ENG-MohamedEssam/universal-testing-machine/02-MCAL/03-ADC/ADC_interface.h

/************************************/
/*	Author  : Mohamed Essam			*/
/*	Date 	: 20/3/2022				*/
/*	Version : V01					*/
/************************************/
#ifndef ADC_INTERFACE_H
#define ADC_INTERFACE_H

void ADC_VoidInit(void);
u16 ADC_u16ReadChannelPoll(u16 Channel_u16Number);

#endif
