ENG-MohamedEssam/universal-testing-machine/02-MCAL/05-USART/USART_interface.h

#ifndef USART_INTERFACE_H
#define USART_INTERFACE_H

/* Defining Macros */

#define USART_U8_8_BIT_WORD					0
#define USART_U8_9_BIT_WORD					1

#define USART_U8_PARITY_DISABLED			0
#define USART_U8_PARITY_ENABLED				1

#define USART_U8_EVEN_PARITY				0
#define USART_U8_ODD_PARITY					1

#define USART_U8_PE_DISABLED				0
#define USART_U8_PE_ENABLED					1


/*******************/

void MUSART1_voidInit(void);

void MUSART1_voidTransmit(u8 *arr, u8 length);

u8 MUSART1_u8Receive(void);
u8 MUSART1_u8ReceiveNOinterrupt(void);

void MUSART1_voidSetcallBack(void (*setFunPtr)(void));
#endif
