ENG-MohamedEssam/universal-testing-machine/gui-code/icons_rc.py

# -*- coding: utf-8 -*-

# Resource object code
#
# Created by: The Resource Compiler for PyQt5 (Qt v5.15.2)
#
# WARNING! All changes made in this file will be lost!

from PyQt5 import QtCore

qt_resource_data = b"\
\x00\x00\x13\xcd\
\x89\
\x50\x4e\x47\x0d\x0a\x1a\x0a\x00\x00\x00\x0d\x49\x48\x44\x52\x00\
\x00\x00\xce\x00\x00\x00\xce\x08\x06\x00\x00\x00\x76\x1f\x3d\xc4\
\x00\x00\x00\x01\x73\x52\x47\x42\x01\xd9\xc9\x2c\x7f\x00\x00\x13\
\x87\x49\x44\x41\x54\x78\x9c\xed\xdd\x5b\x6c\x1c\xd7\x79\x07\xf0\
\xef\x9b\xcb\xee\x52\x92\x1b\xd9\xb2\x28\xc9\xb2\x15\xc5\x91\x5d\
\xdf\x63\xc7\x6e\x92\x26\x71\x10\xc7\x49\xdc\x26\x0d\x0a\x14\x75\
\x8b\x22\x4d\x9f\x82\xbc\xb4\x68\xd2\xb4\x68\x91\x56\x8d\x59\x34\
\x42\xdc\xa2\x68\xda\x24\x6d\x6c\x27\xa9\x5b\xa7\x7e\x28\x9d\x02\
\x79\x28\x8a\xbc\x04\x36\x90\x87\xc2\xb0\x54\x25\x6e\x56\x92\x45\
\x8a\xa6\x79\x13\x25\x8a\x36\xb9\xe4\x2e\xe7\x72\xce\xf9\xfa\xb0\
\xe7\x30\x43\x9a\x94\x38\xb4\x96\x3b\x3b\xfc\xff\x80\x05\x75\x59\
\x89\xb3\xc3\xf3\x9f\x73\x9d\x33\x44\x00\x00\x00\x00\x00\x00\x00\
\x00\x00\x00\x00\x00\x00\x00\x00\x00\x00\x00\x00\x00\x00\x00\x00\
\x00\x00\x00\x00\x00\x00\x00\x00\x00\x00\x00\x00\x00\x00\x70\x25\
\x22\xc2\x22\xc2\xdd\x3e\x0e\x80\x9e\x20\x22\x9e\x88\xf8\x99\xdf\
\xfb\xd9\xdf\x03\xc0\x2a\xcf\x3f\xff\x7c\xb0\xea\x8f\x96\x6b\x1c\
\x11\x09\x51\x03\x15\xc7\xea\x1f\x14\x74\x89\x88\xf8\xcc\xac\x2e\
\x5c\xb8\x70\xf3\xf5\xd7\x5f\xff\xbb\x69\x9a\xee\x32\xc6\x84\x7d\
\x7d\x7d\xf3\x13\x13\x13\xff\xc9\xcc\xff\x67\xdf\xc7\xcc\x2c\xdd\
\x3e\x5e\x80\xae\x13\x11\x8f\x88\x68\x74\x74\xf4\x23\xad\x56\xeb\
\x45\x59\x25\x8e\xe3\x93\x69\x9a\x3e\x2e\x22\x7d\xe8\xfb\x00\x10\
\xd1\xe0\xe0\xa0\x4f\x44\x74\xfc\xf8\xf1\x8f\x37\x9b\xcd\x49\x1b\
\x94\x48\x29\x95\x2a\xa5\xd2\x38\x8e\x63\x17\xa0\x37\xde\x78\xe3\
\xeb\x43\x43\x43\x55\x04\x07\xb6\x35\x17\x80\x7a\xbd\xfe\xab\x51\
\x14\x4d\xda\x7c\x24\xc6\x18\xd1\x5a\x8b\xd6\x5a\x94\x52\xa2\x94\
\x52\xc6\x98\x54\x29\x65\x26\x27\x27\xbf\x39\x30\x30\x50\xb1\xff\
\x16\x01\x82\xed\xc5\x35\xcf\xea\xf5\xfa\x6f\xc5\x71\x7c\xde\x86\
\x46\x67\x9b\x68\xc6\x98\xe5\xaf\x69\x9a\xba\x97\x11\x91\xff\x26\
\x22\x46\xb3\x0d\xb6\x15\x17\x9a\x93\x27\x4f\x7e\xac\xd9\x6c\x9e\
\x17\x11\x69\xb5\x5a\x66\x75\xdf\xc6\x18\xb3\x1c\x9e\x85\x85\x05\
\x99\x9b\x9b\x33\xb6\x29\x27\x17\x2f\x5e\xfc\x87\xcc\xff\x87\xf0\
\x40\xb9\xb9\x39\x99\x91\x91\x91\xdf\x5c\x58\x58\x98\x16\x11\xd1\
\x6d\xab\x73\xb3\x22\x38\xae\xd6\x89\xe3\x58\xe2\x38\xd6\xf6\xcf\
\x7e\xf0\xe8\xa3\x8f\xfa\x94\x09\x23\x40\xd9\xb0\x2b\xdc\x67\xce\
\x9c\x79\x28\x8e\xe3\x51\x11\x11\xa5\x94\x71\xfd\x19\x17\x94\xd5\
\xaf\x6c\x88\xec\xcb\x88\x88\xa4\x69\xaa\x2f\x5c\xb8\xf0\xcd\xc1\
\xc1\xc1\x3e\x42\x78\xa0\x6c\x44\x84\xdd\xe4\xe6\xe9\xd3\xa7\x1f\
\x71\xa1\x71\x35\xcd\x95\x82\xb3\xd6\x4b\x29\x65\x94\x52\x12\xc7\
\xb1\x7e\xe3\x8d\x37\xbe\x29\x22\xd7\x50\xa6\x46\x03\xe8\x75\xec\
\x0a\xf3\xb9\x73\xe7\x3e\x1a\xc7\xf1\x6b\xb6\xd9\xb5\x22\x34\x79\
\x82\x23\x22\x92\x24\x89\x2c\x2c\x2c\x88\x31\x26\xb5\x35\xd7\x53\
\xc7\x8f\x1f\x0f\x09\x7d\x1e\x28\x03\x57\xd3\x8c\x8c\x8c\x7c\x28\
\x8e\xe3\xba\x2d\xf4\xca\x0e\x33\x6f\x2a\x38\xd9\x97\xed\x1b\xa9\
\x38\x8e\xa3\x85\x85\x85\x6f\xcc\xcd\xcd\x5d\x4b\x08\x0f\xf4\x30\
\x16\x91\x80\x88\x68\x78\x78\xf8\x03\x49\x92\x0c\xd9\x3e\x7f\xba\
\xba\xf3\xff\x56\x5f\xd9\xff\x77\x7e\x7e\xfe\x9f\x5f\x7d\xf5\xd5\
\x1a\x86\xaa\xa1\x27\xb9\x15\x01\x67\xcf\x9e\x7d\x6f\x1c\xc7\xa7\
\xdc\xe4\xe6\x5a\xa3\x66\x6f\x35\x34\x49\x92\x88\x52\xca\x88\x48\
\xa2\x94\x4a\x5e\x7f\xfd\xf5\xbf\xf9\xdc\xe7\x3e\x87\x45\xa1\xd0\
\x5b\xb2\x6b\xcf\xa2\x28\x7a\xc5\xe6\x44\xad\x37\xdc\xfc\x56\x5f\
\xae\xc9\xe7\x82\xa4\x94\x4a\x94\x52\xff\x2e\x22\x15\x8c\xb4\x41\
\x4f\x70\x57\xf9\xa1\xa1\xa1\x77\x27\x49\xf2\xaa\x0d\x88\x5a\xd5\
\xac\xba\xea\x4d\x35\xd7\xdf\x31\x99\x6f\x32\x3b\x3b\xfb\xd7\x84\
\xfe\x0e\x14\x5d\xb6\xa6\x89\xe3\x78\xd8\x16\x68\xbd\x56\x68\xae\
\x66\x70\xd6\x08\x92\x11\x11\xa3\xb5\x4e\xb4\xd6\xdf\xcb\x1c\x1f\
\x02\x04\xc5\xe2\x0a\xe5\x4f\x7e\xf2\x93\xfb\x92\x24\x19\xb6\x7d\
\x0f\xb3\x5e\x68\x3a\x15\x9c\xd5\x94\x52\xe6\xd2\xa5\x4b\xc7\x5c\
\x9f\x0b\xe1\x81\xc2\x70\x85\xb2\x5e\xaf\xbf\x37\x4d\xd3\x33\x6e\
\x56\xdf\xf5\x3d\xd6\xd3\xc9\xe0\x2c\x2d\x2d\x89\x31\xc6\x68\xad\
\x25\x4d\xd3\xa5\xa9\xa9\xa9\x63\x22\xb2\x83\xb0\xc2\x00\x0a\x60\
\x79\x72\xf3\x95\x57\x5e\x79\x38\x8e\xe3\x57\x6d\xb9\xd5\xb2\x6a\
\xad\xd9\x56\x73\xdf\xdb\x06\xc7\x2d\x0e\xfd\x6e\xa6\xe6\x41\x78\
\x60\xeb\xd9\x79\x12\x57\xd3\x3c\x18\xc7\xf1\x69\x5b\x60\x75\xb6\
\xf0\x76\x33\x34\x99\x97\x0b\x4e\xab\xd1\x68\x7c\x35\xb3\x3c\x07\
\xcd\x36\xd8\x3a\x36\x34\x6e\x72\xf3\x23\x51\x14\xb9\xd1\xb3\x35\
\xef\xa7\xe9\x66\x70\x94\x52\xd2\x6a\xb5\xdc\x5f\xa5\x22\x22\xcd\
\x66\xf3\x89\xa7\x9f\x7e\xba\x46\x08\x0f\x6c\xa5\x4c\xf3\xec\x83\
\x6e\x19\x4d\x76\x45\x40\xb7\xad\x35\xcf\x23\x76\xa0\x20\x8e\xe3\
\xb4\xd9\x6c\x46\x73\x73\x73\xc7\x06\x07\x07\x2b\xdd\x3e\x97\xb0\
\x0d\x64\x6b\x1a\x3b\xb9\x79\xc6\x16\xd4\xc2\x84\x46\xd6\x19\x74\
\x70\x5a\xad\x96\x89\xa2\xc8\x24\x49\x12\x2f\x2d\x2d\x7d\x5b\x44\
\xaa\x22\x12\xa0\xe6\x81\x8e\x71\x35\x8d\x5d\x46\x33\x6a\xcb\x62\
\xb2\x6e\x09\xee\x92\x2b\x8d\xbc\xa5\x69\x6a\x92\x24\x49\x45\x44\
\x66\x66\x66\xfe\x84\x30\x58\x00\x9d\x32\x30\x30\xe0\x11\x11\x4d\
\x4f\x4f\x3f\xec\x86\x9c\x8b\x56\xd3\x38\x1b\x59\x65\x60\x87\xaa\
\xd3\x28\x8a\xe6\x9a\xcd\xe6\x3f\xd9\x1d\x43\x11\x1e\xb8\x7a\x5c\
\x68\xea\xf5\xfa\x7b\x5a\xad\xd6\xa8\x2d\x7c\x6a\xa3\x05\xb5\xa0\
\xc1\x59\x31\xc7\x34\x31\x31\xf1\x05\xc2\x60\x01\x5c\x2d\xee\x2a\
\xec\x6e\x0d\x48\xd3\x54\xb4\xd6\xfa\x4a\xcd\xa1\xa2\x06\x67\x9d\
\xa1\x6a\xb3\xb8\xb8\x38\x37\x39\x39\xf9\x07\x84\xf0\xc0\x5b\xe5\
\x26\x0b\xc7\xc7\xc7\x3f\xac\x94\x1a\xb1\x57\xe9\x0d\x87\xa6\x17\
\x82\xa3\xb5\x96\x46\xa3\xe1\x46\xdf\x62\x11\xf9\x1a\xa1\xcf\x03\
\x9b\x95\x59\xb0\x79\x9f\x9b\xdc\x5c\x5a\x5a\xd2\x6b\x85\xa1\x97\
\x83\xe3\x86\xab\xdd\x24\xa9\x52\x6a\x6e\x6a\x6a\xea\xb3\xb6\xcf\
\x83\x9b\xe1\x60\x63\xb2\x1b\x6b\x8c\x8f\x8f\xbf\xa7\xd5\x6a\x2d\
\xaf\x08\xc8\xde\xf3\xb2\xd1\x42\xdb\x0d\x79\x83\x93\xad\x7d\xec\
\xa6\x87\x3a\x4d\xd3\xbf\x72\xab\x23\x10\x9e\x37\xc3\x09\x59\x89\
\x45\xc4\x63\x66\x3d\x3e\x3e\x7e\xf7\x9e\x3d\x7b\x9e\xa9\x54\x2a\
\xf7\x32\x73\xca\xcc\xa1\x88\x10\x33\x13\xf3\xfa\xa7\x4d\x64\xe5\
\x83\x04\x2e\xf7\xde\x4e\x59\x7d\x0c\x79\xfe\x9d\x52\xca\x04\x41\
\xc0\x49\x92\xcc\x2c\x2e\x2e\xfe\xc5\xde\xbd\x7b\xbf\x43\x78\x4a\
\x02\x5c\x4e\x66\x72\xf3\xbe\x38\x8e\x4f\xd8\xab\x77\x9c\xa7\x16\
\xe9\xe5\x1a\x47\xda\x5b\x56\x49\xb3\xd9\xd4\xd2\x9e\x2c\xbd\x38\
\x3b\x3b\xfb\x79\x3b\x49\x8a\xe1\xea\x0c\xd4\x38\x96\x7d\x3e\x8d\
\x9e\x9c\x9c\xbc\xef\xfa\xeb\xaf\x7f\xa6\x52\xa9\xdc\x45\x44\x11\
\x11\xd5\x8c\x31\x2b\x6a\x8e\xb2\xd6\x38\xcc\x4c\x5a\x6b\xd2\x5a\
\x13\x33\x1b\xad\x35\x07\x41\xc0\xad\x56\xeb\x8b\x6f\x7b\xdb\xdb\
\xdc\xa0\x01\x6a\x1e\x04\xa7\xcd\x85\x66\x6c\x6c\xec\x97\xf6\xef\
\xdf\xff\x44\x18\x86\xef\x26\xa2\x94\x88\xdc\x3e\x65\xcb\xef\xed\
\x46\x10\xb6\x92\xfb\xac\xc6\x18\x12\x11\x13\x04\x01\xa5\x69\xfa\
\x3a\x33\x3f\x19\x04\xc1\x57\x89\x68\x89\x99\x4d\xb7\x8f\x13\xba\
\xcc\x35\x3f\xc6\xc7\xc7\xef\x89\xa2\xe8\xb4\x6d\xed\x14\x6e\x19\
\x4d\x37\x18\x63\x24\x49\x12\xe3\x16\x89\xce\xcc\xcc\x7c\x31\x7b\
\x3b\xc5\x76\xb6\xad\xdb\xac\xb6\xd9\x61\x46\x46\x46\xde\xb5\x6f\
\xdf\xbe\x67\xc2\x30\xbc\x2d\x8e\x63\xe5\x6a\x1a\x20\xe2\x36\x23\
\x22\xfa\x9a\x6b\xae\x39\x3a\x35\x35\xf5\xfb\xcc\xac\xb7\x7b\x7f\
\xa7\xdc\xed\x8e\xcb\x70\x6d\xf5\xc9\xc9\xc9\xf7\xf7\xf7\xf7\x3f\
\xc5\xcc\x77\x1a\x63\x52\x66\x0e\x7d\xdf\x2f\x7d\x93\x6c\xa3\xb2\
\xcd\x54\xad\x35\xa5\x69\xba\xd8\xd7\xd7\xf7\x1f\xcc\xfc\x59\x3b\
\x02\x89\x66\xdb\x76\xe1\xd6\x9e\x0d\x0d\x0d\xdd\xe7\x16\x6c\xc6\
\x71\xac\x36\x32\x4f\xb3\x9d\x69\xad\x97\x9f\xcf\x33\x35\x35\xf5\
\x87\x84\xe5\x39\xdb\x87\x5b\x46\xf3\xda\x6b\xaf\x7d\x50\x6b\x7d\
\xc6\xed\xf8\x6f\x67\xcf\xbb\x5d\x36\x0b\xcd\x6e\x3e\x62\x8c\x31\
\x46\xb5\x3b\x3e\x4f\xd3\xcf\xef\x53\xda\x56\x01\xda\x56\x8f\x6b\
\x77\x93\x9b\x63\x63\x63\x0f\x1c\x38\x70\xe0\xdb\x9e\xe7\xfd\x62\
\x9a\xa6\xc2\xcc\xde\x95\x26\x36\x81\xc8\xf7\xfd\xe5\x26\xae\xef\
\xfb\xbe\x52\xea\xb7\xa7\xa6\xa6\x86\x88\xe8\xab\xcc\x2c\xdb\xa9\
\xe9\xb6\x2d\x4a\x8a\xbd\x1a\x7a\xcc\xac\x27\x26\x26\xde\xb7\x77\
\xef\xde\xa7\x2b\x95\xca\x6d\xc6\x18\x4d\x44\x3e\x5d\x61\x98\x19\
\x81\xfa\x39\xb7\x7a\x42\x6c\x82\xd2\x34\x5d\x68\x34\x1a\x8f\xef\
\xd9\xb3\xe7\x6b\xcc\x1c\xb9\x8b\x53\xb7\x8f\xb3\xd3\x4a\x3f\x32\
\x22\x22\xfc\xc2\x0b\x2f\xf8\x76\x19\xcd\x87\xf7\xee\xdd\xfb\x2c\
\x33\xdf\x66\x07\x02\xb6\xfd\xb0\x6a\x5e\xee\x22\xc2\xcc\x6c\x27\
\x86\x77\xec\xd9\xb3\xe7\x58\x1c\xc7\x5f\x21\x22\xb1\x23\x6e\xb8\
\xd2\xf4\x3a\xb7\x8c\xa6\x5e\xaf\x7f\x30\x8e\xe3\xba\x69\xdf\x3a\
\x1c\x9b\xcc\x23\xd1\xaf\xf4\x6c\x1a\x58\x9b\xd6\x5a\xe2\x38\x36\
\x5a\x6b\x35\x37\x37\xf7\xfa\xfc\xfc\xfc\x51\x11\xd9\x25\x22\xec\
\x06\x60\xa0\xc7\x64\x37\xd6\x38\x7d\xfa\xf4\xfb\x97\x96\x96\x56\
\x3c\x9f\x26\xcf\xd3\xd0\xe0\xf2\xb4\xd6\x66\x69\x69\x49\x4b\xfb\
\xe9\xd8\x5f\x3e\x7e\xfc\x78\x58\xf6\x55\xd5\x65\x1e\x1c\xf0\x98\
\x59\x0d\x0d\x0d\xfd\xf2\x4d\x37\xdd\xf4\xed\x6a\xb5\x7a\xc4\xad\
\x3d\x23\xf4\x5b\xae\x0a\x37\xc7\xe3\x79\x1e\x57\xab\x55\x49\xd3\
\x34\xf5\x7d\xff\x8f\x6e\xb8\xe1\x86\x45\x66\xfe\x7b\x3b\x49\x5a\
\xca\x75\x6d\xa5\xac\x4e\x07\x07\x07\x7d\x66\xd6\xc3\xc3\xc3\x1f\
\x39\x74\xe8\xd0\xbf\x56\xab\xd5\x3b\x88\x28\x76\xa1\x81\xab\x4b\
\x44\x48\x44\xbc\x34\x4d\x03\x66\xde\x7d\xdd\x75\xd7\x3d\xd6\x68\
\x34\x1e\xb7\x2b\x0e\x4a\xb9\x0a\xa3\x74\x35\x8e\x1d\xec\xd1\xc3\
\xc3\xc3\x1f\x38\x74\xe8\xd0\xbf\x84\x61\xf8\x76\x11\x49\x98\xb9\
\xda\xed\x63\x2b\xbb\x30\x0c\xd9\x2e\x0c\xfd\x85\x4a\xa5\xf2\x67\
\x63\x63\x63\x97\x98\xf9\xef\xca\xb8\xa2\xba\x54\xed\x15\xf7\x03\
\x1a\x1b\x1b\x7b\xc4\xae\x72\x3e\x4c\x44\xcb\x43\xce\xd0\x59\xc6\
\x18\xf2\x3c\x8f\xb4\xd6\xe2\x79\x1e\x2b\xa5\xa2\x30\x0c\x9f\x63\
\xe6\xdf\xb3\x65\xad\x34\xe1\x29\x4d\x53\xcd\xce\x1f\xc8\xa9\x53\
\xa7\x3e\x74\xed\xb5\xd7\x3e\x15\x86\xe1\x61\x69\x37\xc2\x11\x9a\
\x2d\x90\x99\xdf\x21\xcf\xf3\x98\x99\x25\x0c\xc3\x1a\x11\x7d\x66\
\x6c\x6c\xec\xcf\x33\xa1\x29\xc5\xc5\xba\x14\xc1\xb1\x7d\x1a\x73\
\xe6\xcc\x99\x87\x8e\x1c\x39\xf2\x4c\xad\x56\x3b\x44\x44\x86\x31\
\x02\xd0\x35\xc6\x18\x5e\x5c\x5c\x14\xad\x35\xf5\xf7\xf7\xff\xe5\
\xc8\xc8\xc8\x51\x7b\x3b\x82\x94\x61\x65\x75\xaf\x17\x2c\x76\xb7\
\x06\x8c\x8e\x8e\x7e\xf2\xe0\xc1\x83\x4f\x05\x41\x70\x83\xdd\xa5\
\xd2\x0b\x82\x00\xa3\x67\x5b\x64\xf5\x5d\xa7\x4a\x29\x12\x11\xf2\
\x7d\x9f\xa2\x28\x92\x9d\x3b\x77\xb2\xd6\xfa\xd9\x20\x08\x3e\x63\
\xc3\xd3\xd3\xfd\x9e\x9e\x4d\xbe\x9d\xa7\xf1\x98\xd9\xfc\xec\x67\
\x3f\x7b\x68\xff\xfe\xfd\x5f\x0f\x82\xe0\x06\xad\xb5\xd1\x5a\x7b\
\xbe\x8f\x16\x5a\x37\xf9\xbe\x4f\x41\x10\x90\x31\x86\xaa\xd5\xf6\
\xb8\x8c\x52\xea\x37\x2e\x5c\xb8\x70\x54\x44\x76\x11\x56\x56\x6f\
\xbd\xec\xe4\xe6\xb9\x73\xe7\x3e\x11\xc7\xf1\xa4\xd8\xc7\x07\x26\
\x49\x82\x49\xcb\x2e\xb8\xd2\xb6\x53\xf6\xd7\xa9\xb4\x9f\x8d\xfa\
\xad\x27\x9f\x7c\x32\x14\x11\xaf\x57\xc3\xd3\x8b\x07\xbd\xbc\x85\
\xd3\xb9\x73\xe7\x1e\x3e\x78\xf0\xe0\x13\x61\x18\xbe\xb3\xbd\x74\
\xca\xf8\xcc\x4c\x9e\xd7\xb3\x15\x69\xcf\xba\xdc\x06\x21\xc6\x18\
\x37\xe2\x26\x44\xa4\x95\x52\xad\xf9\xf9\xf9\x63\xfb\xf6\xed\xfb\
\x5b\xea\xd1\x0d\x40\x7a\x2a\x38\xf6\xea\xe4\x33\xb3\x3a\x7b\xf6\
\xec\xaf\x1d\x3e\x7c\xf8\x1f\xc3\x30\xbc\x39\x49\x92\x34\x0c\xc3\
\xd0\x8e\xe8\x74\xfb\x30\xb7\xa5\x2b\x05\x87\x6c\xf3\xcd\x18\x23\
\xcc\xcc\x51\x14\x2d\x7a\x9e\xf7\xdd\x6a\xb5\xfa\x25\xbb\x31\x8a\
\xee\xa5\xf0\xf4\x54\x29\xb3\xab\x9c\x55\xbd\x5e\xff\x95\x43\x87\
\x0e\x3d\x15\x04\xc1\xcd\xc6\x98\x34\x08\x82\xd0\xfd\x70\xa0\x78\
\x3c\xcf\x23\x66\x26\xbb\x9a\x9a\xb5\xd6\x52\xab\xd5\xfa\xaa\xd5\
\xea\xe7\x67\x67\x67\xff\x98\x99\x55\xaf\x5d\xc4\x7b\xa6\x07\x2d\
\x22\xde\x3b\xde\xf1\x0e\x7d\xea\xd4\xa9\x4f\xde\x7c\xf3\xcd\x4f\
\xd4\x6a\xb5\x1b\xd3\x34\x55\x9e\xe7\xad\xd8\x61\x13\xa3\x68\xc5\
\x97\xb9\x25\x41\x11\xd1\xfb\x8e\x1e\x3d\x7a\x30\x0c\xc3\x1f\x32\
\x33\xbf\xf0\xc2\x0b\x3d\x53\xeb\x14\x9e\x5b\xa2\xfe\xd3\x9f\xfe\
\xf4\xe1\x66\xb3\x79\x5e\xda\xb7\xf1\xea\xec\xad\x01\x58\xc9\xdc\
\x5d\x79\x77\x0d\x8d\xe3\x58\x94\x52\x12\x45\x91\x88\x88\x5c\xbc\
\x78\xf1\x4b\x6e\xa4\xb4\xdb\xe5\x6d\x23\x0a\x7f\x79\x76\x1d\xc7\
\x13\x27\x4e\x3c\x72\xc7\x1d\x77\x7c\xa7\x56\xab\xdd\xe8\xee\xdc\
\x74\x33\xd5\x99\x9b\xab\xba\x7d\xb8\xdb\xd6\xe5\xfa\x38\xd9\x9f\
\x93\x7b\x5f\x66\xe3\x43\x09\x82\x40\x96\x96\x96\x92\x8b\x17\x2f\
\x7e\xe5\xf0\xe1\xc3\xc7\x7a\x61\xb0\xa0\xd0\xe9\x1e\x18\x18\xf0\
\x98\x59\xce\x9c\x39\xf3\xe8\x9d\x77\xde\xf9\x6f\x61\x18\xde\x68\
\x8c\x59\xb1\x8c\x06\x4d\xb4\xde\xb0\xfa\xe2\xe6\xbe\xfa\xbe\xcf\
\x49\x92\x78\xd5\x6a\xb5\x76\xd3\x4d\x37\x3d\x76\xfe\xfc\xf9\x6f\
\xd9\xd0\x14\xfa\x07\x5a\xd8\x83\x73\x93\x9b\x2f\xbd\xf4\xd2\x27\
\xee\xb9\xe7\x9e\xef\x54\x2a\x95\x03\x22\x62\xb2\x61\x5f\x5d\xe3\
\x40\xf7\x5c\xa9\xc6\x59\xef\xbd\x22\x42\x69\x9a\x12\x11\x49\xb5\
\x5a\x65\xa5\x94\x9a\x99\x99\x79\xec\xc0\x81\x03\xee\xb6\x84\x42\
\xd6\x3e\x45\xbc\xad\x60\x79\x9e\x66\x74\x74\xf4\xd3\xfb\xf6\xed\
\xfb\x7a\x10\x04\xd7\xd9\x76\xb4\x87\xe1\xe6\xf2\x09\xc3\x90\x3c\
\xcf\x63\xad\x35\x11\x91\x77\xe0\xc0\x81\x63\x5a\xeb\x77\x0d\x0c\
\x0c\x7c\x9a\x99\xd5\x76\xda\x3d\x67\xb3\xd8\xed\x7b\xf6\xf2\xcb\
\x2f\xff\xfa\xd2\xd2\xd2\x94\x0d\x8c\x5e\xdd\x09\x85\xde\xb7\xce\
\xc0\x81\x11\x11\x89\xa2\x28\x99\x98\x98\xf8\x4a\xbd\x5e\xaf\xb8\
\xb2\xd1\xdd\xa2\x59\x60\x6e\x44\xe5\xe4\xc9\x93\x1f\x6b\x36\x9b\
\xe3\x26\xf3\xcc\xcd\xd5\x27\x1b\x7a\xdf\x7a\x3f\xc7\x34\x4d\x8d\
\x52\xca\x44\x51\x94\x9e\x3f\x7f\xfe\x4f\xdd\xf2\x9c\x22\x85\xa7\
\x30\x07\xe2\xaa\xe3\x89\x89\x89\x5b\x77\xef\xde\xfd\xfd\x9d\x3b\
\x77\xde\x1d\x45\x51\x1a\x04\x41\x18\x04\x45\x6c\x51\x42\xa7\xa4\
\x69\x4a\x69\x9a\xea\x1d\x3b\x76\x50\x1c\xc7\xaf\x5f\xba\x74\xe9\
\x77\x6e\xbc\xf1\xc6\x1f\x15\xa9\xc9\x56\xa4\x0e\x03\x13\x11\xf5\
\xf7\xf7\x7f\x74\xe7\xce\x9d\x77\x13\x51\xe4\xfb\x7e\x88\x8e\xff\
\xf6\x13\x86\x21\xed\xd8\xb1\xc3\x17\x11\x5d\xad\x56\xf7\xee\xd9\
\xb3\xe7\xc3\x76\xf3\x95\x42\x84\x86\x8a\x12\x1c\xb7\x4f\x00\xb5\
\xaf\x36\x7b\x45\xc4\x28\xa5\x7c\xdf\xf7\xc9\xf3\x3c\xb7\x19\xc4\
\xa6\x9f\x34\x06\xbd\x25\xf3\xb3\x66\x69\x3f\xed\x7b\xf7\xfd\xf7\
\xdf\xef\x53\x81\x6e\x45\x28\x44\x70\xb2\xc3\x8d\x22\x12\x63\x6e\
\x06\x32\x98\x88\x38\x8a\xa2\x42\x15\x86\x42\x04\x87\xec\xe3\x04\
\x89\x88\x6a\xb5\xda\xc5\xf6\xba\x40\xaf\x30\xd5\x32\x6c\x3d\x7b\
\xd1\x34\xcc\x2c\x3b\x77\xee\x9c\xae\xd7\xeb\x69\x91\xe6\x74\x0a\
\x13\x9c\xe7\x9e\x7b\x8e\x88\x88\x5e\x7c\xf1\xc5\x1f\x2d\x2c\x2c\
\xfc\x0f\x33\x57\x99\x59\xb9\x87\xb9\xda\x67\x52\x76\xad\xb9\x96\
\x24\x09\x29\xa5\xba\xf2\xbd\x3b\xa9\x68\x9f\x49\x44\x48\x6b\x4d\
\x51\x14\x89\x31\xa6\x9a\x24\x89\x34\x1a\x8d\x93\x76\xb3\x8f\xc2\
\x94\xd7\x42\x55\x7f\x6e\xd4\xe4\xc7\x3f\xfe\xf1\x7b\xef\xbd\xf7\
\xde\xa7\x77\xed\xda\x75\x7b\xb7\x8f\xa9\xec\xa2\x28\x22\xcf\xf3\
\xa8\x52\xa9\x6c\xe0\xdd\x5b\xc3\xad\x06\x69\x34\x1a\x17\x2f\x5c\
\xb8\xf0\x85\x46\xa3\xf1\xfd\xfb\xef\xbf\x5f\x17\x69\x70\xa0\x50\
\xe3\xbc\xcc\x6c\x06\x06\x06\xbc\x07\x1f\x7c\xf0\xc5\x97\x5f\x7e\
\xf9\x33\xbb\x77\xef\xfe\xf2\xfe\xfd\xfb\x1f\x0a\xc3\x70\xf9\x7e\
\x9b\xec\x53\x91\x57\xff\xf3\x35\xfe\xbf\x95\xbf\xf7\x78\xbd\x9d\
\xbd\x96\xff\x34\xd3\x14\x58\xfe\x9a\xe9\x6f\x05\x22\x52\x2d\x4b\
\xdf\x4b\x44\x96\x03\x23\x22\x29\x11\xa9\xcc\x3a\xb1\xec\x99\xca\
\xfe\x3a\xfb\x10\xa9\x37\x9d\x88\x75\x3a\xef\x57\x6c\x26\xd8\xef\
\x2b\xd4\x7e\x64\xa2\x99\x9d\x9d\x3d\xb1\xb8\xb8\xf8\xf8\xad\xb7\
\xde\xfa\xc3\xfc\x9f\xac\xf3\x0a\x5f\x02\x86\x86\x86\xde\xa9\xb5\
\xbe\x96\xda\xcd\x8a\x37\x1d\xaf\xd6\xda\x73\x7f\xb7\x63\xc7\x0e\
\x8e\xe3\xd8\xd7\x5a\xb3\xdd\x1a\x6a\xc5\xfb\x35\x6b\xf6\xc5\x5f\
\x0e\x84\xf8\x22\x9e\xf1\x8c\xe7\x79\x9a\x88\xc4\xf7\x7d\xe3\xfb\
\xbe\x11\x11\x09\x82\xc0\x18\x63\x4c\x10\x04\xc6\x7e\x1f\xc5\xcc\
\x1f\x3f\x72\xe4\xc8\xd7\x98\xb9\x30\x4d\x86\xb7\xca\xde\x17\x43\
\xa3\xa3\xa3\xdf\x6b\xb5\x5a\xdf\xa8\x56\xab\x6b\x3d\xdb\x66\x79\
\x4f\x34\xa5\x14\x3b\x4a\x29\x56\x4a\x79\x61\xd8\xde\xe5\x56\x6b\
\xed\xb9\x9f\x51\x76\x6b\x2e\x7b\x3e\xc5\x9d\x5b\xa5\x14\xd5\x6a\
\x35\xe3\xfe\x2e\xfb\x1e\x22\x92\xbe\xbe\xbe\xe6\xf4\xf4\xf4\xab\
\x0f\x3c\xf0\x40\xba\x25\x27\x61\x13\x0a\x55\xe3\xac\xe5\x96\x5b\
\x6e\x39\xd7\xed\x63\x70\xce\x9e\x3d\xdb\x6f\x87\xcd\x4b\x13\x1c\
\x3b\xdc\x2f\xbe\xef\x0f\xdf\x75\xd7\x5d\x2f\x75\xfb\x78\x7a\x45\
\xe1\x83\x63\x9b\x06\xdd\x3e\x06\x22\x22\x9a\x9a\x9a\xd2\x65\xda\
\xc6\x35\xcb\x06\x88\xd7\x68\xa6\x75\x45\x51\x46\xcf\xd6\xd3\x0b\
\xc1\x91\xa2\xf4\x29\xc6\xc7\xc7\x8b\x35\x04\x75\xf5\xb0\xb4\xc7\
\x7a\xc5\x76\xcc\x0b\x5d\x68\x8b\xa0\x34\x4d\x8e\xad\x90\x24\x89\
\x2e\x4a\xed\xd7\x01\x85\x19\xb1\xea\x05\x08\x4e\x0e\xb5\x5a\xad\
\xa7\xb6\x30\xda\x28\x66\x16\xbb\x71\x06\x6c\x10\x82\x93\x83\xdd\
\xeb\xa0\x74\xc1\xa1\x76\x1f\xa7\xf4\x4f\x8a\xbe\x9a\x10\x9c\x1c\
\xc2\x30\x34\x52\xd2\xb6\x9a\xbd\x2d\x1d\x36\x08\xc1\xc9\x21\x0c\
\x43\x53\xd6\x1a\xa7\xc4\x9f\xab\x23\x10\x9c\x1c\x6c\x6d\x53\xc6\
\x02\x26\x58\x54\x9b\x0f\x82\x93\x4f\x19\x43\x43\xd4\x9e\xf5\x2f\
\xed\x67\xeb\x04\x04\x27\x07\x37\xd7\xd1\xed\xe3\xe8\x04\xd4\x38\
\xf9\x20\x38\x39\x94\xf9\xd1\x88\x22\x82\x51\xb5\x1c\x10\x9c\xfc\
\x4a\x19\x9e\x32\x5f\x14\x3a\x01\xc1\x01\xa2\x76\x1f\x07\xc1\xc9\
\x01\xc1\x01\x22\xfb\xd0\x27\xd8\x38\x04\x27\x1f\x5c\x95\x81\x08\
\xc1\x81\x0c\x94\x85\x1c\x70\xb2\x00\x36\x01\xc1\x01\xa2\xb5\xf7\
\x70\x80\xcb\x40\x70\x00\x36\x01\xc1\xc9\xaf\x94\x2b\x07\x4a\xfc\
\xb9\x3a\x02\xc1\xc9\xa7\xb4\x85\x0b\x4b\x6e\xf2\x41\x70\x80\xa8\
\xbd\x72\x00\x4b\x6e\x72\x40\x70\x72\x28\xf1\x6d\x05\x44\x44\x08\
\x4e\x0e\x08\x4e\x0e\xd5\x6a\xb5\xac\xa1\x91\xb2\xde\xd9\xda\x29\
\x08\x4e\x0e\x8d\x46\x83\xca\x5a\xe3\xa0\x8f\x93\x0f\x82\x93\x43\
\xa5\x52\x29\x65\x53\x4d\x44\xc8\xf3\x3c\xec\x72\x93\x03\x82\x93\
\x4f\x69\x5b\x34\x5a\x6b\xd4\x38\x39\x20\x38\xf9\x95\x31\x39\x62\
\x37\x22\x81\x0d\x42\x70\x80\x08\x7b\x0e\xe4\x86\xe0\x80\x83\xe0\
\xe4\x80\xe0\xe4\x50\xda\x0e\x4e\xc9\x3f\x5b\x27\x20\x38\xf9\x95\
\xb5\x80\x95\xf5\x73\x75\x04\x82\x03\xb0\x09\x08\x0e\xc0\x26\x20\
\x38\xf9\x95\xb2\x49\x53\xa6\xe7\x9a\x6e\x05\x9c\xac\x9c\xca\xba\
\xfd\x98\xef\xfb\xe5\xfc\x60\x1d\x82\xe0\xe4\x57\xc6\x02\xc6\xc6\
\x18\xec\x0f\x95\x03\x82\x93\x43\xc9\x77\xbb\x2c\xf3\x67\xbb\xea\
\x10\x9c\xfc\xca\x5a\xc0\x50\x16\x72\xc0\xc9\xca\xa7\x94\xa1\x61\
\x66\x12\x91\x5e\x78\x02\x79\x61\x20\x38\x39\x54\xab\xd5\x6e\x1f\
\x42\xa7\xa0\x8f\x93\x13\x82\x93\x43\x92\x24\x5c\xd6\x5a\x07\xc1\
\xc9\x07\xc1\xc9\xa7\x94\xa1\xa1\x76\x73\x0d\xc1\xc9\x01\xc1\x01\
\x22\x22\x52\x4a\xa1\x8f\x93\x03\x82\x93\x83\x1d\x8e\x2e\x63\xad\
\xc3\x98\x00\xcd\x07\xc1\xc9\xa7\xcc\x85\xab\xcc\x9f\xed\xaa\x43\
\x70\x72\x48\xd3\xb4\xac\x35\x0e\xe4\x84\xe0\x00\x51\x7b\x54\x0d\
\x65\x21\x07\x9c\xac\x7c\x50\xe3\x00\x11\x82\x03\xb0\x39\x08\x4e\
\x0e\xe8\xe3\x80\x83\xe0\x00\x51\x7b\xb3\x0e\xcc\xe3\xe4\x80\xe0\
\xe4\x24\x22\xa8\x71\x00\xc1\xc9\x03\xf7\xe3\x80\x83\xe0\xe4\x57\
\xca\x02\x26\x22\x28\x0b\x39\xe0\x64\xe5\x53\xca\xd0\xd8\xcf\x85\
\x45\x9e\x39\x20\x38\xf9\x95\x32\x3c\xa8\x71\xf2\xc1\xc9\x02\xa2\
\x76\x70\x50\xe3\xe4\x80\xe0\xe4\x50\xe6\xc1\x01\xdc\xc8\x96\x0f\
\x82\x93\x5f\x29\xc3\x83\x1b\xd9\xf2\x41\x70\x72\x50\x4a\x95\xf6\
\x7c\xa1\x8f\x93\x0f\x4e\x56\x3e\xa5\xac\x6d\x08\x35\x4e\x6e\x08\
\x4e\x0e\x9e\xe7\x79\x65\x0d\x8f\x31\xa6\x94\x9f\xab\x53\x10\x9c\
\x7c\x4a\x5b\xb8\xb0\xe9\x7a\x3e\x38\x59\x39\x30\xb3\x57\xd6\x81\
\x35\xd4\x38\xf9\x20\x38\x39\x24\x49\x52\xda\x27\x33\x33\x73\x69\
\x3f\x5b\x27\x20\x38\x39\x84\x61\xd8\xed\x43\xe8\x98\x32\xcf\x51\
\x75\x02\x82\x93\x43\x89\xb7\x87\xc2\x9e\x03\x39\xe1\x64\x01\x6c\
\x02\x82\x93\x43\x99\x27\x40\xcb\xfa\x88\xc6\x4e\x29\x73\x41\x00\
\xe8\x18\x04\x07\x60\x13\x10\x9c\x7c\xd0\x9c\x01\x22\x04\x07\x32\
\x4a\x39\x5a\xd8\x29\x08\x4e\x0e\xcc\x9c\x1a\x83\x79\x42\x40\x70\
\x72\xf3\x3c\x8f\x45\x84\x44\xca\xd1\x6a\xb3\x17\x02\x21\xa2\xf9\
\x6e\x1f\x4b\x2f\x41\x70\x72\xe8\xeb\xeb\x9b\x8b\xe3\x38\x32\xc6\
\x68\xfa\x79\xa1\xeb\x69\x5a\x6b\xa3\xb5\x66\x11\x39\xd1\xed\x63\
\xe9\x25\x08\x4e\x0e\xfd\xfd\xfd\xa3\xd3\xd3\xd3\x2f\xf9\xbe\xef\
\x8b\x48\x6a\x8c\x91\x4c\xed\x23\x9b\x7c\x6d\xd6\xa6\xbe\x5f\xe6\
\x58\x0d\x11\xa5\x61\x18\x7a\xad\x56\x6b\xd6\xf7\xfd\x13\xd4\x6e\
\x8e\x96\xa3\x2a\xed\x30\x04\x27\x07\x66\x36\xcd\x66\xf3\xb1\x56\
\xab\xf5\xbf\x9e\xe7\x85\x41\x10\x30\x11\xa5\xf6\xa5\x6d\x61\x74\
\x5f\x37\xfa\x4a\x37\xf9\xca\xf3\x3d\x96\x5f\xcc\xec\x8e\xd5\x23\
\xa2\xb0\xd9\x6c\x4e\xcf\xcf\xcf\x7f\xe1\xc8\x91\x23\xe3\xdd\x3e\
\xbf\x50\x72\xc7\x8f\x1f\xbf\x7b\x7e\x7e\xfe\x07\x33\x33\x33\xd3\
\x92\x61\x8c\xb9\xe2\xab\x53\xb4\xd6\x62\x8c\x11\xad\xf5\x9b\x5e\
\x4a\x29\x51\x4a\xad\x78\xff\xfc\xfc\xfc\x64\xa3\xd1\xf8\xaf\xd3\
\xa7\x4f\x3f\x42\xd8\xda\x37\x37\x9c\xac\x9c\x44\xc4\x67\x66\xfd\
\xec\xb3\xcf\x5e\x7b\xfb\xed\xb7\xdf\x76\xcb\x2d\xb7\xdc\xb0\x6b\
\xd7\xae\x5a\xa3\xd1\x10\xad\xb5\xa4\x69\xea\xfb\xbe\x4f\x5a\x6b\
\x26\x22\xf2\xfd\x15\x77\x24\xaf\x38\xdf\xb5\x5a\x8d\x98\xf9\x4d\
\x4b\xae\x3d\xcf\x13\xca\xdc\x23\x63\x57\x65\x7b\xf6\xef\xc8\x18\
\x43\x51\x14\xa5\x44\xc4\x5a\x6b\x22\x22\xc9\x7c\x15\xdf\xf7\x97\
\x9b\x81\xf6\xff\x32\xbe\xef\x8b\xd6\x9a\x2a\x95\x4a\x20\x22\xc9\
\xc4\xc4\xc4\xf8\xf0\xf0\xf0\xd0\xa7\x3e\xf5\xa9\x4b\xee\x33\x75\
\xf2\xbc\x01\x94\x6a\x63\x8b\xc1\xc1\x41\xec\x35\x00\x5b\x67\x60\
\x60\xc0\x13\x11\xff\xf9\xe7\x9f\x0f\x44\xc4\xb7\x2f\xaf\xc8\xaf\
\xc1\xc1\x41\x77\x9c\xfe\xe0\xe0\xa0\x3f\x30\x30\x50\x9a\x0b\x00\
\x00\x00\x00\x00\x00\x00\x00\x00\x00\x00\x00\x00\x00\x00\x00\x00\
\x00\x00\x00\x00\x00\x00\x00\x00\x00\x00\x00\x00\x00\x00\x00\x00\
\x00\x00\x00\x00\x6c\x6b\xff\x0f\x73\x7f\xe3\x0c\xd9\xbf\xa8\xb7\
\x00\x00\x00\x00\x49\x45\x4e\x44\xae\x42\x60\x82\
\x00\x00\x10\x2c\
\x89\
\x50\x4e\x47\x0d\x0a\x1a\x0a\x00\x00\x00\x0d\x49\x48\x44\x52\x00\
\x00\x00\xce\x00\x00\x00\xce\x08\x04\x00\x00\x00\xdc\x16\xf5\x4f\
\x00\x00\x00\x04\x67\x41\x4d\x41\x00\x00\xb1\x8f\x0b\xfc\x61\x05\
\x00\x00\x00\x20\x63\x48\x52\x4d\x00\x00\x7a\x26\x00\x00\x80\x84\
\x00\x00\xfa\x00\x00\x00\x80\xe8\x00\x00\x75\x30\x00\x00\xea\x60\
\x00\x00\x3a\x98\x00\x00\x17\x70\x9c\xba\x51\x3c\x00\x00\x00\x02\
\x62\x4b\x47\x44\x00\xff\x87\x8f\xcc\xbf\x00\x00\x00\x07\x74\x49\
\x4d\x45\x07\xe6\x03\x18\x0c\x00\x1a\x2a\xbc\x57\x81\x00\x00\x00\
\x01\x6f\x72\x4e\x54\x01\xcf\xa2\x77\x9a\x00\x00\x0f\x27\x49\x44\
\x41\x54\x78\xda\xed\x9d\x7b\x90\x1c\xc5\x7d\xc7\xbf\x3d\xb3\x7b\
\xa7\x67\x2c\xcb\x31\x8e\x9d\xc2\x29\xfc\x28\x10\x48\xa2\x2c\x19\
\x88\xb1\x43\x10\x38\x06\x51\x42\x52\xb0\x7d\xa0\xb8\xc4\xc3\xa5\
\x60\x07\xe2\xc4\x55\xc9\x1f\xa9\x94\x2b\xb9\x38\xae\xf2\x5f\xc9\
\x1f\x2e\x27\xe5\x54\xd9\x04\xbb\x12\x08\x17\x8c\xc1\x08\x74\xb2\
\x1e\x87\x90\xc4\x21\x74\x42\x96\xc4\x9d\x64\x49\xb1\x04\x25\xa1\
\xc7\xdd\xe9\xf6\x79\x7b\xbb\xd3\xdd\xdf\xfc\x31\x7b\x77\x73\x77\
\xbb\xa7\x5d\x69\x76\xb6\x77\xb7\x3f\x5b\x75\x3b\xb7\x3b\xdb\x33\
\xd3\x9f\xe9\x9e\x9e\xee\xdf\xcc\x00\x16\x8b\xc5\x62\xb1\x58\x2c\
\x16\x8b\xc5\x62\xb1\x58\x2c\x16\x8b\xc5\x62\xb1\x58\x2c\x16\x8b\
\xc5\x62\xb1\x58\x2c\x16\x8b\xc5\xd2\x74\x88\x7a\xaf\xc0\xe5\xa0\
\xf8\xa7\x9a\xad\xe3\x3f\x52\xb0\xde\xdb\xd7\xb0\x30\x46\xb7\xa6\
\xe9\x8b\xbe\x38\x0d\xde\x3d\x63\xf5\x5e\x81\x72\x50\xc0\x15\x12\
\xd8\x38\x7f\xc9\xbc\x94\x04\x3e\x80\xbc\x68\x13\x40\x61\x22\x33\
\xf3\xa2\x9d\x40\xdc\xf5\xca\x64\x6f\x9c\x42\x16\x04\xd0\x56\x2c\
\x1d\x69\x00\x40\x3b\x81\x76\xe6\xc5\xfc\x58\x56\x8a\x4b\xf0\x00\
\x3a\x42\xd7\x7b\x6b\x4b\x63\xe8\x7e\x43\x21\x08\xf4\xad\x5f\xb6\
\x62\xf4\xba\xfc\x07\x9d\x02\x20\x04\x84\x16\xfe\x7e\xae\x04\x00\
\x08\xe1\xd0\xa1\x6c\x0b\xee\xfb\xce\x44\x35\x45\x00\x4e\x61\x6a\
\xa2\x00\x20\x48\x38\x5a\x3b\x6c\x8b\x8f\xcd\x3b\xfd\xde\x3b\x37\
\x3c\x0d\x43\xd5\x18\x0b\x1d\x2e\x1c\xfb\xe1\x60\x8e\x35\x66\x8c\
\xb9\x67\x07\x3f\x66\xea\x2e\x6a\x68\xb5\x26\x74\xdf\x13\x2b\x9f\
\x6c\x27\x0b\x70\x8a\xbb\x3c\x04\x4a\x15\x74\x22\x78\x4c\x17\x81\
\xcf\xfd\xef\x4a\x1f\xf1\x05\x1c\x10\x42\xb7\xb9\xe2\xa1\x61\x87\
\x1b\xcc\x6c\x18\x18\xba\xcf\x0c\x7e\xb4\x7d\x60\xc1\x7c\xe1\x4e\
\xaa\x29\xbf\xc2\xe5\xe5\x4c\xff\x36\xf8\x89\x3f\x27\xe9\xca\x4c\
\xfc\xc4\x9d\x2b\x76\xf9\x15\xa9\x59\x38\xf5\x5e\x81\x12\x08\xe0\
\xc2\xf2\x85\x8b\x44\xbc\xb2\xb5\x13\x81\xd7\xcc\x4f\x9d\x19\x2f\
\x17\x2e\x5c\x38\xfe\xb7\x02\xf1\x05\x28\xdc\x53\xef\x4d\x2e\x8d\
\x89\x72\x00\x14\x16\xb2\xe6\xfb\xf1\xa4\xce\xdf\xb9\xb6\xde\xdb\
\x5b\x1a\x43\xe5\xb8\x14\x11\x55\xb8\x04\xe0\xcd\xab\xf7\xf6\x96\
\xc6\x50\x39\xb5\x2f\x37\xe3\x28\x00\x42\xd5\x7b\x7b\x4b\x63\xa8\
\x1c\x44\x26\xc7\xd4\x0c\x30\x78\xdd\xa2\x2b\x39\x00\x8c\x6d\xb3\
\x1a\x2a\x27\x5a\x4c\xed\x5f\xb3\x72\x00\x98\xda\xb7\x66\xaa\x1c\
\xe3\x4e\x08\xeb\x81\xa9\x72\x22\xc3\xd0\x1a\x0d\x80\xb1\x72\x1c\
\x43\x2b\x9a\x68\x31\x50\x0e\x01\xc8\xb9\x51\x2e\xd1\x35\x30\x17\
\x00\x23\xe5\x00\x80\x8e\x6c\xbd\x04\x6c\x6b\xad\xda\xd5\xb2\x0d\
\x02\x18\x3b\x9e\x13\x6c\xad\x19\xba\x5b\x47\x80\x2d\x39\x06\x63\
\xa0\x1c\x81\xc8\xbb\x6f\x0c\xc5\x40\x39\x00\xe0\x5a\x39\x30\x56\
\x8e\xad\xd6\x00\x63\xe5\x44\xdb\x7d\x63\x5e\xf4\x80\x8f\xa9\x72\
\x2c\x30\x57\x4e\xeb\xb6\x9f\x03\x98\x2a\xc7\x02\x63\xe5\xe8\xc8\
\x4a\x0e\x61\xee\xf8\x84\xa1\x72\xa2\xc5\xf6\xad\x55\x45\x6c\x34\
\xca\xa5\xd1\x46\xdf\x54\x83\x32\x74\x5f\x8e\x16\x43\xe5\x44\x15\
\x52\x68\xee\xf1\x06\x30\x56\x8e\x6d\x4a\x03\xe6\xca\x89\x94\xda\
\x5e\xdc\x78\xe5\x18\x2a\x27\xba\xa6\x34\x60\x6e\xd5\x66\xa8\x9c\
\x68\x31\x35\x9c\xc4\xca\x31\x18\x43\xe5\x44\x3b\x64\xa0\xed\x31\
\xc7\x5c\x1c\x7b\x12\x5a\x15\xa6\x1e\xa3\x23\xc5\x54\x39\x16\x18\
\x2b\xc7\x06\x78\x00\xe6\xca\x89\xf4\x10\x1d\x5d\x67\x51\x75\x18\
\x2a\x47\xcf\x89\x6a\x49\x62\xe2\x8f\x79\x18\x2a\x27\xda\x6a\xcd\
\x06\x78\x18\x8a\x00\x4d\x2d\x38\x56\x8e\xc9\xad\x76\x2b\xc7\x60\
\x0c\x95\x13\x71\x38\xae\xa1\x85\xc7\x50\x39\xc6\xe6\x57\xa4\x18\
\x2a\xc7\xc6\x4a\x03\xc6\xca\xb1\xd5\x1a\x60\xac\x1c\x0b\x60\xe5\
\x18\x7c\x96\x63\xac\x1c\x15\x61\x96\x09\x18\x3a\x9c\x63\xaa\x9c\
\x68\xc7\x26\x6d\xf7\x4d\x55\xb8\xf9\xa8\x96\xc4\x89\x3f\xe6\x61\
\xa8\x1c\x21\x23\x5d\x9a\x95\x53\x0d\xd1\xdd\xc1\xc3\x64\x4c\xcd\
\x04\x73\x9b\x50\x11\x62\xa8\x9c\x68\x23\x3e\x4d\xc5\x50\x39\xd1\
\x96\x1c\x1b\xb7\x66\x30\x36\x6e\xcd\x64\x6c\x6b\xad\x1a\x22\xbe\
\xca\xc0\xd0\x5c\x30\x74\xb5\xa2\xc5\x5e\xb0\x5b\xdd\x6a\x45\x5a\
\xd1\xb8\x91\x9e\xf2\x56\x91\x0b\xf5\x5e\x81\x72\x44\x69\xc7\x96\
\x1c\x4b\xd5\x98\x2a\xc7\x06\x4b\xc3\x48\x39\x04\x90\x9f\x1b\xa5\
\x1c\x6d\xe8\x9d\x4e\x0d\x94\x03\x00\x11\x9f\xb2\x1b\x5a\x4c\x0d\
\x95\x63\x6c\xe0\x7f\xa4\x98\x2a\xc7\x76\x4b\xc3\x58\x39\xda\x96\
\x1c\x18\x2b\xc7\x16\x1c\xc0\x58\x39\x76\x3c\x07\x30\x56\x4e\xc4\
\x8f\xbb\x35\x74\x57\x30\x55\x4e\xb4\x9d\x6b\x56\x4e\x35\xd0\x8d\
\x32\xbf\x0c\x3d\xcd\x31\x55\x8e\x8c\xec\x2c\xd4\x01\x10\xb3\x3d\
\x04\x95\x22\x08\xb8\xb9\xa8\x7a\xf1\x09\x0f\x63\x23\x66\xc6\xae\
\x85\x5c\x7b\x9c\x5e\x32\xfc\xa0\xb8\x65\x9e\x2b\xe1\x8e\x3f\xd4\
\x5e\x4c\xfc\x15\x40\x5e\xfb\xef\x93\x8b\x25\x05\x35\x5c\x0d\xc2\
\x71\x01\x08\xe4\x75\x7b\x7e\xfe\xc7\xaf\x5d\x19\xcd\x7e\x53\x40\
\x1c\xc9\xc1\x33\xbb\x31\x67\x62\x3c\x94\x2e\x67\xe6\x4c\x71\x33\
\x5c\x70\xa2\x57\x76\x52\x27\x01\xc1\xfc\xa9\x78\x57\x7f\x6f\x47\
\x88\xf1\x08\x21\xc9\xa1\x10\xe4\xc2\x23\x7f\x7d\xed\xdf\x2d\x9a\
\x2f\x71\x75\xcf\x4c\xf2\xe3\xfe\xa3\x8b\xfe\xf7\x10\x07\xa1\x27\
\x96\x27\xae\x30\x5b\x34\x80\x73\xff\x53\xf8\xf6\x27\x2e\x30\xe2\
\xc6\xe6\xac\x50\xd0\xf9\x56\x7b\xe6\x29\x52\x7a\x9a\x8a\x9a\x9a\
\x57\x8e\x2e\xfe\x5e\x97\x7c\x45\xc3\x15\x2e\xb5\x40\x8e\x6e\xdf\
\x7a\x4d\x58\x51\x09\xa1\x24\xf2\x9a\x2b\xf4\xc6\x3f\xcc\xaf\xd7\
\x32\xbc\xdb\xa2\x98\xb3\xeb\x55\x41\x1c\xb9\xb9\x77\x7f\xb1\x03\
\x21\xd5\x48\xa1\xc8\xb9\x93\xc0\xca\xa5\x8b\x3f\xa8\x95\xb1\x4f\
\xaf\x8f\x08\xc6\xa1\x47\x96\x3c\x1e\x17\x2a\x8c\xa1\xef\x10\xe4\
\x50\x08\x05\x91\xbe\x0e\x14\xae\x02\x21\x20\x4c\x3d\xab\xab\x39\
\x02\x70\xc6\x3e\xf4\xb1\xf9\xe1\xa4\x16\x42\x0b\x5f\x90\x8e\x60\
\xec\x1c\x34\x74\x0c\x2e\xfc\x2a\xa9\x55\xf5\x40\xc3\xcb\x78\xe1\
\x24\x15\x4e\x7b\xd5\x01\xdb\x46\xe0\x0a\xa5\x20\x8b\x65\xa7\x45\
\x91\x70\x16\x1f\x5a\x90\xa3\x1b\x46\x7b\x2d\x1c\x39\x1a\x38\xb9\
\x45\xee\x74\xe6\x0a\xcf\xd0\x98\xf0\x48\xa0\xc2\x9c\xc4\xa9\xfe\
\xee\x4e\xb3\x6e\x85\x4c\x07\x78\xf3\xd3\xe9\xb7\x49\x55\x6c\x4c\
\x97\x6b\x0a\x47\xd9\x20\x8e\x16\x25\xc9\xd4\x99\xee\x7b\xe1\x74\
\x99\xb6\x87\xf6\xc4\x80\x5f\xac\x4c\x1f\x23\xa9\x32\xf4\x66\x55\
\xd3\x8c\x72\xb4\x22\x87\x47\x7a\x1e\x34\xf4\xe6\xfb\x74\x80\x97\
\xae\xcf\x1e\x26\x29\x75\x8b\xc9\xd1\x8a\xcc\xbe\xbf\xe7\x3e\x43\
\xd5\x8c\xeb\x79\xf9\xd3\xd9\x7e\x52\x4a\x49\x39\xbe\xe2\x4d\x2e\
\x47\x93\x8a\xcc\x9c\x7f\x65\x0d\x60\x5c\x85\x36\x5d\xcf\x2b\xcb\
\xc6\xde\x21\xb3\xb2\x40\x2f\xb0\x01\xcd\x2b\x47\x2a\x72\xe4\xec\
\xde\x75\x06\x97\x9a\x71\x3a\x1d\xe0\xa5\x4f\xe5\x8e\x92\x05\x99\
\x6b\x01\x39\x5a\x91\x17\xcf\xef\xfc\x63\x73\xaf\xf2\x99\xa1\xa7\
\xfb\xe6\xec\x41\x72\xb2\xe8\x34\xab\x1c\xad\xc8\xd4\xd9\x57\xef\
\x37\xbc\x42\x0b\xe2\x37\xac\xb3\x6f\x91\xaa\xa0\x9a\x58\x8e\xf4\
\xc8\xf4\x7b\xbd\xab\x1b\x48\x0d\xe0\x37\xac\x77\xde\x94\x3a\x44\
\xca\x42\x61\xa2\x69\xc0\xa6\x92\xe3\x49\x32\x91\xec\x5d\x0b\xd0\
\xd0\x61\xee\xb2\xd0\x05\xb6\x2f\x1f\x7d\x93\xcc\x17\x26\x65\x34\
\x8f\x1c\x2d\xb5\x4e\xbc\xb7\xef\x4f\xfd\x1d\xb1\xe1\xa0\x0b\xf4\
\xae\x48\x0e\x90\x63\x1e\x9b\x42\x48\x40\x8d\x22\x13\xc9\xbd\x5f\
\x06\xe8\x36\x66\x47\xa2\xa0\x0b\x6c\x5b\x36\x7a\x90\x2c\x48\x49\
\x55\xef\x1c\x0d\x0d\x4f\x91\xa9\xf3\xdb\xd7\x03\x8c\x99\x7a\xc9\
\x62\x05\xd0\x01\x5e\xbd\x31\x77\x84\xa4\x4c\x07\x8e\x3d\x8d\x8c\
\x52\x64\xe6\xfc\xee\x35\x00\xdd\x06\x56\x03\xf8\xed\x98\xae\x5b\
\x47\x7f\x43\x2a\xd5\x14\x72\x14\x99\x1c\xd9\xf5\x70\x03\x9c\x72\
\x56\x02\x1d\xe0\xf9\x9b\x72\xbf\x21\x0b\x52\x8f\x6f\x5f\xa3\xa2\
\xc8\xf4\xf0\xd6\xfb\x9b\x44\xcd\xb8\x9e\x17\x3e\x97\x3b\x4a\x7a\
\x52\x33\xcf\x31\xce\x36\xa0\x60\x30\x8a\x4c\x0c\xf7\x3c\xda\x44\
\x6a\xc6\xf5\x6c\xbd\x21\xd7\x4f\x2a\xcf\x63\x83\x8e\xf5\x48\x72\
\xf8\xc2\xd6\xfb\x1b\xa4\xa3\xa6\x5a\x3d\xdb\x6f\x4c\x0d\x90\xda\
\xf3\x87\xe2\xc8\x86\xea\xb1\x96\x64\xfa\x62\xcf\x9a\x26\x2b\x35\
\x41\x3d\x3b\x6f\xce\xee\x27\xbd\x82\x26\x99\xa7\x34\x5b\x47\x00\
\x25\xc9\x91\x53\x7b\xd7\x35\xe8\x29\x67\x45\x7a\x5c\x60\xeb\xd2\
\xf4\xaf\x49\x16\x3c\x8e\x52\x52\x15\x87\xb4\xcd\xc6\x93\x64\xe2\
\x42\xcf\xbd\x0d\xd8\x51\x53\x0d\x3d\x31\xe0\xf5\xe5\x99\xfd\xa4\
\xe7\x91\x6c\x08\x39\x5a\x92\x89\x73\x6f\xae\x03\x18\x6b\xcc\xde\
\x80\x8a\xa1\x0b\xec\xb9\x29\x7b\x80\xd4\x9e\xa2\x32\xbe\x59\xad\
\x25\x79\xe9\xfd\x9e\x35\x40\x4f\x23\xf7\x06\x54\x88\xa0\x0b\xec\
\x58\x91\x3a\x4a\xe6\xa4\xd9\x6a\x34\x0b\x8a\xbc\x94\xda\xfb\x50\
\x83\x77\xd4\x54\x03\x1d\xe0\xc5\x1b\xb3\x47\x48\xaa\x7c\xbd\x0d\
\xcc\x86\x22\x53\x17\xf6\xac\x6d\x82\x8e\x9a\x6a\xe8\x72\x81\x17\
\x6f\x1b\x3d\xee\xf7\xef\x1a\x8a\x22\x93\x89\xed\x8f\x34\x69\xe3\
\x79\x36\xe8\x00\x5b\xae\x4f\xf6\xb3\x18\x48\x65\x16\x9a\x94\x64\
\xf6\x62\xcf\xfa\x16\x54\x03\xf8\xb1\x06\xaf\xde\x98\x39\x4e\xe6\
\x55\x9e\x85\x7a\xfb\x98\x42\x5e\x91\xa9\xc4\xee\x46\x8a\x0d\x08\
\x1b\x3a\xc0\xcf\x6f\xc9\x0c\x90\x05\x39\x56\x6f\x1f\x01\xb4\x22\
\x87\xce\x77\x6f\x6c\x61\x35\x80\x5f\x7a\x36\x2f\x4d\x1e\x1f\x3f\
\xef\x31\xa1\x7a\xd3\x92\x4c\x26\x7f\xb5\xb6\xc5\xd5\x00\x7e\x06\
\x74\xdf\x9a\x79\x9b\xcc\x15\xea\x7f\x42\x2a\x29\x25\x39\x78\xee\
\x8d\x0d\x40\x5f\xbc\xde\x79\x63\x00\x74\x81\x5d\xcb\xb2\xfb\x49\
\x55\xc8\xb1\xbe\x4d\x6b\x4f\x52\x5f\x3a\xbb\x65\x6d\x13\xf7\xa1\
\x55\x4b\x4f\x0c\xd8\xb1\x22\xd9\x4f\x16\xbc\xba\x8e\x96\x4a\xf2\
\xe2\xd0\xeb\xad\xd0\x51\x53\x05\xa2\x27\x06\x74\xdf\x9c\x39\x40\
\x16\xbc\x7a\x55\x6d\x5a\x92\x89\x77\xb7\xae\x6e\xb1\x53\xce\x4a\
\xa0\x0b\x6c\x5e\x99\x3e\xe6\x67\x52\xf4\xa3\x3d\x5a\x91\x89\x41\
\x3f\x1c\xdd\xaa\x99\x01\x1d\x60\xf3\x92\xb1\xc3\xe4\xa8\xca\x97\
\xbd\xfc\xaa\x46\x48\x32\x79\xa1\xdb\x1f\xaf\xb1\x6a\x4a\x41\x07\
\x78\x61\x49\x6e\x80\x4c\x2b\x55\xe6\x4e\x1e\x35\x41\x91\xc3\x83\
\xdb\x4d\xbf\xbe\xa6\xde\x74\xb9\xc0\xcf\x6f\xc9\x1d\x23\xc7\xa4\
\x22\xa9\x27\x46\x4b\x6b\x55\x66\x8a\x97\x3e\x0d\xed\x6e\x96\x60\
\xa7\x5a\xd2\xe9\x00\x2f\x2c\xc9\x9e\xf0\x23\x75\x72\xcc\x91\x35\
\x1d\x90\xcb\x2b\x72\x24\xb1\xd5\x96\x9a\xca\xa0\x03\x74\xdf\x9a\
\xe9\x27\x3d\x99\x67\x6d\x47\x4b\xb5\x22\x87\x2e\x6c\xfd\x9a\x2d\
\x35\x15\xd3\xe9\x00\xdb\x96\x8c\xbe\xed\x47\xea\xf8\x55\x5b\x4d\
\xd4\x48\x32\x75\x66\xb7\x2d\x35\xd5\xd1\x19\x03\xb6\x2d\x4b\x0e\
\x90\xa3\x9e\x57\x23\x35\x05\x45\x26\x92\xbb\xd6\x4e\x76\xd4\x70\
\x11\xbf\xc2\xff\xe0\x7e\x9e\x66\x9a\x39\x9e\xe1\x21\x3e\xc3\xaf\
\xf3\xf7\x4b\xaf\x23\x37\x17\x13\x92\xa5\xe6\xe0\xa6\xc0\xa2\xb6\
\xd7\x3b\x3f\x43\x86\x2e\xb0\xf3\xb6\xf4\x61\x4d\xe9\x15\x6a\x10\
\x02\x2f\xa5\x56\xc3\xe7\x7a\x3b\xc6\x23\x6a\x38\x8f\xdf\x61\xaa\
\xb4\x45\xfe\x90\xd7\xcc\x22\x87\xfc\x87\x16\x93\x53\xec\xd4\xb9\
\x3d\x79\xd2\x6f\x1a\x30\xd4\x36\x9b\x56\x64\x62\xec\x8d\x0d\xe3\
\xe7\x35\xfc\x3d\x0e\xcc\xfa\x83\xf3\x5c\x3a\x8b\x9c\xf7\x66\x1e\
\xb1\x9a\x5c\x8e\x1f\x0a\xd2\x7d\x6b\xe6\x08\x27\x46\x4b\x43\x92\
\x23\xc9\xe4\xc5\x3d\x1d\xe3\x11\x35\x5c\xcc\xa3\x97\xfd\xcd\x10\
\xaf\x2f\x2b\x87\x5c\xd3\x6a\x72\x8a\x7a\xb6\xdc\x92\x3a\x46\x2a\
\xa9\xc2\x6a\x18\x28\x32\x35\xb8\xe7\x81\xc9\x8e\x1a\xfe\xa8\xa2\
\xdf\xbd\x36\x8b\x9c\x97\x5b\x4f\x0e\xfc\x63\xcf\x8e\x3b\x32\xbf\
\x25\xb5\x1a\x0d\xc1\x8c\x56\xe4\x48\xf2\x95\x8d\x01\x35\xcb\xa6\
\x04\xcf\x9d\xe7\xdf\x70\x29\x17\x71\x01\x3f\xc1\x87\xf9\xeb\x29\
\x3f\x7e\xa8\xac\x1c\xc5\x8f\xb7\xa0\x1c\xbf\x99\xfb\xea\x67\x72\
\x27\x43\x89\xd4\x51\xe4\xa5\x4b\x5b\x1e\x08\x36\x9e\xf9\x83\xc0\
\xf7\xc7\xa7\x1e\xfa\x19\xe3\x4b\x81\x6f\x77\x96\x95\x43\x7e\xb7\
\x25\xe5\xf8\x19\xf9\xf2\x9d\xd9\x93\xfe\xad\x4c\x48\x7d\x45\xa7\
\xa5\x92\x5a\x93\xa9\xc4\xee\xc7\x82\x43\x69\x74\x79\x3e\x30\xd3\
\x3d\xd3\x97\xcd\x8f\x30\x3b\x59\xec\x82\xe5\x63\x9a\x9c\xb3\x53\
\xe3\xa8\x5b\x46\x4e\x31\x52\xe7\x33\xb9\xe3\xa4\x96\x05\x8e\x5e\
\x51\xd3\x3a\xab\xc8\xcc\xa5\x9d\x1d\x53\x4f\x39\xb9\x6c\x4a\x06\
\x97\xe8\x91\xe6\xf3\x81\x39\x36\x06\x3e\xdf\x3c\x6d\x01\xeb\xa7\
\xfc\xaa\x75\xe4\xf8\x7a\x5e\xf9\x6c\xea\x14\x39\x26\xaf\x28\x8c\
\x4a\x91\xe9\xec\x8e\xaf\x4e\xef\x0d\xe0\x86\xc0\x3c\xcf\x95\x5a\
\x32\xbf\x15\x98\xe3\x5f\x03\x9f\x4f\x97\xb3\x65\xca\xaf\x5a\x49\
\x4e\xf1\xca\xec\xcf\x67\x0e\x93\x9e\x37\xa9\xa7\xb2\xb3\x1f\x2d\
\xa9\x13\x17\xf6\x6d\x9a\xd9\x51\xc3\xef\x05\x66\xfb\x5e\xc9\xe5\
\xae\x0e\xcc\xb1\x2d\xf0\xf9\x74\x39\x8a\xd7\x05\xbe\x0d\x41\x4e\
\x03\x5d\x40\x27\x74\x4f\xec\xbe\xbd\x6f\x3d\x96\x3c\x11\x8b\xb1\
\xf8\x1c\x8a\xf1\xbb\x9c\xb2\xec\x0b\x20\x94\x12\x6e\xa2\x30\xf0\
\xed\xdb\x7e\xcc\xd8\x8c\x67\x0d\x7c\x28\x30\x9d\x28\xb9\xe0\xe0\
\xa7\xbf\x3b\x6b\x5e\xfe\x79\xb8\x5b\xdc\x40\x72\x80\x55\x92\xb1\
\xbb\x0e\xf4\x3e\x92\x39\xd4\x16\xf3\xa4\x44\x1e\x95\xdc\xe9\x54\
\x29\xd7\x4d\x0c\x0e\x6c\xba\xfd\xd9\xbe\x78\x89\x7b\x92\x2f\x0c\
\x4c\x8f\x95\x4c\x20\x17\x98\xfe\xc0\xac\x8b\xfa\x3a\x43\x0d\xa7\
\x6a\x28\x39\x80\x90\x74\x57\xf7\xf6\x6d\x1a\xe9\x8f\xc7\x84\x44\
\xa0\x7c\x94\x83\x2a\x26\x46\x06\x8f\x3e\xf9\xf9\xff\xa2\xbb\x52\
\x96\x98\x75\x41\x55\x2b\xb0\x70\xd6\x6f\x3f\x82\x75\x61\x6e\x6d\
\x83\xc9\x01\x84\x66\x6c\x55\xdf\xbe\x6f\xa6\x7e\xeb\xc6\xda\x95\
\x53\x7c\x62\x48\x39\x3d\xd4\xc2\x4d\x7a\xc7\xfe\xf6\xf6\xff\xed\
\x8b\x43\x97\xbc\xd7\x73\x75\xf1\x69\xe5\x4a\xc6\x48\xf1\xfd\x1b\
\x61\x6e\x6b\xc3\xc9\x01\x85\xa2\xbb\x7a\xcf\xbe\x07\x93\x47\xe1\
\x2a\xe5\x6f\x42\xa9\xa3\x8d\x86\xa7\x1d\x27\x35\xfc\xce\xc3\xb7\
\xff\x8c\xee\x4a\x59\xd3\xc7\xa6\x3c\x53\x7c\xbf\x9b\x9f\x0a\x2f\
\xd1\xc6\x93\x53\xd4\xf3\xa5\xbe\x5d\xdf\x4c\x9d\x8a\xbb\x42\x17\
\x50\xfa\xc6\x4d\x42\xb7\x39\x99\xd1\x81\xef\x7c\xa1\x8b\x8e\xd0\
\x35\x7e\xa2\xcd\x31\xf4\xfa\x0b\xc5\xe3\xe1\x25\xda\x88\x72\x00\
\x08\xd5\xe5\xae\x7b\xfd\xb5\x2f\x8f\x9d\x80\xd3\xa6\x4a\x3e\x08\
\x49\x3b\x4e\xe6\xd2\x9b\x8f\x7d\xee\x47\x74\x85\x8e\xe0\x89\x2f\
\x4f\x15\xdf\x1f\x65\x5b\x58\x49\x36\xa8\x1c\xa0\x43\xd1\x59\x77\
\xf0\xb5\xaf\x8d\x9e\x86\x5b\xd0\xfe\xd3\xc6\x26\x15\x69\x3a\x4e\
\x32\xb5\xef\x89\x3f\xe9\xea\x72\x23\x7a\x6a\xcc\x73\xc8\x02\x00\
\x3e\x8c\x07\xc2\x4a\xb2\x61\xe5\x00\x42\x77\x3a\xab\xf7\xef\x78\
\x34\x71\xb2\xdd\xa1\x22\x26\x1f\xc1\xe7\xe8\x98\x48\x0f\x1f\xfc\
\xab\x2f\x3e\x47\x37\xcc\x67\xa8\xcd\xba\x36\x69\x3c\x5f\x9c\x0c\
\xad\x51\xd0\xc0\x72\x80\x4e\xdd\xe9\xac\xdd\xd5\xdb\x91\x3c\x15\
\x73\x51\xd0\x14\x04\x41\x4a\x38\xa9\x54\xef\xa6\x55\x3f\x8d\xac\
\xd4\xf8\x8c\x57\x6c\x77\x4e\x1f\x96\xbb\x52\x1a\x5a\x0e\xd0\xa9\
\xbb\xdc\xfb\x0e\xbe\xb5\x31\x73\xc4\x6d\x6b\x57\x4a\x41\x09\xe5\
\xc6\x12\x43\x07\xfe\xe2\x9e\x17\x7b\x62\x51\x95\x1a\x1f\xf1\x3a\
\x4e\x14\x27\x43\x2a\x3b\x0d\x2e\x07\xe8\x50\x5d\xee\x97\xf6\x1e\
\xdd\x90\x7b\x36\x11\x73\x63\x4e\x2c\x1f\xcb\xf4\xbc\xb3\xf1\xae\
\x67\xe8\xae\x8a\xea\x51\xa3\x93\x3c\x5d\x7c\x7f\x84\x73\xc2\x48\
\xae\x09\x2e\x11\xea\x50\x74\x45\xff\xbf\x3d\x7e\xdf\xcf\xc4\xc2\
\x36\x24\xb3\x03\x87\xee\x3e\xcb\x68\x2b\xb4\x71\x9e\xc6\x77\xe1\
\x02\x58\x8c\xaf\x84\x91\x5c\x13\xc8\xf1\x1b\xd6\x1d\x19\x74\x8f\
\xff\x5f\x27\x35\x10\xef\xf3\x57\x58\x0d\x00\xf8\x06\x7e\x7a\xf5\
\xe9\x35\x7c\xb5\xe6\xd3\xa1\x28\x7a\x62\x74\xe9\xf6\xc4\xe8\xd4\
\xf1\x91\x8b\xe3\x8d\x82\x2f\xe0\xa6\xab\x4f\xac\x29\x4a\x0e\x00\
\x88\x60\x5b\xba\x7e\xfc\x12\x43\xc5\x61\x85\x87\xaf\x3e\xb1\x26\
\x29\x39\xa6\x20\x0a\xf8\xef\xe2\xe4\xe2\xab\x4f\xcd\xca\x09\x9b\
\x9f\x84\x97\x94\x95\x53\xa8\x6a\xee\xfc\xe5\x66\x10\x47\x70\x20\
\xac\x55\xb3\x72\xd2\x81\xe9\xd2\x57\x83\x8a\x32\x73\x97\xe3\xa9\
\x0a\xe6\xa9\x08\x2b\x27\x98\xdd\x73\x4b\xce\x11\x7c\x98\x71\xaa\
\x82\x14\x9f\x29\x33\xdc\x5d\x35\x56\xce\xb9\xc0\x74\xe9\xf0\x8d\
\x60\x08\xc8\xfb\x97\x4f\x50\x24\xf0\x8b\x70\x56\xcd\xca\xe9\x0f\
\x4c\xdf\x50\x72\x8e\x60\x37\xe6\xe1\x8a\xd2\x0c\xa9\x62\xb3\x72\
\x8e\x04\xa6\xff\xa8\xe4\xad\x89\xef\x0e\x4c\x57\x26\x67\x07\x4e\
\x87\xb1\x6a\x2d\x2f\x47\xfc\xdf\x44\x5f\x32\xb0\x08\x5f\x9d\xfe\
\x3d\x3f\x89\xbb\x26\xfe\xf1\xb0\xad\xa2\x34\x19\x46\xe7\x8d\x95\
\x03\x00\xc1\x20\xdc\x7f\xe1\x1f\x04\xbf\xe2\x1c\x3c\x15\xe8\x45\
\xd9\x26\x86\x2b\x4c\xf3\x3f\xc3\x18\x18\xb7\x72\x80\x1f\x07\x5a\
\x57\x1f\xc5\x41\xfe\x3d\x97\x73\x11\xe7\xf3\x93\xdc\x84\xc3\xb8\
\x23\x30\xe7\x0f\x2a\x4d\x52\xbc\x8b\x9d\x95\xce\x6b\x99\x15\xfe\
\x73\x45\xa1\xf0\xbf\x9c\xf6\xab\x60\xac\xf4\x5f\xce\x48\xf3\xcf\
\x5a\x2a\x56\xba\x86\x7c\x1f\x6f\x5c\x76\x9e\x77\xf1\x44\x55\x69\
\xbe\x50\x26\xf2\xba\x0a\xac\x1c\x00\x62\x14\xf7\x5e\x46\xcf\xbb\
\x58\x25\xce\x54\x95\xe6\x18\x9e\xbd\xda\xf5\xb2\x72\x00\x00\x22\
\x8d\x3b\xf0\x24\x4a\x1f\xee\xf3\xf8\x3e\x96\x8a\x53\x55\x27\x7a\
\xd5\x67\x3b\x4d\x33\x9e\x73\xb5\x08\x85\x7f\xe7\xd3\xb8\x0b\xab\
\xf1\x59\x5c\x83\x0f\xc3\xc5\x10\x86\xd0\x8f\x2d\xe8\xae\xb8\x8d\
\x36\x35\xc5\x3e\x1e\xc6\xf2\x7a\x6f\x97\xc5\x62\xb1\x58\x2c\x16\
\x8b\xa5\x56\xfc\x3f\x0e\xee\x58\xa5\xa2\xf3\xe7\x6c\x00\x00\x00\
\x25\x74\x45\x58\x74\x64\x61\x74\x65\x3a\x63\x72\x65\x61\x74\x65\
\x00\x32\x30\x32\x32\x2d\x30\x33\x2d\x32\x34\x54\x31\x31\x3a\x35\
\x39\x3a\x32\x33\x2b\x30\x30\x3a\x30\x30\x3f\x81\x57\x00\x00\x00\
\x00\x25\x74\x45\x58\x74\x64\x61\x74\x65\x3a\x6d\x6f\x64\x69\x66\
\x79\x00\x32\x30\x32\x32\x2d\x30\x33\x2d\x32\x34\x54\x31\x31\x3a\
\x35\x39\x3a\x32\x33\x2b\x30\x30\x3a\x30\x30\x4e\xdc\xef\xbc\x00\
\x00\x00\x00\x49\x45\x4e\x44\xae\x42\x60\x82\
\x00\x00\x32\x57\
\x89\
\x50\x4e\x47\x0d\x0a\x1a\x0a\x00\x00\x00\x0d\x49\x48\x44\x52\x00\
\x00\x00\xce\x00\x00\x00\xce\x08\x06\x00\x00\x00\x76\x1f\x3d\xc4\
\x00\x00\x00\x01\x73\x52\x47\x42\x01\xd9\xc9\x2c\x7f\x00\x00\x20\
\x00\x49\x44\x41\x54\x78\x9c\xed\x7d\x79\x98\x64\x45\xb1\xfd\x89\
\xaa\xee\xd9\x98\x85\x4d\xf6\x45\x10\xf4\x89\x88\xca\x36\xac\x22\
\xbb\x3c\x64\x11\x9e\x22\xc8\xa2\x80\x20\x3e\x36\x05\x14\x50\xf0\
\xf7\x63\x11\x54\x44\x64\x44\x65\x51\x54\x40\x41\x7d\xb2\x0b\x08\
\xc8\xb0\xc9\x2a\x3c\x46\x14\x59\x87\x9d\x81\x19\x66\x80\x19\x61\
\xa6\xbb\xaa\xe2\xfd\xc1\x89\x99\x98\xec\xbc\xd5\x55\xd5\x55\xb7\
\xaa\xbb\xf2\x7c\x5f\x7d\xb7\xbb\xea\x2e\x99\x79\x33\x32\x23\x23\
\x4f\x44\x00\x09\x09\x09\x09\x09\x09\x09\x09\x09\x09\x09\x09\x09\
\x09\x09\x09\x09\x09\x09\x09\x09\x09\x09\x09\x09\x09\x09\x09\x09\
\x09\x09\x09\x09\x09\x09\x09\x09\x09\x09\x09\x09\x09\x09\x09\x09\
\x09\x09\x09\x09\x09\x09\x09\x09\x09\x2d\x84\xb4\xbb\x00\xdd\x0c\
\x55\x2d\xf0\x1d\xa4\xf7\x10\x87\x02\x50\x11\xa9\xb4\xbb\x20\x21\
\xd2\x0b\xcb\x19\xaa\x2a\x00\x8a\x00\xca\x22\xa2\xed\x2e\xcf\x70\
\x40\x27\xb6\x59\x12\x9c\x1c\xa1\xaa\x45\x11\x29\xbb\xff\xdf\x0f\
\x60\x7d\x00\xeb\x02\x58\x19\xc0\x04\x00\x3d\xed\x2d\x65\xdb\x51\
\x02\xf0\x16\x80\x17\x00\x3c\x0a\xe0\x21\x11\x79\xda\x7e\x0c\xdb\
\xb0\x5d\x48\x82\x93\x03\x38\x62\x42\x44\x54\x55\xc7\x03\xd8\x1b\
\xc0\x3e\x00\x36\x06\x30\xae\xdd\xe5\xeb\x70\xcc\x03\x70\x3f\x80\
\x4b\x00\x5c\x2e\x22\xf3\xa9\xe2\x6a\x3b\x67\x9f\x24\x38\x2d\x86\
\xaa\x16\x4c\x47\x57\xd5\x83\x00\x9c\x00\xe0\x7d\xee\x14\x1b\x3d\
\x3b\x42\x05\xe9\x10\xf8\x7e\x59\x74\x7f\x3f\x0e\xe0\x34\x11\xb9\
\x14\x41\xdb\xe6\x8d\x24\x38\x2d\x84\xa9\x15\xaa\xba\x22\x80\x9f\
\x01\xd8\x95\x3f\x95\x9d\x51\x20\xbd\x83\xea\x50\x00\x26\x1c\x26\
\x44\x57\x00\xf8\x6f\x11\x79\xbd\x5d\xaa\x5b\x7a\x69\x2d\x82\x13\
\x9a\x75\x00\x5c\x09\xe0\xfd\x4e\x60\x0a\xe1\xe9\xee\x93\x90\x3d\
\xa8\x54\xd8\x46\x45\x00\x8f\x00\xf8\xb4\x88\x4c\x6f\xc7\xcc\x93\
\x04\xa7\x05\xb0\x17\xa9\xaa\xef\x03\x70\x1b\x80\x55\xb9\xe8\x0d\
\x17\xfe\x59\x82\x94\xf0\x2e\x6c\x26\x29\x06\xdf\x5b\x5b\x3e\x05\
\x60\x2b\x11\x79\x39\x6f\xe1\x49\x82\xd3\x64\xd0\x10\x20\x00\xc6\
\x03\xb8\x0b\xc0\x87\x23\x42\x63\xb3\x8b\x09\xcc\x9b\x00\x9e\xa1\
\x35\xa9\xdb\x67\x9d\x02\x80\x49\x5c\x07\x8e\xe7\x77\x95\xc8\x0c\
\x64\x6d\x7a\x0f\x80\xad\xf9\x7f\xa5\x53\xcc\xd5\x09\x75\x42\x55\
\x8b\x3c\x5e\xa0\xef\xa2\x5f\x17\x47\xd9\xfd\x7d\xab\xaa\xee\xad\
\xaa\xab\x98\xe5\x2d\xe1\xdd\x19\x5b\x55\x57\x53\xd5\x03\x54\xf5\
\xce\x8c\xb6\x53\x55\xed\xe3\xf1\x7b\x70\x6d\x9f\x07\xd2\xcb\x6a\
\x22\x9c\x8a\xf6\x71\x00\x53\x39\x52\xfa\x97\x59\xe1\x88\xfa\x06\
\x80\x23\x45\xe4\x92\xf0\xfa\xf4\x4e\x06\x32\x05\x54\xf5\x10\x00\
\x67\x03\x58\x82\x33\xb2\xb5\x91\x19\x0e\x2a\x00\x26\x8b\xc8\xc3\
\x9d\xb2\xcf\x93\x50\x07\x38\x52\x8a\xaa\xde\xc2\x91\xb0\x14\x19\
\x2d\x5f\x56\xd5\x8f\xba\xf3\x8b\xbc\xa6\xdb\x05\x66\x21\xd8\x1e\
\xd6\x36\x05\x7e\xb7\xa9\xaa\xbe\xce\x36\xac\xb8\x76\xb5\x36\xfe\
\x03\x16\x0d\x3e\x09\xc3\x05\x4e\x45\xdb\x80\x2f\xd6\xbf\xdc\x0a\
\x05\xe7\x1d\x55\x9d\xcc\xf3\x7a\xdb\x5d\xe6\xe1\x02\x6b\x2b\x55\
\xdd\x8e\x82\x52\x0e\xda\xb6\xa2\xaa\x0b\xc8\xc4\x48\xc2\x33\x9c\
\xa0\xaa\x3d\x3c\x7e\x37\xb2\xb6\xb1\x51\xf1\x24\x24\xa1\x69\x08\
\x4e\x78\xce\x8e\xcc\xe6\xd6\xd6\x27\xc0\xbd\x8b\x84\x61\x02\xaa\
\x18\x0f\x06\xaa\x99\x1d\x5f\x52\xd5\x89\xa6\xce\xb5\xbb\xac\xc3\
\x0d\x6c\xb7\x82\xaa\x2e\xaf\xaa\x73\x02\x95\xcd\x84\xe8\x56\x38\
\x8a\x53\x2b\x91\xa6\xb4\x26\xc0\xbd\xa8\x15\x01\xac\xcd\xbf\xed\
\x3b\x5b\xe8\x5e\x29\x22\x6f\xbd\x4b\x59\x4b\x26\xd3\x7a\x41\x83\
\x81\x88\xc8\xab\x00\xfe\xc4\xaf\xcd\x08\x60\x6d\xbd\x8e\xaa\x4e\
\x22\x27\xb0\xa5\xc2\x93\x04\xa7\x39\xb0\x76\x5c\x8d\x0c\x67\x6f\
\xf9\xb1\xdf\xa6\xba\x3d\x9e\x84\xc6\x60\x46\x94\xa9\xf6\x7f\x70\
\x5c\x06\xc0\x2a\xc1\x77\x2d\x41\x12\x9c\xe6\x62\x49\xbe\x30\x3f\
\xa3\x58\x1b\x3f\xc3\x99\xa6\xe3\x9c\xb2\x86\x11\x8c\x11\xfd\x24\
\xff\xf7\x82\xa3\x00\x7a\x01\x4c\x0c\x7e\x6b\x09\x92\xe0\x34\x07\
\xf6\x92\x46\xf3\x18\x13\x8e\x79\x39\x96\x67\xa4\xc2\x06\xa4\xb9\
\x91\xdf\xac\xcd\x47\xe5\x51\x90\x64\x7d\xc8\x0f\x05\x5a\x7b\x0a\
\xaa\x9a\x66\x9d\xc6\x60\x6d\x57\x6d\xc0\xcf\x45\x15\x4e\x82\x93\
\x1f\x66\x8b\x48\xa9\xdd\x85\x18\x09\x50\xd5\x39\xed\x2e\x43\x12\
\x9c\xfc\xf0\x05\x55\x7d\x35\xb2\x06\x4a\xa8\x1d\xd6\x76\xab\xbb\
\xff\xdb\x82\x24\x38\xf9\xe1\xbb\xed\x2e\xc0\x08\x44\x12\x9c\x2e\
\x40\x52\xd3\x9a\x07\x89\xf8\xe8\xe4\x8a\x24\x38\xcd\x45\x35\x35\
\x2c\xb5\x75\xeb\xa1\xc9\x38\x30\xbc\x60\xc2\x32\xdb\x09\x4f\x27\
\xac\x63\xaa\x75\xa2\x7a\xcb\xd7\xcc\x7b\xb5\x02\x26\x34\xb3\xf3\
\x78\x58\xda\xc5\x6e\x12\xb8\xa3\x3d\x1a\xc0\xed\x0c\xfb\x94\x90\
\x3f\x6e\x06\xb0\x53\x1e\xd1\x3f\x93\xe0\x34\x09\xce\x89\x6d\x55\
\x00\xe7\x00\xd8\x16\xc0\x98\x36\xb7\x71\x6f\xc6\xf3\xcb\x8e\xe7\
\x55\x2b\x7a\x32\xf6\x4f\x14\x40\x7f\x83\xe5\x6b\x06\x14\xc0\xdb\
\x00\x6e\x00\x70\xb4\x88\xcc\xcc\x23\xfe\x40\x12\x9c\x26\x42\x55\
\x17\x12\x38\x55\xf5\x3d\xec\xb8\xb9\xe9\xdd\x01\x04\xc0\xbd\xe4\
\x6e\xd9\xa6\x61\x3f\xcb\x74\x1e\x80\xef\x50\x18\x06\x33\x5a\x14\
\x29\x64\x67\x02\xd8\xcf\xf9\xfa\xdb\x3d\xff\xc5\x41\xa2\x1d\xb0\
\xb6\xed\x13\x91\x59\x08\xde\x41\x2b\x91\xd6\x38\x4d\x84\x67\xe5\
\x8a\xc8\xcc\x76\x97\x47\x55\xb3\x84\xe2\x4d\x11\x79\xb9\xce\x7b\
\xc5\x68\x2e\x00\xd0\x5f\xef\xbd\x5a\x81\xbc\xa3\x7b\x26\xc1\x69\
\x32\xdc\x8c\xd3\x2e\x26\xb4\xb8\x91\x38\xeb\xf9\x3d\xec\x68\xf5\
\xcc\x38\x59\x7d\x45\x5c\xac\x84\x76\x19\x09\x72\xcf\x68\x90\x04\
\xa7\x45\xa0\x00\xe5\xde\x91\x4c\x55\x19\xc4\x7d\x58\xb9\x1e\x1b\
\xb4\xc3\xb9\xb5\x5b\x66\x5d\xf8\x7b\x57\xf9\x19\x25\x76\x74\x42\
\x42\x03\x48\x82\x93\x90\xd0\x00\x92\xe0\x24\x24\x34\x80\x24\x38\
\x09\x09\x0d\x20\x09\x4e\x42\x42\x03\x48\x82\x93\x90\xd0\x00\x92\
\x39\x3a\x67\xb8\xb0\x45\xad\xda\xe3\x11\x9a\x8e\xab\xdd\x7f\xe1\
\xde\x4b\x0d\x51\x2f\x65\xb0\x98\xd6\xee\x5e\xcd\x30\x47\x2b\xdc\
\x7e\x58\xa7\x22\x09\x4e\x8e\x08\x02\x82\xb7\xbc\x63\x54\xe9\xc8\
\x25\xee\xdf\xf4\xd5\x70\x1b\x4b\xc3\x98\xb5\x51\xda\x92\xcd\xc7\
\x4e\xcc\x34\xed\x91\x04\x27\x07\xb0\x13\x14\x98\xa1\x4d\x00\xac\
\x10\xec\xf0\xb7\x02\x52\xe5\xfd\x4e\x52\xd5\x95\xea\x64\x0e\x4c\
\xc8\xf8\xbd\x97\xf7\x6a\x16\x2a\x00\xde\x11\x91\x37\xad\x6c\x9d\
\x98\x81\x20\x91\x3c\x5b\x0c\xff\xd2\x55\x75\x27\x00\xa7\x30\xd9\
\x54\x1e\x6d\x3f\x1c\xd9\xd1\x65\x00\x73\x00\x3c\x46\xc6\xf3\x6f\
\x2d\xe3\x5a\xbb\x33\x4d\x7b\x24\xc1\x69\x21\x54\xb5\x47\x44\x4a\
\xaa\x3a\x0e\xc0\xff\x07\x70\x6c\xbb\xcb\x34\x0c\x31\x8b\x99\xa6\
\x7f\x84\x1c\xd9\xcf\x83\x21\x09\x4e\x0b\xe0\x47\x47\x55\xdd\x0c\
\xc0\x8f\x01\x7c\xcc\x25\x42\xca\xcb\x9a\x39\x9c\x3d\x40\x2d\x51\
\xae\xa9\x9b\xbf\x06\x70\xa0\x79\xd7\xb6\x5b\x78\x92\xe0\x34\x19\
\x6e\x96\x11\x00\x27\x00\xf8\x36\xa3\x4b\x96\xdb\x1d\x60\x62\x98\
\x42\xb9\xd6\xe9\x05\x70\x81\x88\x1c\xda\x8e\x2c\xd3\x21\x92\xe0\
\x34\x09\x66\xd6\x25\x53\xf8\x43\x00\xce\x05\xb0\x0d\x7f\x0e\x67\
\x19\x6d\x60\x8d\xd1\x4d\x08\xa3\xd8\x78\xe1\xf9\xac\x88\xfc\xbe\
\xdd\x06\x83\x24\x38\x4d\x40\x60\x00\xf8\x0a\xbd\x25\x27\x50\x38\
\xc2\x3d\x90\x3c\x55\xb5\xe1\x8c\xd0\xe2\x68\x6d\xf9\x24\x80\x8f\
\x00\x58\x80\x36\xee\xf7\x24\xc1\x19\x02\x02\x33\xb3\xc5\x1a\xd8\
\x83\x3f\xc7\x54\x33\x73\x3b\xee\x07\x70\x16\x80\xc7\x53\x64\xcf\
\x01\x18\x03\xe0\x93\x00\x76\x8f\x08\x8f\x0d\x3a\x9f\x12\x91\xeb\
\xdb\x3d\xeb\x24\x34\x00\x9f\x1a\x5c\x55\x3f\xa7\xaa\xaf\xb8\xec\
\x60\x3e\xff\xa7\x65\x65\xb3\xcc\x6c\x8f\xa8\xea\xe6\xed\x2d\x7d\
\xe7\x43\x55\x8f\x0b\x32\xda\x59\xca\xc2\x8a\xaa\x9a\x85\x2d\x73\
\xcd\xc8\xc4\xbb\x3d\x83\x7c\x8a\x8d\x26\xa0\x4a\x33\x4e\x9d\x08\
\x66\x99\xa5\x38\x73\x1c\xc8\x9f\xab\xcd\x32\xe0\x8c\xf4\x2d\x11\
\xf9\x77\xca\x53\x99\x09\x21\x5b\xa0\xa2\xaa\x0f\x03\xf8\xa8\x9b\
\x69\xac\x7d\x6f\x16\x91\x1d\x62\x46\x02\x17\xf3\xa1\xe6\x59\xdc\
\x28\x43\xf5\xcc\x5e\xe9\xe5\xd5\x01\xa7\x1a\x94\x55\x75\x07\x00\
\x53\x00\xbc\xdf\xe9\xdf\xe1\x82\xd6\xcc\xa9\x4f\x03\x38\x4a\x44\
\xae\x77\xf7\x49\x21\x71\x33\xc0\xd9\x40\x01\x4c\x0b\x04\xc7\xb0\
\x54\xd6\xb5\x2e\xe6\xc3\x27\x00\x7c\xa0\xca\x63\xfa\x00\xbc\x02\
\x60\x9a\x05\x1b\xe1\x0c\x56\x69\xb7\xa9\x7b\x44\xc1\xa5\x63\x1f\
\xab\xaa\xdf\x8f\x64\x3c\xf6\xf0\x19\x91\x7f\xc5\x50\x51\x18\x8a\
\x6a\xd0\x49\x60\x92\xe0\x42\xec\xd3\x8c\x6b\x5c\x06\xef\x5f\x06\
\x6d\x6c\x6a\xdb\xdf\x10\xa4\x65\xe7\xfd\x45\x55\x47\xab\xea\x15\
\x91\x77\x92\x85\x37\x55\xf5\x4a\x0a\xda\xc2\x7b\xb5\xa4\xe1\xba\
\x09\x3e\x4b\xb4\xaa\x4e\x56\xd5\x07\xd8\xe0\x95\x40\xff\xb6\xef\
\x4c\x68\x66\xa8\xea\x3e\xee\x3e\x69\x0f\xa7\x46\x34\x28\x38\x76\
\xcd\x57\xdd\xe0\xd5\xc7\x6b\xb3\x3e\xe1\x5a\x74\x8a\xaa\x8e\x46\
\x0d\xc2\x93\x54\xb5\x2a\x70\x9b\x99\x05\x55\xf5\x9b\x99\xb6\x6e\
\x09\xcd\xa5\x45\x7e\xae\xa5\x6a\x36\xdd\x4d\xff\xc3\xde\xfa\xe3\
\x22\xe8\x2c\xe3\x72\xd4\x2c\x76\x0a\x80\x47\x45\xa4\x3f\x72\xcd\
\x8a\xcc\xca\x1d\x5a\xca\xfa\x79\xcd\x50\xd5\x23\xbb\xfe\x93\x8e\
\x75\xd0\x5b\xe3\x75\x15\x96\xe9\x70\x00\x6b\xaa\xea\x9e\x00\xfa\
\x54\xb5\xe3\xdd\x1b\x3a\x0a\x5e\x85\x50\xd5\x0f\xa8\xea\xcd\x19\
\x6a\x98\xcd\x32\x36\x22\xce\x55\xd5\x23\xdc\x7d\x46\xd4\xc0\xe4\
\x46\xf5\x03\xab\xa8\x3e\x2b\xc3\xcd\x06\xaa\xda\xcb\xe3\x69\x19\
\xe7\xcf\x52\xd5\x51\x70\xa3\x7c\x83\x33\x8e\xa9\xd2\xb7\x65\xbc\
\x27\x7b\x57\xfe\x13\xa2\x8f\xc7\x5f\x84\xf7\x0f\x91\x36\xe2\x02\
\x70\xe1\x5e\xa1\x55\xe7\x50\x00\xf7\x00\xd8\x8e\xb3\x8c\x06\x06\
\x80\x8a\xa3\xef\xdf\x09\x60\x73\x11\x99\x62\x82\x37\x82\x0d\x00\
\x25\xd6\xbd\x8f\xc7\x32\x8f\xf3\xab\xec\x49\xf5\xf3\x9c\x05\x3c\
\x96\xdc\x35\x79\x41\x82\x4f\x39\x28\xaf\xb9\x59\x7c\x51\x55\x77\
\x66\x1f\x88\xaa\xd8\x49\x70\x08\x2e\x2c\x8b\x34\x33\xaf\xa2\xaa\
\x7f\x00\xf0\x33\x5a\x70\xca\x11\xd5\xac\xe4\x4c\xa4\xa7\x00\xd8\
\x56\x44\xa6\x51\xbd\xab\xb4\x9b\x4b\xd5\x62\x08\xeb\x1e\xfb\xd4\
\x7b\x4d\x5e\x0b\xf1\x32\x83\xb3\xdb\xa7\x9f\x83\xa0\x7f\xbe\xb8\
\x0d\xe9\x13\x8c\xac\x1b\xbb\x59\x12\x9c\x45\xb3\x8c\x52\x68\xfe\
\x8b\xc1\xca\xf7\x74\x23\x52\x38\xcb\x54\x28\x48\x8f\x00\xf8\x84\
\x88\x7c\x5b\x44\xfa\x47\xf8\x2c\x33\x5c\x61\xef\xe3\xcf\x5c\x97\
\xbd\x0f\xc0\x7b\x01\xac\xcb\x35\xab\x69\x12\x26\x20\xf6\xae\x27\
\x03\x58\x87\xb3\xce\x00\x39\x19\x51\x3a\x78\xbd\x08\x36\x33\x97\
\x06\xf0\x3d\x00\x07\xf1\xe7\xc1\x36\x33\xa7\x00\x38\x51\x44\xe6\
\x39\x03\xc0\x48\x9e\x65\x3c\xd4\x39\xc3\x79\x4f\xd6\x6a\x06\x10\
\x7f\x4d\xc1\x2d\xe0\xf3\x6a\xb3\xf9\x96\xd1\x80\x98\x09\xe0\x14\
\x06\x93\x3f\xdb\xa9\xdd\x70\x03\xe3\xa6\x00\x1e\x8d\xcd\x8a\x5d\
\x3b\xe3\x70\x76\xb0\x59\x66\x5b\x00\x7f\xa5\xd0\xd8\x8c\x12\x6e\
\x66\x9a\xba\x36\x1d\xc0\x2e\x22\x72\xa4\x09\x8d\x88\x74\xa4\x5f\
\x7c\x0b\x31\x8a\xed\x33\x9a\xc7\x1e\x1e\xc7\x56\x51\xbd\xec\xdc\
\x31\x3c\xf6\xf2\x38\x31\xa7\x32\x17\xa8\x8e\xf7\xf2\xd8\xc3\x01\
\xef\x22\x00\xaf\x51\x16\xec\x1d\xda\x71\x0d\x1e\x07\xd4\xa9\x2b\
\x67\x1c\x67\x66\x1e\x03\xe0\x64\x00\xdf\x60\xc3\x95\x22\x6d\xe2\
\xcd\xcc\xbf\x71\xc9\x8b\x46\x8c\x99\xb9\x0e\x58\x5d\xaf\x03\xb0\
\x75\xc4\xb4\xac\xf4\xd8\x84\xeb\x7c\xa6\x2a\x5d\x40\x75\x29\xbc\
\xa6\xcf\xce\x69\xf5\xe0\x43\xb3\xb8\x39\xc1\x59\xb9\xe6\xaa\xea\
\x1b\x00\x96\x8b\x94\x6d\x9c\x5d\x1a\xde\xab\x63\x05\xc7\xd4\x28\
\x57\xe8\xa1\x2e\x22\xad\x51\x4a\x14\x9a\x0d\x01\xfc\x04\xc0\x46\
\x4e\x65\xe8\x09\xce\xb7\x99\xe7\x75\x00\xc7\x89\xc8\xc5\xe8\xa0\
\xe0\x11\xd4\xbd\x1b\x59\x60\x9b\x17\x65\x5d\x75\xb0\x8e\x2d\x22\
\x33\x00\xcc\xa8\xf1\x5c\x3b\x3e\x0b\xe0\xd9\x3a\xcb\x99\x17\xea\
\xee\x5b\x1d\x27\x38\x7e\xdd\xd1\x2a\x67\x2f\x55\x3d\x96\x31\x00\
\xc6\xd5\xb0\x99\xf9\x27\x00\x47\x8a\xc8\xd3\xce\x25\xba\x23\x84\
\x86\x6b\xaa\x86\xd7\x08\x8d\xfa\xef\xbb\x41\x6d\x00\xb2\xda\xa6\
\x5a\x6c\xb6\x4e\x68\xcf\x7a\xd1\x51\x82\xe3\x3a\x43\x59\x55\x97\
\x00\xb0\x01\x7d\xf5\xdf\xd3\x84\xb2\xda\x22\x76\x43\x97\x7a\x2f\
\x96\x30\xc9\x04\xe9\x6d\x32\x99\x7f\x88\x0e\x9a\x65\xb0\xa8\xc3\
\x57\x54\x75\x3d\x00\xbb\x00\x18\xcf\x9f\x06\x1b\x39\x4d\x48\xfa\
\x01\xdc\x26\x22\xb7\x35\x22\x3c\x3c\xbf\xde\xd9\x6a\x44\x19\x4e\
\x3a\x46\x70\xdc\x1e\xca\x04\x00\x47\x01\xf8\x02\x4d\x87\xad\x80\
\x59\x50\xb2\x36\x33\xef\x06\x70\xb8\x88\xfc\xaf\x73\x89\xee\x14\
\xa1\xb1\x44\x4f\x7b\x03\xf8\x05\x17\xdb\x8d\xe0\x24\x55\x3d\x55\
\x44\x4e\xee\x04\x1f\xfe\xe1\x86\x8e\x10\x1c\x27\x34\xeb\x03\xf8\
\x15\x6d\xec\x70\xeb\x8c\x66\x66\x37\x0b\xe9\xff\x70\xaa\x59\x05\
\xc0\xa9\x00\x4e\xe5\x3a\xa8\xa7\x93\xf6\x65\xdc\x4c\xb3\x0c\x23\
\xe7\x8c\xe1\xe2\x3a\x73\xa3\x2e\x02\x9b\x79\x7b\x28\x3c\x57\x89\
\xc8\x43\x9d\x34\xa3\x0e\x07\xb4\x5d\x70\x38\xda\x95\x55\x75\x13\
\x06\xa0\x5b\xd2\xed\xea\xc6\x3a\x79\x33\x61\xa3\x6c\x91\xf6\xfa\
\x23\x44\x64\xaa\x2b\x57\xae\x42\x13\xd0\x3b\x62\x7e\x21\xc6\x54\
\x58\x17\xc0\xd2\x2c\xff\xa8\x06\x1f\xd7\xcf\xf7\xbf\x19\x80\x87\
\xb2\xd4\x3c\x5f\xa6\x24\x58\x8b\xd0\x56\xc1\xe1\x22\x53\x55\x75\
\x79\x00\x7f\xa0\xd0\x94\x22\xac\xd6\x56\xa8\x11\xde\x8a\x76\x1e\
\x37\x33\xdf\x22\xc1\xb0\x9c\xb7\xea\x62\x03\x48\xe4\x3b\x5f\x0e\
\xeb\xdc\xef\xad\x32\x0b\x67\x95\x3b\x4c\xa6\x6b\x8b\x75\x63\x39\
\x2f\x76\x2f\xe7\x49\x19\x96\xa9\x23\x02\x02\xb6\x1b\xed\x9e\x71\
\x4c\xf5\x38\x1d\xc0\xca\x91\x7d\x94\x4a\x0d\x1c\xa8\x46\x51\x00\
\xf0\x02\x67\x99\xab\xd1\x26\xcf\x4c\xd7\x41\x2b\xaa\xba\x29\x80\
\xf5\x69\xea\xbd\x4e\x44\x16\x64\xa8\x8b\xef\xad\x12\xe4\xa3\xde\
\xb6\x5a\x33\x52\x26\x1f\xb5\x67\x7b\x7a\x52\x3e\x29\x22\x37\x59\
\x62\xde\x6e\x5f\x13\xb5\x4d\x70\xdc\x22\x77\x4d\x00\xfb\x66\xec\
\xd6\x5b\x27\x78\xb1\x49\xa6\x69\xeb\x68\x0b\x00\xdc\x0c\xe0\x74\
\x11\x99\xd1\xae\xcd\x4c\x4b\xe9\xce\x76\x38\x87\x46\x11\xc3\x83\
\xaa\x7a\xb0\x88\x3c\x62\xe5\x73\xe5\x5f\x2d\xe3\x96\xe6\x0e\x1c\
\xc3\xb2\x00\x96\x88\x6c\xf2\xad\xc2\xa3\x65\x25\xb0\xcd\xe1\xe5\
\xb8\x69\xb9\x9b\x2b\xef\x35\x00\xf6\x15\x91\xb9\xdd\x2e\x3c\xed\
\x9c\x71\x8c\xaf\xb4\x1b\xe9\x18\x7e\xb6\xb1\x99\xe6\x9f\x00\x8e\
\x20\xb5\x7f\x41\xb3\x1e\xec\x5f\x78\xbb\x16\xc5\x01\x4f\xee\x27\
\x00\x0e\x0b\x0c\x21\x1b\x02\xb8\x43\x55\x0f\x13\x91\xdf\x04\x1e\
\x89\xab\x5a\x55\x78\x34\xe3\xc6\x54\x00\x3b\xb9\xb6\x85\xa3\xca\
\x9f\x05\xe0\xab\x6e\x80\xb2\x6b\x97\x53\xd5\xf1\x00\xfe\xed\x84\
\x66\x73\x00\x17\x03\x58\x3b\x18\xb0\x76\x05\x70\xb5\xaa\xee\xc2\
\x80\x23\x5d\x2b\x3c\xed\xe4\xaa\x59\x83\x4f\x0e\x46\x41\xfb\xfb\
\x2d\x00\xbb\x8b\xc8\x5f\x44\xe4\x1d\xa3\xea\x37\xe3\x03\xe7\xff\
\xdf\x46\xa1\x11\x0a\xcd\x14\x0a\x4d\xc9\x99\xc8\x7b\xd8\x61\x27\
\x02\xb8\x4c\x55\xbf\xe7\xce\x1f\xed\x66\x1c\xdf\x66\x00\xf0\xac\
\x6d\x8a\xba\xba\x5a\x2e\x9c\xa7\x83\x62\xd8\xb5\xcb\x03\x58\x8e\
\xbc\xbd\x92\xaa\x1e\x06\xe0\x56\x0a\x4d\xc9\x6d\x04\x17\xf9\xff\
\xd6\x00\xae\x51\xd5\x09\x59\xcc\xe1\x6e\x40\x27\x54\x7a\xd5\xc8\
\xae\xbd\x00\x98\x2a\x22\x4f\x3a\x52\x5e\xd3\x3e\xe0\xa2\xb7\x1d\
\x8b\x5c\x37\xd3\x54\x28\x34\x87\x67\xb0\x17\x8a\x8e\x5c\x7a\x1c\
\x80\x1b\xa9\x3e\x55\xe8\x82\x8c\x88\x25\xec\x79\x4b\xc8\xe4\xea\
\x6a\x31\x13\x9e\x0b\xce\xb5\x35\xd2\x58\x00\xe3\xd8\xce\x17\x90\
\x86\x34\x3a\x42\x41\x82\x9b\xbd\xb6\xe1\xcc\xb3\x44\xb7\x0a\x4f\
\x27\x54\xd8\x36\xf0\xc2\x4e\x30\xdb\xac\x6e\x1c\x0d\x9b\xf6\x69\
\x43\x1d\x81\x81\x33\xcd\xb9\x81\xd0\xc4\x20\x6e\xa4\xdf\x9e\x1b\
\xb3\x87\x46\xce\xb7\xb6\x7b\x81\xf5\xf3\x75\xb5\xe3\x2b\xc1\xba\
\xd1\x63\x67\x00\xd7\x03\xf8\x92\xf3\x41\xca\xea\x1b\x3d\x6e\xe6\
\xb9\x56\x55\xc7\x77\xa3\xf0\xb4\xdb\xaa\x56\x0d\x16\xe4\xa1\xdd\
\xe5\x88\x22\x42\x42\x1d\x0c\x36\x08\x94\x28\x34\x47\x64\x08\x4d\
\xc5\x9d\x6f\xf7\x36\xd5\x6d\x2d\xfa\x01\xf9\x73\xe0\x3a\xf9\x0b\
\x56\x3c\x5f\x54\x1e\x5f\xa3\xfa\x3b\xc9\xa9\xc3\x76\xfd\x99\x3c\
\xc6\x7c\x90\xb2\xca\x63\xc2\x73\xb5\xaa\xee\xda\x6d\x6b\x9e\xae\
\x1a\x25\x9a\x09\xf3\xe5\x11\x91\x52\x8d\x9f\x7e\x0a\xcd\x8f\x06\
\x11\x1a\xcf\x78\xf6\x9d\xd0\x5b\xd6\xc2\xcc\x07\xe6\x44\x56\x4d\
\x70\x5e\x65\xa6\xb3\xf0\x77\xfb\x3f\x66\xd5\x0c\xcb\x13\xf3\xcf\
\xdf\x86\x33\x4f\x57\xad\x79\x3a\x79\xc6\xe9\x48\xf8\x10\xab\xaa\
\xba\x2f\x80\x1d\xb8\x7b\x5f\x2d\x9f\xa7\x75\xba\x65\x49\x30\xad\
\xe6\xc2\xf0\x2d\x06\xb0\x38\x2b\x08\xfb\x8a\x41\x06\xba\x59\x11\
\x5f\x18\x2b\xa7\x88\x48\x9f\xaa\xbe\xe2\x36\x4f\xc3\xf2\xc5\x82\
\x9b\x0b\xd7\x3c\xf7\x93\x17\x57\x08\xea\xe9\x67\x9e\x2b\x55\x75\
\xb7\x6e\x99\x79\x92\xe0\xd4\x0f\xdb\x77\xb9\x80\x6b\x82\x7a\x11\
\x4b\xf3\x61\x42\x73\x8a\x88\x9c\x8e\x77\x05\xf4\x71\x7a\x27\x2e\
\x3f\xc8\x3a\xc8\xc8\xa9\xaf\x02\x98\x9b\x71\x4e\xc1\xcd\x48\x93\
\x23\x82\xe3\x61\x82\xda\x47\x1f\xa4\x73\x59\x9e\x3e\x00\x97\x54\
\x11\x9e\x6d\x69\x6d\xdb\x1d\xc0\xbc\x91\xce\x30\xe8\x8a\x69\xb5\
\x59\xb0\xd0\x51\xaa\xba\x05\x85\xa6\x54\xe7\xa7\x1c\x69\x73\xeb\
\xa8\xa7\x8a\xc8\xb7\xe9\xd2\xdb\x2b\x22\xd7\x01\xd8\x1c\xc0\x5d\
\x6e\x8d\x13\xaa\x60\x65\x27\x88\x7f\xa6\xd1\xa1\x18\xe9\xb0\xd6\
\xc9\xaf\x73\x33\x49\x29\x72\x3f\x33\x3f\x3f\x03\x60\x7b\x11\x39\
\x97\x66\xfb\x5e\x11\xf9\x2d\x80\xcf\x3b\xa1\x09\xd5\xb6\x7e\xaa\
\x6d\x97\xe6\x1c\xbd\xa6\x2d\x48\x82\x43\x78\x3f\x74\x1e\x63\x2f\
\xde\xbe\xdb\xc8\x75\x9c\x9e\x3a\x3e\xb1\x85\x77\x91\xc9\x61\x4f\
\x76\x3c\xb9\x7e\x6e\x46\x3e\x0d\x60\x47\xee\xe0\x17\x5d\x87\x37\
\x93\xbd\xf9\xee\xdf\x00\xe0\x34\x96\x39\xa6\x22\x59\x9a\xf8\xcb\
\x18\xf2\xaa\xe8\xcc\xdf\x65\xb7\x87\xd4\x43\xc7\xbd\x2d\x44\xe4\
\x0e\x96\xc1\x97\xe7\x0a\xb2\x3c\xfa\x23\x5c\xb9\x5e\xde\x67\x57\
\x00\x5b\x55\x8b\x49\x36\x12\xd0\xb0\xe0\x30\xe8\x5e\x71\x90\xcf\
\xb0\x10\x4c\x53\x2b\xb8\x88\xb7\x05\xbf\x46\xca\x6f\x1d\x65\xf5\
\xc8\xba\x00\x6e\x16\x88\x7d\x42\xd8\x4c\x71\xae\x88\x9c\xc4\x4e\
\xe6\xf7\x96\x2a\x78\x57\x2f\x7c\x5b\x44\x0e\x05\xf0\x59\x5a\xc5\
\x4c\x00\xe7\xd2\x05\x63\x27\x11\xf9\x4f\x11\x79\xd3\xd5\xa7\x10\
\x7b\x07\xdc\x14\x3d\x0c\xc0\x16\x00\x7e\x44\x4e\x5c\xd1\xa9\x5b\
\xa7\x31\x69\xd3\x2b\x21\x6f\x8f\x86\x0d\x9b\x79\xbe\x9c\xe1\xca\
\x60\x82\xfb\xfe\x06\x5f\x45\xad\x10\xb6\xd7\xc2\xbe\x66\x7f\xe7\
\x35\xd3\xd5\xb5\xc6\xf1\x79\x44\x6a\x5d\xfc\x75\xba\x9f\x87\xe3\
\xcc\x8d\xe5\x68\xfa\x7e\x00\x8f\x01\xb8\x8c\x24\xcb\x58\xf9\xd7\
\xc8\xb8\x5d\xe8\x1c\x57\xf5\xd1\x3c\x3e\xe2\xf6\x77\x2c\x45\x85\
\xe7\x8b\xed\x0b\x60\x25\x06\xba\x58\x17\xc0\xa7\xf8\x9c\x1b\x45\
\xe4\x19\x2c\xa2\xfe\x8b\x13\xbc\xe8\xda\xc2\x42\xcb\x8a\xc8\xdd\
\x00\xee\x26\xb9\x76\x27\x1a\x2d\x6e\x13\x91\x87\x5d\x9b\x0c\x60\
\x45\x93\xc9\x2e\x00\xb6\xaa\x52\xaf\x02\xd3\x73\xb4\x12\xe5\x88\
\x6b\xbd\x91\x52\x73\x21\xe9\xd6\x2c\x38\x61\x07\x22\x39\x73\x99\
\x41\xee\xf1\x82\x88\xbc\x38\xe4\x52\xb6\x08\xce\x81\x6e\x25\x00\
\x57\x02\xd8\xd8\xfd\xfc\x65\x55\xfd\xa2\x88\xfc\xc3\x54\x28\x00\
\x15\x76\x9c\x95\x79\x4e\x48\x13\x7a\x8d\xd4\x96\x18\x73\x79\x7d\
\xee\xc8\xc3\x5d\x03\x00\xeb\xd9\x7e\x95\xf3\x36\x2d\x91\x95\x7c\
\xa1\xa3\xfd\x1f\x03\xe0\x52\x11\xd9\xcf\x95\x7f\x94\xeb\x44\xf6\
\xdd\x32\x8c\xd8\xb2\x04\xbf\x7a\x07\xc0\x2c\x11\x79\xd5\x66\x10\
\x3e\xa7\x57\x44\x66\x32\x0d\x3a\xdc\xf7\x9a\x31\x28\x16\x59\xae\
\xe3\x01\xec\x1f\x31\x72\x98\x01\xe3\x72\x11\xf9\x6b\x4c\xf8\x9a\
\x88\x09\x64\x92\x7b\x4e\x5e\x91\xef\xc8\x72\xe7\xb4\x7f\x8d\xe5\
\x02\x68\xaf\xae\xaa\xa7\xaa\xea\x34\x55\x9d\x57\x25\xf0\xb6\x61\
\x8e\xaa\xfe\x3f\x2c\x5a\x43\x48\xe4\x9e\x7f\x0b\x02\x6a\x5b\x80\
\xed\x5f\xc2\x8d\x92\x2d\xa8\x93\x05\xe9\x5e\x81\xf5\xb1\xa0\xdb\
\x25\x57\x86\xd9\xaa\xfa\x19\x2b\x2f\xeb\x30\x49\x55\x9f\x0b\xca\
\x6c\x01\xbe\x4f\xaf\xf2\xbc\xfb\x32\xea\xf9\x47\xfe\xde\xeb\xce\
\x3d\xce\xdd\xd3\xa7\xa5\x50\x55\xbd\x4e\x55\xc7\x05\xf7\xde\x5c\
\x55\x4f\x57\xd5\x7b\x99\x52\xd1\x82\x87\xdb\xf3\x5e\x63\x3b\x9f\
\xad\xaa\xdb\xba\xb6\x17\x55\x1d\xc5\x35\x5d\xb5\xdc\x36\xd6\x56\
\xdb\xbb\x54\x26\x95\xe0\x19\xaa\xaa\xff\x60\xfb\x48\xc6\x1a\xb1\
\xd6\x77\x93\x15\x74\xbd\x11\xd8\xb5\x57\x21\xa3\x3f\xa9\xea\x13\
\x19\xef\xe6\x9c\xf0\xdd\xd4\x5a\x01\x71\x8d\x7c\x98\xaa\xce\x0c\
\x0a\x55\x71\xf9\x2d\xc3\x8f\x8f\x16\xbf\xb7\x7f\x01\x68\xb3\xe0\
\xb8\x8e\xb0\x12\x73\x72\xc6\x5e\x8e\x2f\xff\x19\xae\xbc\x6b\xab\
\xea\x7c\x57\x7f\x7f\xee\x97\x29\x60\xbd\x2e\x71\x52\x0f\x8f\x97\
\x07\xe7\x5a\x7d\x1f\x72\x11\xfd\x27\xa9\xea\x65\x41\xdb\xc6\x3a\
\xc1\x35\xaa\x3a\x51\x55\x77\x51\xd5\x3b\x35\x8e\xac\x88\xfc\xf6\
\xcc\x83\x5d\x3b\x54\xcb\xa5\x69\xf5\x5e\x8d\x39\x7f\xc2\x72\xd9\
\xff\x6f\xa9\xea\x47\xfc\x35\x43\x78\x3f\xb5\x08\x4e\x56\xbf\x0b\
\xeb\xdc\x12\xc1\xa9\x9a\x41\xcb\x91\x11\xcf\xe1\x46\xd8\xb2\x2e\
\xca\xbc\xa9\x27\x59\xc1\xb7\x8b\xee\xdc\xbd\x87\xd2\x90\xcd\x84\
\x53\xcf\x56\xa0\x35\x6a\xbd\x8c\x68\x37\x46\xb2\xac\x00\x38\x1e\
\xc0\xf5\x54\x83\xc6\x50\xe5\x8a\x6d\x78\x3e\x17\x61\x27\x9b\x1b\
\xc3\x74\x2b\x02\x8f\x76\xed\x6a\xb4\x5a\xad\xcb\x8c\x07\xfb\xb8\
\x60\x79\xe1\xfb\xe9\x61\x79\x76\xe1\x3a\xe2\x1a\x2e\xf4\x11\xbc\
\x17\x4f\xa9\x51\x57\x0f\x33\x41\x7f\x8c\x6a\xe0\x6d\xaa\xba\xbe\
\x99\xb1\x23\x6d\x25\x58\xa4\x12\x5e\xc6\x3d\x25\xaf\xa2\xa9\x33\
\xb1\x1f\x46\xdf\xa1\x9e\x9c\x36\x3f\xb3\xfa\x5d\x2e\x2a\x5a\xb5\
\x91\xc1\x7c\x45\xbe\x45\x07\x2b\x33\x41\xf6\xd4\x51\x40\x13\xac\
\xbc\xc2\x9c\x56\x85\x13\x9a\x15\x01\xdc\xe4\x84\x26\xa4\x9a\x18\
\xac\xfc\x25\x26\x2c\x9a\xea\x62\x4b\xfb\xf3\x8d\x0e\x33\x23\x72\
\x0f\x83\x09\x4e\xd8\x6e\xa3\xa8\xce\xde\x01\xe0\xc3\x19\x4c\x69\
\x0f\xd3\xeb\x57\x77\x1d\x17\xc1\x7b\xf1\xd7\x8a\xab\x47\x8f\xb3\
\x7c\x95\x00\x6c\x09\xe0\x2e\x55\xdd\x3f\x43\x78\x8c\x01\xf0\x7d\
\x0a\x68\x29\xd2\x56\x3d\xb4\x0c\x5e\xc6\x91\xb9\x63\x0d\x41\xcd\
\x44\x54\x0d\x72\x1d\x6c\x63\x06\xee\x8b\xa5\xb9\xb0\x06\x8a\xbd\
\xa4\x01\xb7\x6c\x6e\xb1\xeb\x47\x30\xd3\xdc\x58\x45\x68\xc4\xed\
\xc6\x87\x24\xcb\x75\x5d\x04\x9e\xb0\x9e\x6f\x72\xf7\x7e\xc0\xa3\
\x79\xb4\x28\x96\x36\x58\xd9\xf5\xe3\x19\x35\x1f\x19\x54\x1c\x0f\
\x4f\xea\xac\xb8\x99\xdd\x9f\x5f\x0e\xca\x6e\x33\x8e\x77\x41\xb7\
\xbf\xcb\x74\x2b\xf8\x95\xaa\x4e\x62\x6e\x9f\x85\x59\xe8\xd8\x5e\
\x9b\x03\x38\x32\x32\x2b\xdb\xf3\xaf\x16\x91\xa3\xf0\xee\xcc\xda\
\x6f\x6d\xed\xca\xdb\xaa\x00\x8e\xb5\xc6\x56\x68\x09\xb2\xd6\x0f\
\xf6\xc2\x4e\x72\x23\xae\x04\xbf\x0f\x9b\xcd\xad\xc0\x7a\x76\xc3\
\x20\x42\x03\xd7\xc1\xbc\x5a\x52\x74\x2f\x2b\x46\xb2\x9c\x43\xab\
\x5a\x18\x7c\xcf\x0b\x8e\xdd\xcf\x3f\x4b\x9c\xba\xe3\xef\x1b\xa3\
\xe6\xc4\xca\xe8\x21\x83\x58\x39\xc3\xf2\xfb\x3a\x9d\xab\xaa\xb3\
\x39\x73\x14\xdd\x00\xb2\x6d\x64\xb3\x13\xee\xf7\x7b\x54\x75\x33\
\x86\x09\x7e\x4d\x44\xe6\xd4\x10\x74\xa4\x19\x68\xeb\x1e\x61\x6c\
\xa1\xe4\x63\x01\x6c\x17\x11\x12\x7b\xa1\xbf\x23\xbd\xe2\x75\xb7\
\x9e\xf9\x2e\xa7\xff\x18\x3d\xbd\x2d\x70\x23\x67\xb8\xa6\x89\xd5\
\x69\x2e\x80\x3d\x68\x96\x3e\xbd\x46\x92\xa5\x75\xa8\x97\x38\x52\
\x87\x1c\x2d\x4f\xeb\x9f\xc9\x75\x42\x88\xac\x74\x22\xff\xa6\x6a\
\x38\x96\xae\xcc\xe1\xfa\xc8\x3f\x43\x00\x3c\x49\xef\xcd\x07\x00\
\x3c\xcf\xef\x57\x60\x44\xd4\x1d\x01\xac\xc3\xf3\xc3\x3a\x59\x28\
\xdd\x9f\xa9\xea\x23\x22\xf2\xa8\xa5\x17\xe4\x2c\x1a\x1b\xc5\xed\
\x3b\x73\x49\xe8\x03\xf0\x9a\xaa\xce\x04\xf0\x32\x69\x3b\xcf\x00\
\xb8\x57\x44\xee\x6d\x12\x77\xcd\xde\xd3\xe3\x00\xbe\x98\x61\x8e\
\xfe\x31\x4d\xff\xb1\x81\xa7\x75\x70\x16\x8d\xfd\x02\x2b\x90\xb7\
\x3a\x9c\x93\x71\xed\x1f\x02\xab\x84\x5d\x7b\x1b\xda\x60\x55\x73\
\xcf\xf0\xd6\xb3\x30\x37\xa4\x3d\xf7\x2d\x55\xdd\xc6\x5d\xbb\x87\
\xb3\x22\x56\x33\x87\xf6\xf1\x1e\x97\x84\x75\x84\x33\xc3\x73\x87\
\xfb\x61\x3e\x3f\x96\x9f\x52\x83\xac\xd5\x8f\x32\x30\xbc\xdd\xe7\
\x60\x57\xde\xd0\x72\x64\x75\xb8\xae\x4a\x5b\x8c\x52\xd5\xcf\xa9\
\xea\xe3\x19\xed\x60\xff\xdf\x61\xcc\x03\x2c\x32\xd7\xcf\x0a\x9e\
\x13\x96\x39\xf6\xbd\xc7\x29\xfe\x7d\xd4\xf0\xde\x06\xcb\x01\xfa\
\x40\x95\x6b\x6f\x09\xea\x93\xaf\x55\xcd\xd1\x26\xd4\x1d\x0b\x54\
\x49\x4e\x77\x66\xd7\x22\x73\xcb\x17\x6b\xcc\xf2\x9b\x0b\x9c\x45\
\x68\x0c\x63\xb6\xad\x97\xb1\xb8\xb5\x99\x66\x57\x11\xf9\x0b\xeb\
\xd4\x23\x22\x7f\xe4\xec\x79\x5f\x06\xc9\xd2\x16\xd8\xbd\xbc\xc7\
\xef\x63\xe5\xe0\x28\x6b\x9b\x81\x57\xba\xe7\x97\x02\x3d\xdd\x8f\
\x9c\xbf\x23\x5f\xec\x41\x9a\xb3\x7b\x44\xe4\x22\x00\x87\x64\xf8\
\xc6\xd8\xcc\xb8\xb3\xaa\xfe\x22\x78\x37\x45\x5e\xdf\x27\x22\x97\
\x03\xd8\xc4\x95\xc3\xab\x54\xf6\xff\x96\x00\xf6\xb2\xf8\x06\xcc\
\x4c\xf0\x3b\x67\x99\x1b\x50\x45\xa7\x7e\xda\xcc\x65\xbb\xfa\x66\
\xc5\x3b\x49\x55\xb7\x68\xa2\xbf\x8e\xd5\xcb\xd7\x71\x14\xfb\x60\
\x2e\x8c\xff\x2c\x3d\x19\x2e\x90\xb7\xc1\x5e\xd4\x2c\x11\x99\x49\
\x73\x6b\xbf\x51\x1f\x78\x6c\xbb\x11\xc0\xc1\xf4\xea\xed\x98\x59\
\x2b\xa4\xe6\x5b\x59\xe7\x30\x28\xc8\x54\x76\x30\x73\x38\x2b\x8a\
\xc8\xbf\xc8\xf8\xbd\xd0\x91\x2c\xbd\x6b\xb1\xa9\x53\x27\x89\xc8\
\x35\x55\x82\x7f\x58\x87\xf9\x1e\xfd\x5a\xe0\xac\x60\x95\x40\xad\
\x38\x41\x44\xf6\x12\x91\x37\x8c\x2f\xe6\x78\x62\x17\x52\x78\xfa\
\x23\x6d\x6d\xe6\xf3\x03\x00\xac\xc1\x85\xfa\x42\x67\x3b\x23\xb1\
\x8a\xc8\x1c\x00\x9f\x61\x4a\xf9\x50\x78\xac\x5d\x8e\xe1\xc8\x6c\
\x66\xf1\xdf\xb8\x7e\x61\x24\xd3\x30\x34\xb1\xdf\x9a\xb0\xe0\x1e\
\x3d\x4e\x78\xb6\x72\xe5\x1c\x2a\xd4\xf7\xbb\x76\xf4\xc1\x6a\xd2\
\xdf\x7e\xca\x42\x73\xb0\x4a\x90\xa6\xce\x60\xeb\x82\xc3\x38\xd3\
\x8c\x0a\x48\x8d\x65\xae\x8f\xde\x16\x91\x43\x48\x6c\x7c\xdd\x09\
\xd0\x34\xd2\x60\x3e\x22\x22\xa7\xb9\x19\xce\x08\x96\x3d\x2e\xeb\
\x97\x59\x97\xe6\x8b\xc8\x41\xd4\xc1\x4f\x65\x00\x0d\xeb\x6c\xcf\
\x00\xd8\x59\x44\xce\x34\x96\x82\x17\x42\xee\xf5\x98\xf0\x7c\xdf\
\xcd\x32\x21\x0a\x5c\xd7\xc0\xd7\xd9\x45\xb1\x31\xea\xd4\x01\x34\
\x58\x84\xeb\x04\x70\x4d\xb4\x31\xdb\xc0\x82\xd0\x9f\x1f\xb0\xbc\
\xbd\xe9\xbb\x1a\x99\xd5\xca\xd1\x4c\x6d\x44\x58\x2e\x6b\xe3\x85\
\x7f\x77\x24\xc9\x73\x98\xc1\x46\x9e\xfb\x5d\x27\x8b\x6d\x5a\x7e\
\x41\x55\xaf\x34\xea\xbd\x5f\xc0\x52\xb5\x30\x02\xe6\xf9\x5c\x43\
\x6c\x0a\x60\x36\x80\x3b\x9d\xf9\x75\x94\x0b\xc3\x94\x39\xe2\x51\
\x88\x0a\x22\x32\x0d\xc0\x34\x55\xfd\x01\xf7\x47\x04\xc0\xed\x0c\
\xf4\x17\x25\xc5\x72\xc6\x2a\x71\x0f\x6a\xf7\x48\x5d\x6c\x70\x98\
\x05\xe0\x5f\xee\xbb\xc5\x60\xc2\x20\x22\x73\x54\xf5\x64\x72\xd5\
\xfc\x79\x66\x76\xde\x95\xe9\x1d\xed\xba\x2f\xab\xea\x54\x7a\xbc\
\xbe\x8f\x91\x76\x26\x31\x86\x75\xde\xfd\xa8\x14\x89\x6e\x6a\x3c\
\xbc\xfe\x3c\x0a\x30\x62\x05\xc7\xf4\x69\x46\xe2\x9f\x12\xf1\xf3\
\x37\x61\xfa\x24\x80\xef\x89\xc8\xd1\x81\x7a\x62\xf7\xd1\x77\xdf\
\x87\x16\x45\xe4\x25\xae\x97\x80\x77\xbf\x1c\x2d\x22\x0b\x44\xa4\
\x8f\xff\x4f\x62\xa7\x5a\x81\x24\xcb\x32\xd7\x4f\x2f\x02\x98\x2e\
\x22\xf3\x1d\x8b\x77\x34\x5d\x01\xae\x77\xf7\xcb\x12\x1a\x6f\xd5\
\xfa\x25\xad\x63\xa1\xd5\xc8\xf6\x80\x4e\x14\x91\xd7\x07\x31\x01\
\x9b\x7f\xce\xef\xb9\x4f\xb7\x46\xe0\x2e\x0d\x3a\xd1\xc1\xbb\x3a\
\x70\x8d\x74\x39\x16\x09\xf2\x32\xb4\x12\xae\xc4\x0d\xd9\xb5\x18\
\xb9\x67\x5c\xc6\x20\x35\x54\xd8\xfd\x96\x55\xd5\xbd\x82\xb5\x9e\
\xcd\x9c\x2b\x05\xe7\xb6\x04\x23\x56\x70\x08\xe5\x0b\x3e\x96\x34\
\x93\x2d\x22\xa6\xd8\x12\x80\xa3\x54\xf5\x41\x11\xb9\x34\x2b\xb5\
\x87\xa9\x6e\xe6\x3a\xc0\xc5\xf6\x02\x55\x7d\x0f\x4d\xd8\x9f\xa2\
\x19\x7b\xd9\x88\x0a\xbc\x00\xc0\x0c\x55\xbd\x1b\xc0\x55\x00\xfe\
\x44\xdf\x7c\x71\x34\x9a\x6a\x21\x78\x8d\x99\xfc\x1d\x8e\xf8\xe1\
\x7a\xcd\xfe\xbf\x48\x44\x2e\x1c\x6c\xdf\x84\x6c\xec\xa2\x88\xcc\
\x57\xd5\x9b\xb9\x6e\x0a\xe3\x74\xaf\xa1\xaa\x4b\x72\xad\x65\x11\
\x87\xac\xdd\x8c\x4e\x34\x93\x9f\x47\x5d\x83\xef\x93\x83\xe0\xac\
\x61\x02\x5c\x05\x2d\x35\x45\x8f\x68\xc1\x09\x02\x55\xec\x0b\xe0\
\xde\x80\x6f\x25\x6e\xa4\xfa\x99\xaa\x4e\x13\x91\x69\x59\x23\xbf\
\x79\x35\xf2\x7e\xcb\x01\xf8\x1a\x13\x60\x85\x7b\x33\x15\xa7\x3a\
\x09\xb9\x6d\xab\xf3\xb3\x0f\x80\xa7\x38\x0b\xfe\x94\x6b\x97\x98\
\xbb\x33\xb0\x68\x16\x2a\xa9\xea\x9e\x00\x4e\x88\xec\xe0\xdb\xff\
\x0f\x00\x38\xc2\x5c\x03\xea\x68\xa6\x87\xac\x7a\xc1\xf7\x4b\x73\
\x46\x79\x23\xc6\x00\x70\xec\x67\x6f\x55\x1b\x9d\xd3\xde\x89\x56\
\x59\x4f\xe5\xe2\xcc\x36\x2c\x3c\x34\x87\x02\xd7\xd9\x9f\xa3\x1f\
\x89\x62\x71\x6b\x90\xb5\xc1\x12\x00\x7e\x4b\x75\x6b\x80\xd9\xd4\
\x98\xe2\x9c\x79\x3e\x4d\x33\xf5\x37\x28\x34\x65\xb7\x86\xf2\x16\
\xb7\x22\x16\x37\xd5\x9a\x35\x6a\x2d\x7a\x60\xde\xa9\xaa\x1b\x55\
\x21\x59\xda\xf3\x3e\xc0\xc0\x1d\x61\x68\x28\x1b\x00\x5e\x07\xb0\
\x37\x55\xc1\x7a\xb3\x37\x87\x34\x21\xeb\x74\x63\x03\xff\xa1\xb0\
\x5d\x2d\xe8\x61\xc5\x59\xb4\xf2\xca\xf4\x20\xce\x50\x11\x7e\xda\
\x4e\xf2\x1c\x49\xa8\xd0\x6a\x76\x33\x69\x44\xc5\x60\x54\x36\x95\
\x6d\x1d\xfa\xe4\x2f\x86\x20\xab\xc0\xa9\x00\xfe\xc8\x30\x4b\x66\
\x6a\x2d\xba\x91\x2e\x2b\x56\x41\xc1\x09\x92\xed\x01\x4d\x06\x30\
\x55\x55\x3f\x1f\x0a\x8f\xf3\xb8\x1c\x0f\xe0\xb7\xcc\x1d\x14\x5a\
\x07\xed\x79\x07\x33\xb9\x6f\x6f\x03\xe6\xd8\xe1\xaa\x75\x68\xc6\
\x27\x17\x8c\x48\xc1\x71\xe6\x60\xf3\xa8\x54\x5b\xc0\x8b\xc8\x77\
\x38\x7a\x17\x02\x6b\x92\x6d\x72\x7e\x8e\x11\x5e\x7c\xb0\x09\x1f\
\xeb\xf9\x5b\x6e\xe6\xf0\x23\x9c\x06\x9b\x7e\x70\xdf\x97\x02\xd5\
\xa2\xe0\x9e\x37\x0e\xc0\xa5\xaa\x7a\x48\x20\x3c\x05\xce\x1c\x87\
\x72\x7d\x16\x6e\xde\x9a\x3a\x78\xb4\x88\x5c\xc5\xba\xf5\x3b\xf7\
\xeb\x82\x33\x87\xc7\x60\xce\x66\x61\xca\x10\x2b\xfb\x3c\xee\x51\
\x85\x6d\x6b\x4c\x88\x85\x66\x77\x9a\x82\x73\xf3\xf7\x27\x24\xe3\
\x93\x0b\x86\xeb\x68\x53\x15\x11\x92\xe1\x78\x9a\x4f\x57\xa6\xc5\
\x6b\x76\x15\x12\x65\x85\x26\xe7\x3f\xb3\x73\x19\x41\xf4\x64\x5a\
\x8c\xfa\x23\x2a\x41\x16\x53\x59\x9c\x5a\x81\x40\x95\x43\x40\xb2\
\x3c\x5f\x55\x67\x70\x23\xd5\xdf\x67\xb3\xc8\x4c\xe3\x19\x0f\xbd\
\xaa\xfa\x5f\xe4\x87\xbd\x02\xe0\x15\xee\x17\x99\x60\x21\x83\x27\
\xa6\x5c\x03\x4e\x76\xf7\xf4\xe5\x9e\xe9\x03\x1c\xfa\xb4\x24\xc1\
\xf9\xbe\x9d\xf3\x0c\x42\x98\xf5\xac\x5c\x26\x83\x11\x23\x38\xbe\
\x73\x70\x21\xbd\x05\xd5\xa9\xf7\x72\x1d\x32\x89\xa3\x7b\x35\x98\
\x55\xc9\x52\x62\x14\x68\x08\xd8\x81\x66\xdb\x98\xaf\x4c\xd9\xed\
\xc0\xdf\x44\x22\xe9\xc3\x24\x75\x16\xb8\x01\xbb\x11\xf7\x45\x36\
\x75\x1b\x86\x21\xc9\x52\x01\x5c\xac\xaa\x1b\x70\x63\xd4\x66\xa4\
\xe9\x4e\x95\x34\xd8\xf3\x27\x70\x33\xd4\x30\x0f\xc0\x1b\xaa\xfa\
\x32\xef\xf1\x2c\x80\x1b\x98\x96\x7d\xa1\xa5\x8d\x33\x71\x45\x55\
\x97\x25\xb3\x02\xae\x3c\x26\x10\x4f\x58\x54\x4e\x2c\x0a\xdc\x5e\
\xe6\x9e\xd5\x52\x34\x1c\xac\xce\x19\x6b\x55\x7e\xd6\x60\xbc\x03\
\xb4\xa8\x03\xdb\x00\xf5\x28\xad\x98\x31\x92\xa7\xd1\x8a\x5a\x4a\
\x34\x1e\x31\x82\xe3\x54\x8f\x0b\x01\x1c\x98\x71\x8e\xf7\x57\x89\
\xc5\x38\x2b\x00\x78\x09\xc0\x75\xbc\x57\x89\xe9\xe3\x7f\xc2\x73\
\x42\x07\x3e\x8b\x8b\x76\x2b\xf7\x4f\xee\x8f\x3c\xf3\x71\xfe\x7e\
\xa6\xaa\xee\x4a\x36\xf1\x07\x23\xc2\x53\xa6\x25\xeb\x1c\x11\xd9\
\x5d\x17\x45\x9b\xff\x35\xf7\xa0\x7a\xdd\x6c\xe0\x51\x76\xf7\x18\
\xcf\xcf\x2a\x2e\xf0\xc8\x71\xaa\x7a\xac\x88\xfc\xc0\x59\x0b\x8b\
\xb4\xe6\xfd\x37\x9f\x19\xeb\x64\xb7\xf1\x68\xe7\x2e\x03\xe0\x14\
\x00\x1f\xe7\xcc\xbd\x14\xda\x87\xf9\x34\xf6\x0c\x80\xaa\xbe\x9d\
\x47\x01\x46\xc4\x1a\xc7\x22\x6c\x72\x8f\xe3\xc0\x20\x72\x66\xe8\
\x4e\x1c\x0b\x0c\x08\x77\xde\x6f\x45\xe4\x0d\x00\xa3\x78\xcf\x43\
\xb8\xa9\x59\x0a\xda\xcb\x7c\x68\xce\x16\x91\xed\x44\xe4\x7e\xbf\
\xae\x70\x31\x07\x16\x06\x38\x14\x91\x6b\x38\xeb\xc4\x48\x96\x26\
\x3c\xbb\xa9\xea\xb6\x8e\x9f\x36\x8d\x9e\xa7\x59\x26\x58\x6f\x98\
\x08\x89\x96\x7d\x3c\xe7\x0c\x55\x5d\xd3\x11\x37\xfb\x55\x75\x3d\
\xee\x6f\x85\xae\xd0\x36\xbb\x5d\x63\xed\xc2\xd0\x59\xd7\x02\xf8\
\x0a\x1d\xf9\x96\x72\xe7\x97\x83\xf6\x8e\xbe\xa2\x26\xaf\x3f\xc2\
\x78\x0e\x0b\xe3\x3c\xe4\xd5\xa7\x47\x84\xe0\xb8\x7a\x6c\xec\x04\
\x20\xc6\xa9\x32\x78\xf3\x70\xd9\x2d\xbc\x05\x80\xa5\x0d\xec\x67\
\x34\x99\xc3\x23\x66\x60\x1b\xa1\xa7\x88\xc8\x31\x26\x20\x24\xbe\
\x5a\x50\x43\x8b\x3b\xe0\x03\x1c\xf6\x90\x2d\xb0\x17\x80\x5b\x02\
\xe1\xf1\xe5\x3b\x26\xa8\xdf\xaf\xdd\xf3\x4b\xae\xdc\x21\xc5\x27\
\x24\x5a\x8e\xe2\x79\xbd\x00\xd6\x63\x19\x17\xa8\xea\xaa\x64\x3c\
\x8f\x77\xd7\xc1\xad\xa5\x6e\x12\x91\xc7\x28\xb8\x65\xc6\x5e\xdb\
\x94\x82\xe8\x9f\x69\x33\x77\x56\xa4\x52\x5f\x2e\x0b\x98\xd8\x14\
\xcb\x57\x24\xb6\x43\x25\xa7\x58\x07\xc0\x08\x12\x1c\x43\xb5\x11\
\xa7\xec\xf4\x61\x6f\x1e\xf6\xe1\x60\x4f\x66\x50\x3e\x0b\x38\xb1\
\xbd\x8b\xee\x5f\x70\xf7\x29\x02\x78\x10\xc0\xd7\x6c\x21\x5f\x8b\
\x7b\xb0\x23\x59\xf6\x03\xd8\xcf\xad\x83\xbc\x9e\xae\x00\xb6\x56\
\xd5\xb5\x6c\x73\x14\xc0\x15\x64\x28\xfb\x0e\x5a\x0c\x54\xc7\x4a\
\xc6\x88\x6f\xb3\xed\x7c\xce\x38\x5b\x02\xf8\x0b\x33\x49\x87\xb3\
\x8d\xe1\xcc\xe0\x1e\x3e\xb9\x71\xa8\xae\x6a\x30\x10\xd9\xec\x63\
\x33\x5f\x2f\xb3\x2f\x98\xfa\x9b\xa7\x01\xa1\x65\x18\x49\x6b\x9c\
\xc1\xe0\x47\xc3\x39\xdc\xf8\x7b\x95\x3c\xb2\xa7\x00\xdc\x22\x22\
\x77\xd9\xfe\x09\xcf\xdb\xc5\x75\x0a\xeb\x60\xd6\x69\x8e\xa7\x20\
\xf4\xd4\xe3\x53\xef\x48\x96\x33\x54\xf5\xbb\x00\x7e\x10\xf1\xcb\
\x19\x43\xb5\xf3\x29\x1a\x28\xfa\x01\x7c\x5e\x55\x2f\x27\x87\x6c\
\x4d\x72\xb2\x96\xe7\x67\x42\x95\x01\xc3\x3a\xfa\x87\x54\x75\x2b\
\xa6\x45\x2c\x06\x75\x82\x63\x20\xfc\x8a\xed\xd0\x43\xc1\x5d\x07\
\xc0\x7f\xba\x8d\xdc\x01\x55\x0a\x8e\x21\x9e\xa5\xc9\xfc\x89\x91\
\x94\xfe\x63\xa4\x0b\x8e\xe9\xd6\x73\x49\x57\x79\x9a\xa9\x2e\x5e\
\x07\xf0\x86\xed\xb4\x2f\x3c\x79\xd1\x8b\x2d\x71\x7f\x62\x63\x37\
\x3b\xc1\xcd\x36\x0f\x31\xb4\x52\x16\xb5\x7f\x30\x18\xeb\xfa\x52\
\xee\x0b\x2d\xe5\xca\x6a\x9d\x73\x73\x1a\x25\x16\x76\x34\x11\xb9\
\x96\x6b\x0d\x2b\xef\x12\xdc\x18\x5d\x8e\x56\xad\x0d\x00\x9c\x1c\
\x3c\xcb\xca\x7e\x96\x7f\x7e\x86\xd0\x3c\x4d\x5f\x1c\x3f\xab\xec\
\x4c\x06\x41\xcc\x80\xa0\x6c\xdb\x05\x34\x85\x3f\x47\x97\xed\x17\
\x28\x30\xd3\x01\x3c\x46\xd6\xb7\x8c\x14\xa1\x41\x17\x09\xce\x9b\
\x22\x72\xde\x80\x1f\x17\xef\x20\xde\x07\xa7\x02\xe0\x3d\xb4\x4e\
\x21\xd8\xe4\x04\x53\x6a\x54\xb2\x08\xa1\x83\xc1\x31\xb7\x5f\x53\
\xd5\x7b\xb9\x86\xf0\xaa\x10\x00\xac\x6d\x3e\x39\x11\x92\x25\xa8\
\xd3\xff\x9b\x9b\x94\x2f\x01\x78\x58\x55\xef\x8b\x08\x8e\x47\x2c\
\x28\x88\x09\xc4\x5b\x00\x3e\x67\xcc\xea\x60\x5f\x07\x91\xd9\xc6\
\xd6\x43\x5f\xa3\x1a\xd9\x97\x35\xf3\x8e\xa4\x99\xc6\x30\xd2\xd6\
\x38\x59\x28\xa8\xea\x38\xe7\x66\x2b\x36\x02\x9a\x07\x61\xe4\xa5\
\x2f\xcd\xbd\x1f\x0f\x13\x20\x0b\x2a\x3e\x94\x85\xae\x65\x83\xce\
\xba\xd7\x0a\x2e\xb1\xf0\xbb\x0f\x77\x65\x35\x02\x6b\xc0\x10\x18\
\xcc\x44\x5c\x0c\x06\x01\x33\x8a\xcc\xa1\xeb\xf8\x83\xce\x42\x69\
\x1d\xfd\x6a\x00\x6f\x67\xa8\x6a\x42\xbe\xde\x38\x63\x3d\x78\x07\
\x3e\xe7\x90\x37\xa2\x84\x06\x5d\x24\x38\xa0\xf3\x53\x99\x23\x75\
\x2d\xd9\xa7\x47\x45\x42\x39\x19\x66\x65\x5c\x53\x17\x58\x86\xf0\
\x5e\xf6\xac\x25\x06\xd3\x08\x1c\xc9\xd2\x5c\x12\x6a\x51\x1b\x4d\
\x60\xcc\x34\xff\x28\x80\x6d\x45\xe4\x76\xcf\x0a\x77\xe4\xd8\x27\
\x19\x90\x32\x54\x4b\xed\xff\xb5\x01\x5c\xee\x48\xb1\xe5\xc0\xb2\
\xd8\x49\xee\xf4\x4d\x43\x6e\x82\x63\x44\x49\x17\x90\x7b\x48\x81\
\xb9\x1b\x40\xbd\xcf\xaa\x36\x4a\x8e\xaa\xf2\x5b\xbd\xc8\x12\x8e\
\xba\xd6\x4e\x81\xb3\x5b\xd6\xfd\x2a\x4e\x60\xfa\xc9\xd0\xde\x4c\
\x44\x1e\x8e\xb9\x52\xb8\x0c\x6f\x17\x39\xd7\x69\xaf\x9a\x5a\x58\
\xb0\xed\x00\x9c\x61\x9b\xab\xf5\x94\x7b\xb8\x22\x2f\xc1\x31\x0a\
\x7a\xc9\xd1\xd1\xab\xe6\x72\x69\x01\xcc\xeb\xd1\xab\x12\x0b\xd5\
\x89\xc8\xf9\xf3\x68\x46\x0d\x23\xca\x00\xc0\x9a\x35\x74\xd4\xc1\
\x60\xf7\x0c\x73\xed\xf8\x20\x22\xf3\x11\xfe\xb8\xf8\xc6\xaa\x91\
\x2c\xcd\x9f\xa7\x9a\xb0\xd9\xfa\x69\x26\xd9\x15\x1b\x89\xc8\xd1\
\x5c\xb8\x57\x4b\xc9\x61\x2e\x16\x47\x05\x11\x7f\xfc\x7d\x4b\x00\
\xbe\xae\xaa\x9f\x35\x93\x7b\x7d\x4d\x31\xfc\x90\x97\x71\x60\x14\
\x79\x51\x7e\xc3\xaf\xe0\xec\xfc\xad\x46\x01\xc0\x58\x11\x99\xcb\
\x91\x76\x00\x9c\xaa\xe1\x03\x08\xbe\x46\x2e\x56\x68\xf1\xda\x92\
\xe1\x62\x87\x22\xf4\xc6\xbe\xde\xc4\x95\xd1\x3f\xff\x79\x9a\x83\
\xcd\x30\x60\x9c\xb1\x9c\xe3\xbe\xfd\x00\x00\x12\x05\x49\x44\x41\
\x54\x6a\x33\xe1\xd8\xd8\x73\x78\xef\x6b\x69\xc5\xbb\x53\x44\x5e\
\x61\x9d\x8d\xc6\x53\x71\x69\x14\x17\xab\x93\x73\x06\x5c\xc0\xac\
\x13\x0f\x70\xfd\xe7\x9d\x01\xcd\xbc\x7d\x81\xaa\xfe\x83\x39\x85\
\x46\x9c\x41\xc0\xa3\xd5\x82\x63\x23\xcf\x26\x34\x55\xc6\x60\x0b\
\xe0\x56\xcc\x7e\x76\xcf\xe5\x00\xfc\x4d\x55\x5f\xa4\xd9\xf4\x45\
\x46\x95\x79\x9e\x16\xa9\x57\x45\xe4\x55\x2c\xee\xb0\x36\x97\x99\
\x9f\x57\x73\x9d\xd9\xea\xb3\x9d\xaa\x2e\xcf\xc8\x95\x75\x77\x10\
\x0a\x4c\x85\xe4\xcf\x0f\x65\x6c\x44\x3e\x62\xcf\x54\xd5\xb2\x23\
\x68\xae\xc2\xfa\x2c\x4f\xab\xdf\xfb\x38\x6b\xad\x14\x71\x11\x80\
\xbb\xf7\x8f\x44\xe4\x56\xde\x63\x34\x80\x7e\x0b\x36\xe2\xce\x8b\
\x5a\xc0\x9c\x05\x71\xba\xaa\x7e\x81\x42\xe8\x69\x4c\xb6\xb1\x39\
\x09\xc0\xaf\x99\x5c\x78\xfe\x48\xce\x3c\x9d\xd7\x8c\x53\xac\x81\
\x99\xdc\x4a\x14\xb8\x88\x5d\x3b\xf2\x5b\x05\xc0\x4c\x55\xbd\x1f\
\xc0\x57\xe9\x10\x66\x71\x00\x6e\x21\x7b\xc0\x53\x4c\x2c\xeb\xd7\
\xd1\x22\x72\x82\x3b\xb7\x26\xf8\xb4\x85\xaa\x7a\x62\x06\x67\x0d\
\x7c\x36\xdc\xb9\xeb\x93\x09\xfd\x11\x32\x93\xeb\xc5\x44\x96\x55\
\x45\x64\x01\xcb\xb2\x2d\xe9\x3f\x4b\x02\xb8\x19\xc0\xcf\x9d\x51\
\x20\x5c\xef\xd8\x66\xef\x75\xcc\xca\x76\x66\xe0\xee\x60\xf5\x58\
\x1f\xc0\x76\x22\x72\xad\xe5\x35\x6d\xa0\xac\x1d\x8f\x3c\xad\x6a\
\x79\x78\xec\xc5\xd6\x23\x86\x90\x12\x52\x76\xfb\x1a\xcb\x93\x25\
\x70\x3d\x5d\xa7\xed\x65\x5f\x4d\x7e\x96\xf7\x18\x35\x6b\xd2\xd1\
\xaa\xba\x89\xc5\x3b\xab\xa3\x8c\xbd\xec\x84\xfb\xf3\x99\x15\x37\
\x93\x59\x47\x7c\x8e\xe9\x37\x84\x6b\xb3\x35\x28\x48\xdb\x38\xa1\
\x29\x47\xea\x93\x25\xc0\x4a\x06\x42\x09\xc0\x78\x55\x3d\x96\xfb\
\x47\xb7\x30\xed\xfc\x67\x98\xd9\xfa\x06\x55\x5d\xd5\xc5\x53\x5b\
\x74\x83\xc5\xd7\x81\x4b\x56\xa9\x5f\x85\xbe\x4f\x23\x1a\x79\x0a\
\x4e\x2b\x3d\xf6\xac\x53\xcf\x72\xc2\x13\x0a\x66\x21\x42\x48\xf4\
\x3e\x28\x7d\xe4\x6f\xed\xc6\x51\xb7\x57\x44\x1e\xa7\x7f\x8d\xe7\
\x58\x59\xb9\xc7\x00\xf8\x9d\xaa\x7e\xd0\x38\x65\xb6\x47\x34\xa0\
\x70\x8b\x62\x47\x5b\xa0\x8f\x1d\xe9\xa2\x1d\x73\x50\x13\x00\xbf\
\x14\x91\x79\x8e\xa1\xfd\x65\xce\x72\x0b\x02\xb5\x31\xac\x4f\x21\
\xb8\x97\x9f\x29\x5f\xa1\x43\xdf\xad\x9c\xb9\x26\x3b\x76\xb3\x09\
\xe0\x0e\x14\x58\x63\x67\x17\x9c\x15\xb4\xc0\xef\xce\x62\xa2\xad\
\x90\x7d\xe0\x07\x96\xfb\x82\xef\x46\x1c\x72\xb3\xaa\xb9\x91\x31\
\xfc\x34\xa3\x71\xcd\x62\x76\x15\xe9\x34\xa3\x5c\x07\x2f\x0f\xc2\
\x28\x86\x5b\xe0\x2a\x09\x8d\x1e\xa7\x47\x76\xcf\xcd\xb0\xb1\x2a\
\x80\xbf\xa8\xea\xae\xc1\xc6\x64\xc1\x6d\x04\x8a\xb3\x22\x96\x55\
\xf5\x30\x96\x73\x6c\x30\x78\x54\x9c\xd5\xeb\x27\xac\x4f\x1f\x69\
\x35\x7b\xf1\xd9\xbd\x91\xc1\xa6\x12\x99\x4d\x7d\x84\x9d\x1e\x3a\
\xd6\xdd\x43\xb7\x80\x0d\x28\x80\x15\x57\xef\xa2\xb3\x96\xad\x06\
\xe0\x46\x55\x3d\xc6\xed\xc3\x98\x17\xec\xf7\xc9\xdc\x2e\x47\xfa\
\x8e\x99\xa2\x4f\x63\x66\xb6\x11\x6d\x1c\xc8\x4b\x70\x5a\x1a\x95\
\x84\x2f\x57\x44\xe4\x05\xaa\x3f\xf7\x72\xb7\x1b\xae\x53\xc4\x18\
\xc5\x1e\xd6\x16\xdb\xa8\xea\x86\x2e\xe4\xec\x03\x00\x7e\x9a\xb1\
\x16\xa9\x70\x87\xff\x6a\x55\xbd\x42\x55\xb7\x51\xd5\xb1\xce\xbd\
\xc0\xdc\x09\x26\xa8\xea\x6e\xaa\x7a\x0b\xf9\x67\x63\x22\x1b\xab\
\xd6\x91\xbf\x29\x22\xaf\x51\xa5\x53\xaa\x51\xab\x57\x49\x5b\x51\
\x88\xcc\xa6\x76\xde\x3c\x2e\xe4\xf7\xe4\xbd\xb6\x74\xb1\x12\x62\
\xf7\x2a\x3a\xd5\xf1\x2c\x55\xbd\x54\x55\x27\x70\xa6\xf9\x01\xfd\
\x77\xc2\xd8\x07\x70\x9e\xb1\xdf\x17\x91\x93\xb8\xb6\x19\xb1\xb3\
\x0d\x72\x30\x0e\xd8\xcb\x7e\x02\xc0\xd9\x01\x85\xde\x54\xaa\x13\
\x03\x93\x6f\x43\xb0\x70\xb5\x22\x72\x0f\x80\x4d\x55\xd5\xbb\xf4\
\xae\x42\xcb\xd3\x9a\xfc\x7b\x02\x9f\x19\x46\x8c\xb1\x91\x74\x3b\
\xba\x0d\x98\x99\xfa\x1b\x74\xc5\x5e\xcf\x75\x12\x04\x34\x94\xcf\
\xf2\xf3\xac\xaa\xfe\xdd\x31\x02\x56\xe4\x75\x16\x61\xb2\x12\x51\
\x53\xfb\x39\x9b\xfc\x0f\x03\x0a\x7a\x21\xdd\xb1\x4a\x27\xec\xa7\
\x65\xf0\x2d\x1e\x8d\x58\xf9\x22\x89\x96\x2f\x98\xe9\xd9\x95\x25\
\x0c\x52\x82\xa0\xed\x0b\x4e\x85\xfb\x3c\xf7\xac\xa6\x31\x68\x48\
\x18\xd3\x0d\x81\xd0\x7c\xdd\x2c\x86\x23\xd5\x9a\x66\x68\xb5\xe0\
\x58\xe3\x3d\x27\x22\xe7\x47\x4f\x50\x3d\xb0\x19\x82\x83\x45\x7b\
\x0e\x05\x8e\xf8\xcf\xb3\x33\xc5\x9e\x79\x10\x37\x01\x63\x7a\xba\
\x70\xa4\x86\x75\x30\x11\x99\xc7\xb4\xed\xb7\x73\x86\xf1\xc2\x63\
\x65\x36\xa1\xb3\x38\x07\x21\x4c\x45\x0c\x47\x6b\x13\x9a\x07\x00\
\x1c\xe8\x7c\x56\xac\x5c\x6f\x47\x8c\x1e\xf6\x77\x1f\x80\x03\x44\
\xe4\xee\xac\x36\x71\x84\xcd\x71\x2e\x18\xfb\x80\xa6\x8b\xb8\x4e\
\x98\xf0\x6e\xca\x4f\xa5\xca\x4c\x73\x56\x37\x09\x0d\x72\x54\xd5\
\x46\x51\xdf\x1f\xed\x74\xff\x51\xb4\xdc\x34\x75\x03\xd4\x66\x9e\
\x48\xd6\x80\x5e\x7e\xff\x01\x9a\x52\xc3\x51\xdf\x3a\xc6\x2c\x00\
\x57\x5a\x07\x76\xe6\xd9\x27\x18\x67\xfa\xf9\x20\x7d\x85\xa1\xe8\
\x3a\x60\x68\xed\x52\xa7\x4e\xf9\xe7\x99\x77\xe6\x7d\xcc\x54\xf0\
\x16\x30\x20\xa0\xe0\xcf\xdd\x2c\xe5\x17\xfb\x4a\x3e\xdb\x8f\x99\
\xe6\xbd\x27\xf8\x2c\x64\x44\xf0\x7e\x2b\x38\x6b\x58\x38\x40\xbd\
\xe1\x66\x9a\xb0\x4e\x95\x8c\x35\x8d\x17\x9a\xe3\xba\x49\x68\x90\
\x33\xe5\xa6\x64\x51\xe6\xfd\xdf\xad\xd0\x85\x8d\xfc\x68\x6e\xcb\
\xee\xe5\x8f\x61\x14\x94\x65\x03\x8b\x96\xba\xff\xbf\xc4\xe0\xea\
\x16\xd7\xcc\x73\xb6\x1e\x61\xb0\x8a\xdb\xdc\xfa\x2c\x4c\x10\x15\
\xb3\xde\x85\xcf\x29\xb9\xf3\x2e\x21\xc9\x72\x26\x67\xcb\xf0\x99\
\x7f\xa5\xcf\x4e\x56\x8c\x82\x8f\x02\x38\xdf\xb9\x37\x18\xc9\xd2\
\x3a\xb1\x3d\x7b\x39\x0a\x9a\xff\xce\xca\x7d\x30\x80\x33\x02\x83\
\x4a\x58\x1f\x0f\x13\x9a\x1f\x50\x68\x7a\x46\xa8\xd0\x64\xd6\x27\
\x37\xe3\x80\x05\x52\x30\xae\x95\xfd\x9d\xd3\xf3\xcd\xc2\xf3\x53\
\x76\xb4\x58\xe0\x8d\x1e\x00\xa7\x8a\xc8\x55\x31\xaf\x4e\xd7\x91\
\x9f\xe3\xa6\xe8\xf1\x8c\xcf\xe6\x17\xda\xa1\xf5\x2e\x8c\x6b\x60\
\x4e\x71\x3d\xf4\xee\xdc\x57\x44\xf6\xb7\x30\x4c\x11\x2b\x94\xcd\
\x76\x67\x00\xf8\x9f\x2a\x3c\xb1\xbd\x54\xf5\x1b\x14\x1e\x1f\xc0\
\xc2\xb7\xf3\xca\x76\x4f\x5f\x2d\x1e\x1f\x17\x91\x13\x99\x6f\xf4\
\x6d\x77\xdf\x18\x4c\x68\xce\x16\x91\x63\x6d\x3d\x36\x0c\x84\x26\
\xec\x83\xbd\x3c\x2e\xed\xf6\xc6\xc2\x99\xd8\x54\xf6\x01\x75\xcb\
\xab\xe3\xda\x08\xd8\xef\x82\x58\x94\x02\xbf\x8f\x96\xc0\x05\x2d\
\x3f\x8a\xc9\x94\xb2\x22\xfd\xdf\x20\x22\x27\x57\xdb\xed\x76\x8e\
\x6e\x65\x11\xf9\x2e\x17\xfd\xdf\x76\xf9\x68\x42\xeb\x5d\x18\xd7\
\x40\xb9\x96\x39\x12\xc0\x86\xcc\xf0\x9c\xe9\xb3\xc2\xce\x68\x24\
\xcb\x83\x19\x6a\xaa\x18\xb4\x99\x95\xf7\x3b\xaa\xba\x43\xd0\xc6\
\x0b\xdb\xdc\x39\xe5\x2d\x6c\x1a\x17\x44\xe3\x0d\xd6\xeb\x17\xcc\
\x9c\xf6\x58\x44\x1d\xd5\x60\xa6\x39\x66\x98\xa9\x67\xd6\x07\xfb\
\x82\x76\x39\xd6\x71\xef\x42\x37\xf0\xa7\x78\x1c\x50\xbf\x56\x1b\
\x07\xac\x00\x13\x55\x75\xdd\x0c\xab\xda\x12\xad\x7a\xb8\x8b\xc2\
\xb9\x35\x5d\x87\x43\xda\xbb\x99\x66\x9f\x05\xb0\xbf\xc5\x1b\x88\
\x75\x04\x1f\xc9\x92\x1d\xb9\x97\x2a\xdd\x29\x8c\x1d\xb0\x31\xdd\
\x9d\xd7\xa5\x25\x6f\x22\xeb\x37\x87\x96\xae\x69\x00\xee\x04\xf0\
\xbf\x2e\x70\xe2\x28\x72\xc6\x34\xab\x13\x3a\x83\xc7\x1b\x4c\xa1\
\x71\x07\xf7\x80\x3c\x4f\xcc\x66\xb2\x4b\x68\xc4\x98\xed\x6e\x61\
\x82\xb5\x51\x58\x25\x5e\xf7\x2a\xd3\x53\xda\xa6\xef\x83\x0c\xe8\
\x71\x3e\x80\x3d\x7d\x51\x9c\xd0\x1c\x3b\x8c\x84\xc6\xfa\xe0\x52\
\xec\x83\x36\xf0\x2c\xcd\x80\x29\x07\xb9\x35\x28\xdc\xdf\x0b\x5c\
\x62\xad\xc1\xeb\x68\xf4\x11\x55\x3d\x27\x23\xe3\xef\x13\x91\x6b\
\x2c\x4b\xf0\x55\xc1\x35\x8d\xa0\x29\x59\xa7\x5d\x8c\xe3\xa5\x54\
\xf5\xd9\xa0\x0e\xea\xb2\x25\x2f\x50\xd5\x4d\xb1\x88\x7c\x19\xbb\
\x57\xe6\xcc\x4c\xc2\x64\x3d\xe5\x2a\x54\xbb\x26\xeb\x59\xae\x8d\
\xbf\x18\xa9\x8b\x46\x32\x51\x0f\x06\xcb\xca\x7c\xa7\x7f\x6e\x10\
\xf8\xfd\x78\x55\x7d\x95\xcf\x9a\xa9\xaa\x27\xd8\x39\xad\xf4\xa5\
\xaa\x21\xeb\xf4\xdf\xc2\xb6\x72\x59\xb2\x6f\x0b\xea\x37\x18\xc2\
\x76\xb3\x67\xdd\x60\x46\xa6\x58\x19\xf3\x8c\x39\x90\x25\xb5\xad\
\x7a\x01\x36\x3b\xec\xc0\x0d\xc4\x70\xb6\xb1\x91\xe5\x08\x11\xb9\
\x87\xa3\xed\x00\x97\x03\x8b\x2b\xa0\xaa\x13\x19\xf0\x63\x5b\x8e\
\xe8\x97\x03\xf8\xa3\x59\xc2\x9c\x80\x6b\x64\x1d\xb1\xd0\x82\xc7\
\x75\xc8\x02\xb2\xab\xf7\x65\x68\xdc\x22\xd7\x30\xe7\x0c\x42\xb2\
\x1c\x25\x22\x17\x93\xf0\x79\x78\x50\xa7\x6a\x3c\x3d\x5f\x96\x10\
\xcf\xfb\xdf\x2c\xc6\x01\xff\x3e\x53\x55\x7f\xce\xf6\x7b\x9e\x31\
\x12\xb2\x12\x04\x0f\x07\x84\x26\xfd\x70\x7b\xc0\xff\x7e\x9a\x73\
\xe7\x18\x80\x3c\x05\x27\x4f\x6f\x4f\x8f\x09\x83\x74\xa8\xc9\xaa\
\xfa\x0b\xd2\x76\x7c\x7c\x65\xcf\xcf\xfa\x18\x53\x08\xae\xe7\xae\
\xdb\x11\xc0\xb7\x55\xf5\x5a\xa6\x42\x7c\x31\x2b\xb8\xb9\xdd\x8f\
\x2f\xe2\x63\x0c\x70\xb1\x23\x03\x82\x18\x36\x07\xb0\xbd\xaa\x1e\
\x24\x22\xaf\x84\x81\x40\x1c\xcf\x6d\x19\xba\x22\xc4\xf6\xbd\xea\
\x69\x63\xeb\x38\xd3\xc3\x1f\x9c\x2a\x59\x14\x11\xcb\xba\x96\x99\
\x6a\x71\x18\x21\xdc\xf0\xf6\xb0\x35\x5c\x2f\xbd\x59\xef\xae\x56\
\xdf\x91\x1c\x73\xc0\x3a\xf0\x1d\xce\x8a\x16\x92\x3e\x2b\x0c\x99\
\xfb\x2b\xeb\x48\xce\x1f\x47\x39\xfa\xee\xc7\x10\xb4\xeb\x39\xd3\
\xb3\x59\xca\xde\xcb\xb8\xce\xb7\xab\xea\x4a\xc8\x50\xb5\x9c\x1a\
\x34\x99\xe5\xd9\x97\x42\x53\x0e\xac\x6e\x3b\x01\xb8\x5b\x55\x3f\
\x6e\x9e\x94\x46\x10\x65\x59\x96\x61\xce\xd0\xad\x03\xbd\xbc\xd1\
\xf6\x11\xfa\x25\x21\x26\x74\x36\xfb\xc4\xb2\x60\x77\x30\xde\xce\
\xe0\x23\xc6\xe0\xb7\x07\x84\x42\x73\x91\x88\x9c\xe8\x7c\xa6\xa2\
\xc8\x93\xe4\x59\xce\xf8\xb4\x64\x71\x19\x6c\x5c\x7e\xd5\x6d\x4e\
\x86\xc2\x53\x62\x7a\xc1\x4b\xcd\x12\x66\x0b\x65\x55\xfd\x21\xc3\
\xcf\x4e\x0c\x38\x5e\x45\xb7\xc8\x5c\x40\x2a\xcf\x61\x1c\xa9\xa3\
\x6d\xca\xdf\xbe\xc9\xb0\xb3\x0b\x9c\x9a\x10\x92\x2c\xd7\x00\x70\
\xb3\xaa\x1e\xee\x02\x67\x94\x55\x75\x29\x0a\xcd\xe4\x88\x39\xbd\
\x5a\xfb\xc6\x3e\x36\xb2\xce\x73\x7e\x3f\xd1\x4e\xe2\xf6\xc4\xaa\
\xbe\x27\xc7\x0e\x1f\xf2\x87\xce\x7b\x8d\xe6\xdb\xf9\x83\x33\xf9\
\x97\xaa\xb4\x41\x05\x8b\x6f\x0f\xcc\x05\xf0\x75\x11\xf9\x92\x65\
\x73\xa8\x56\xe7\xbc\x54\x35\x89\x6c\xa2\xb5\xfe\xa1\x8b\xf6\x5e\
\xce\xa3\xd1\xe3\x87\x81\x55\x0f\xae\x81\xf7\x21\x51\x74\x1f\x7a\
\x59\xfe\x9a\x23\x7b\x2c\x16\x99\xc1\x1a\xbd\xc2\xe4\x4f\x08\x3b\
\xa0\x99\x9a\x55\x75\x0c\xdd\x16\xb2\x58\xce\x70\xc2\xd8\x0b\x60\
\x8a\xaa\x6e\x08\xe0\x10\x06\x3d\xbf\xc1\x09\x8d\x7f\x6f\xda\x60\
\xfb\xbe\xc8\xf5\xdd\xf3\x43\x65\x32\xb7\x60\x36\x2a\xf3\xbe\x0b\
\xea\xb8\xc6\x82\x3c\xfe\x12\xc0\x87\x01\x1c\x16\x86\xd7\x8a\xc0\
\xb8\x7e\xd7\x31\x1f\xeb\xe3\xd5\x2c\xab\x1e\x79\x91\x3c\xa7\x91\
\x28\x19\x33\x47\x4f\x61\x4e\xcc\x21\x73\xd5\x62\x70\x21\x67\xcf\
\x61\x88\x80\x1f\x3a\x61\xf0\xc2\x53\x06\xb0\x37\x8d\x00\x1f\x60\
\x99\xc2\x4e\x8a\x48\x39\x6d\xd4\x5a\x85\xcf\xcb\xea\x80\x13\x49\
\x7b\x89\xd5\xd1\xf3\xc4\x3c\xc9\xf2\x00\x7a\xad\x0a\x85\x26\x24\
\x59\xda\x75\xef\xd0\x58\xf0\x72\x8d\x46\x82\x7e\x9a\xc5\x07\x4b\
\xeb\x3e\x28\xec\x7a\xa6\x30\xd9\x87\xf5\x1c\xea\x7b\xb4\x3a\x7c\
\x98\xff\x0f\x3a\x28\x04\x1d\xfd\x6b\xaa\xfa\x33\x6a\x02\x59\xe8\
\x67\x4c\x89\x27\x9c\x47\x6c\xcd\x6b\xb8\xbc\x48\x9e\xaf\x89\xc8\
\x8d\xd1\x13\x54\xe7\xb8\x73\x5b\x65\x40\xa8\x45\x78\x6c\xb4\xdf\
\xd9\xae\x89\x8c\xec\x31\x55\x6c\x21\xa5\x85\x14\xfc\xb9\x81\x91\
\xc0\x3a\xc1\x0a\xec\x54\x31\x18\x7d\xc6\x5b\xc8\x6c\xff\x65\x33\
\x7e\x17\x92\x2c\xbd\xd0\xec\x91\xd5\xbe\xd5\xd0\x44\xa1\x39\x9c\
\x03\x60\xab\x50\x57\xbf\x60\xb9\x9e\x20\x2b\xbf\x96\xf3\x8b\x08\
\xb2\x6a\x0f\x86\xbc\x54\xb5\x5e\xd3\x5d\x23\x51\x6e\x5a\x5e\x06\
\x5a\xb3\x6a\x11\x1e\xeb\xc0\xa1\xea\xe3\x23\xba\x3c\x9f\x11\x14\
\x63\x49\x0a\xc7\xdc\x08\x21\x13\xee\x9a\x90\x91\xdd\x07\x60\x46\
\x10\x14\x24\x14\x66\x04\xd7\x78\xa1\xf9\xb4\x88\xdc\xc4\xcd\xd4\
\x7a\xd4\xa5\x21\xa5\xc5\x70\xc9\x7d\x97\x03\x70\x9a\xb3\x4a\x35\
\x73\xdd\x9c\xe5\x3b\x55\x15\x16\x62\xb8\x86\x6b\xb5\x5e\x81\x31\
\xe4\x25\x38\x66\xa1\x5a\x98\x0e\x43\xdf\x1d\x96\x2b\x3a\xb4\x10\
\x4b\x35\xa3\x8a\xf0\x84\x6b\x9e\x50\x2d\xf0\x33\xc1\x51\xa4\xbd\
\xdc\x18\x08\x93\x72\x37\x7f\x79\x00\x4f\x66\x98\x3d\x57\xe5\xd1\
\x53\x58\x8c\x24\xba\x23\xfd\x5d\x8e\xe6\x6f\xa1\xea\xe6\xe1\x85\
\x66\x4f\x0a\x4d\x8f\x25\x07\xce\x11\xb6\x4f\xb6\x3f\xa3\xdb\x94\
\x72\x0a\xf5\x15\x32\xb8\xa3\x68\xb5\xf7\xe9\x48\x36\x47\x0f\x80\
\x05\x45\x34\xe1\xa1\xb5\xad\x50\xc5\x7c\x69\xde\x8e\x33\x00\xec\
\x22\x22\xe7\x72\x51\x1d\xaa\x6c\xf6\x92\x56\xf5\x56\xa1\xc0\x42\
\x64\x33\x4e\xf8\x9c\x79\x00\x9e\x15\x91\xaf\x32\x70\xc6\xdb\x6e\
\xe6\x0b\x61\x42\x33\x9f\xea\xd9\x0d\x8d\x06\x7e\x1f\x0a\xcc\xe5\
\x82\x06\x8f\x43\x33\x54\xd8\x7a\xac\x7c\xb5\x7e\xfa\x39\xd8\xfc\
\x83\xcf\x68\xd7\xde\x60\x77\x09\x8e\x21\x22\x3c\xa6\x12\x99\x00\
\x55\xdc\x1a\xe7\x2e\x86\x89\xbd\x8e\x02\x30\x9b\xfc\x33\x44\x84\
\x60\x45\x12\x40\xfb\x5c\x0c\x82\x05\x9c\x65\x57\x0e\xce\x35\x61\
\x7b\x81\xb1\x05\x2c\xd4\xec\xd6\x8e\xcc\x59\x72\x65\x2a\x3b\xa1\
\xd9\x53\x44\x6e\x6c\x87\xd0\x10\x16\x39\xf4\xd3\x34\xa2\xc4\xdc\
\xba\x8b\x2d\xf8\x8c\x26\xb7\xee\x8c\x20\x8f\x51\xee\x18\xe9\x69\
\x3e\x32\xe1\x85\xc7\xa9\x6d\x0b\x7f\xe6\xf1\x3c\x00\xc7\x30\x8a\
\xa5\x51\x6f\x5e\xe7\xcb\x5b\x3a\x62\xd0\xf8\x84\xaa\xfe\x33\x92\
\xa2\x50\xe9\xce\x80\x48\x07\x7b\xc1\x74\x72\x3e\xe3\x7e\x06\xf4\
\xbb\x08\xc0\x6e\xee\xbc\x22\xd7\x43\x9f\x11\x91\x3f\x65\x51\x84\
\x72\x82\xad\x21\x8e\xa8\x72\xce\xed\x54\x27\x9b\xd5\xc1\x95\xac\
\xed\xf3\x44\xe4\x99\x8e\xcb\x82\xd0\x64\x92\xa7\x11\xed\x6e\xc3\
\x40\x02\xa1\xed\xa6\xff\x2d\xb8\x7f\x53\x48\x9e\x75\xd4\xd7\xca\
\xbe\x9f\xaa\x3e\xa6\xaa\xb3\x55\xf5\xef\xaa\xba\xaf\x3b\xa7\x10\
\x1c\xa7\xd6\x49\x24\x8c\xc1\xea\x79\x6e\x50\x0e\xdf\x46\x27\x90\
\xa0\x3a\x5b\x55\xef\x65\x46\xb5\x96\xb7\x49\x35\x38\x36\xc3\x56\
\x11\x92\x64\x89\xff\xdf\x57\xc3\xad\x86\x52\x86\xb6\xa9\x68\x86\
\xae\x9d\x71\x0c\x16\x3f\x4c\x44\x2e\x61\xaa\xc0\x15\x00\xbc\x62\
\xdf\x63\xf1\x78\xcd\xf6\xc2\xb2\xc2\xf9\x56\xa3\x7a\x84\x56\x9e\
\xe8\xbd\x7c\x22\x29\x11\x39\x83\x82\xb5\x94\x88\xbc\x88\x45\xa6\
\xd6\x76\xa8\x67\x06\xa5\xa1\xe5\x48\xfe\xef\xcd\xe4\x46\x66\xfd\
\x31\x3b\xf7\xa8\x2a\x0e\x71\x43\x79\x7e\xdb\x67\x9a\xae\x17\x1c\
\x2c\x4e\xcf\xe9\xe7\x9a\x63\xb0\xcd\xb0\xe9\x19\xd6\x9d\x7a\xd6\
\x8c\xa6\xc2\x3c\xcb\xff\x17\xde\x2b\x20\x59\x5a\xd6\xb5\xb6\x93\
\x2c\x1d\x67\xee\x3f\xb8\xdf\xe5\x8d\x02\x46\x61\x99\x0e\xe0\x8f\
\xfc\xae\x6f\x18\xf8\xeb\x34\x84\xae\x34\x0e\xc4\x50\x23\xa1\xd1\
\x7b\x06\x0a\x02\x7a\x4d\x1d\xf0\x31\x0e\x32\xbd\x0c\x7d\x99\xec\
\xff\x06\x9f\xd7\x6c\x1c\xc6\x85\x7a\x18\xb7\x41\x00\x5c\x48\x61\
\x2f\x8e\x54\xa1\x41\x9a\x71\x16\x47\x0d\xf9\x7a\x8c\x0f\x75\x33\
\x0d\x04\xcb\x47\xc2\xd8\xd6\x8a\x1e\x00\x77\x03\x78\x2c\xc8\xb9\
\x59\x6f\x99\x72\x81\x33\x41\x2f\xef\xa2\x9d\x7a\xa1\x29\x32\x5a\
\xce\xc5\x23\x29\x2d\x7b\x16\xd2\x8c\x53\x07\xa8\x5b\x0b\x53\x82\
\xec\xc1\xec\xd3\xd2\xc0\xa7\x1f\xc0\x4d\x00\x3e\x6f\x1b\x97\xc3\
\x60\x74\xb6\x19\x64\x7f\x5a\x14\x7d\xc8\x28\x9b\x09\x7f\x23\x22\
\x33\x5c\x70\x94\x11\x8b\x34\xe3\xd4\x09\x17\x31\xf4\xaf\xf4\xaf\
\x59\xcb\x05\xe2\xa8\x85\xe2\x21\x00\xe6\x8b\xc8\x53\x70\xec\xe9\
\x7c\x4a\xdf\x18\x5c\xd6\x84\xb1\x0c\x00\x8f\xa0\xae\x66\x2a\xff\
\x89\x5d\xd2\x86\x62\xe6\x8a\x61\x29\x38\x55\xcc\xb1\x99\xfc\xab\
\x46\xae\xc9\x82\x0b\xa0\x51\x72\x11\x6e\xea\x82\xcb\x93\xd3\xd1\
\x42\x43\x58\xa4\xa0\xdd\xc9\x38\xf6\x34\x24\xfb\xfb\x86\x6e\xc8\
\xc4\x66\x18\x96\x82\xd3\x88\x39\xb6\xd9\x26\x5c\x9b\x79\x1a\xa5\
\x7d\xb0\x73\x0d\x97\x91\xd9\x22\xfb\x1c\x19\x29\xb3\xd5\x7f\x4a\
\xf0\xff\x88\xc6\xb0\x11\x1c\xe7\xb3\xdf\xc3\x50\x4f\x4b\x3a\xd5\
\xc7\x46\xbd\xab\x18\x50\xb0\xe8\xf7\x43\x54\x75\x49\x5e\xd3\x13\
\xb9\xe6\x22\x11\xb9\xab\x11\x53\x6f\xa7\x2c\xdc\x5b\x09\xd7\x96\
\x5b\x31\x25\x65\x25\x32\xdb\xdc\x0f\x60\xea\x30\x72\xaf\x1e\x32\
\x86\x8d\xe0\x38\x14\x48\x86\x8c\xa5\x46\x7c\x95\xb9\x67\xbc\x7b\
\x80\xd2\x5d\xf9\xa0\x8c\xfb\xfd\x95\x7c\xb4\xae\x18\x29\x1b\x80\
\x0d\x0c\x47\x04\xff\x7b\x4c\x31\x6f\xdb\x3a\x5d\x1b\x86\x2d\x86\
\xab\x55\x6d\x16\x77\xa4\xfb\x78\x7c\x87\xc7\x7f\x67\x9c\x5f\x21\
\xeb\xb8\x44\x8b\x56\x89\x64\x49\xbb\x36\x21\x02\xe7\xa8\xf6\x41\
\xe6\x1d\x0a\x37\x3c\x0b\xb6\xe1\xd9\x0d\x26\x68\x8f\xe1\x38\xe3\
\xc0\x05\x34\xb7\x97\xa7\x55\x92\x25\x85\xd7\x78\xeb\xd7\x60\xd7\
\x74\x3b\xac\x9d\xbe\x42\x5f\x1b\xef\x4a\x6e\x42\x74\xa1\x88\xbc\
\xdd\x46\xa6\x76\x5b\x30\x5c\x05\xa7\xe2\x3e\x08\x5c\x02\x06\xbb\
\xc6\x04\xa7\x96\x6b\xba\x16\x16\xe9\x85\x1b\x9e\xfb\xb8\x4d\x4e\
\x38\xa1\x79\x03\xc0\xc5\xfc\xae\x6b\x66\x1b\x0c\x63\xc1\x19\x1f\
\x44\x9e\x19\x1d\x1c\x43\x48\x24\xe2\xc9\x28\x1e\xf3\xf0\x5a\x1c\
\x8e\xb0\x60\x8c\x07\xb8\x0d\x4f\x6f\x14\xe8\xb1\x0d\xcf\x76\x73\
\xe8\xda\x81\x46\x04\xa7\xdd\x23\xb4\x32\x11\xd3\x7b\x9c\xaa\x66\
\x2a\xc4\x73\xee\x1c\x8f\x3e\x5e\xd3\x1b\xb8\x2c\xf7\xd0\xa0\x10\
\xbb\xa6\x6b\x11\x6c\x78\x1e\xca\xaf\x43\x7a\x4d\x9f\x4b\xf2\xdb\
\x75\x88\x09\x8e\x75\xa0\xac\x45\xf3\x44\x55\x1d\xc7\xa0\x7a\x30\
\xae\x56\xab\x1b\xd0\x25\x5c\xea\x67\x66\xb4\x6a\xe7\x96\xe0\xfc\
\xce\x19\xc6\x75\x93\x41\xae\xe9\xaa\x11\x73\x10\xd8\x86\xe7\x1e\
\x91\x0d\xcf\x4a\x64\xc3\xb3\xeb\xda\xae\xda\xc2\x78\xb1\x60\xdc\
\x41\x96\xe5\xfd\x7c\x7a\x72\xe6\x1e\xc9\x6d\x4f\xc3\xb1\x98\xc3\
\x4f\xa6\xf0\x66\x9c\x5f\xf5\x9a\x2e\x86\x05\x5e\x3f\xbc\x8a\xeb\
\xc4\xb9\x3c\x76\x65\xfb\xc5\x66\x1c\x5b\xe4\xdd\x1b\xf1\x25\xb7\
\x7d\x91\x73\x38\x8d\xff\x9e\x89\x89\x0a\xaa\x1a\x0b\xde\x37\x14\
\x68\x56\xa7\x6e\x44\x48\xbb\x81\x06\xd2\x0c\xb8\x98\xc9\x9f\x48\
\x1b\x9e\xd9\x18\x30\xe3\x38\x2a\xc9\xdf\xc9\xfe\x45\xe0\x3f\x6f\
\x0b\xed\x1f\xd2\x07\x7c\x3a\x80\xa7\xb9\xbe\xd8\x81\xe7\xd5\x23\
\x40\x16\xd6\x28\x14\x84\x25\x82\x1c\x96\x09\xf9\xc0\x82\x29\x7a\
\x0f\xcf\x10\x53\x38\x10\xe5\x1e\xd6\xb8\x53\x90\xd5\xc1\xcd\xa2\
\x72\x26\x83\x58\xc7\x52\x57\x54\x98\x42\x63\xc2\x10\xcb\x30\x23\
\xf8\xdf\x5e\xc6\xc7\x55\x75\x59\x11\x99\x45\x9a\x4d\x5a\xbc\xb7\
\x1e\xc2\xf7\xfe\x51\xe7\xe1\xe9\xd7\x36\xb6\xe1\x69\x59\xb9\xbb\
\x72\xb6\xa9\x0a\x97\xe1\xea\x0a\x06\x62\xe8\x8b\x04\x9c\xa8\x04\
\x9f\x10\xd5\x82\x75\x58\x70\x8a\x6f\x06\xc1\x2b\xd4\x05\xee\xb8\
\x55\x55\xd7\x6e\x63\x33\x74\x1d\x54\x75\x23\x55\xfd\x67\xf0\x1e\
\xfc\xfb\x39\x1e\x6d\x0e\x18\xd2\x09\xa8\xb6\x98\xb6\xdf\xc6\x33\
\x9a\xfb\xc7\x83\xf0\xb5\xb5\xa8\x50\xc6\x17\xbb\x55\x44\x76\xf0\
\xf6\x7e\x47\xe7\x58\x0f\xc0\xc3\xae\x3c\xa1\x2b\xee\x3c\x00\x8f\
\x90\x2a\x93\xd0\x5a\x8c\x05\xb0\x41\x84\x61\x61\x6b\xca\xb9\x00\
\xfe\x83\x26\xfc\xe1\xe2\x12\xd1\x12\x64\x8e\x1a\x64\x15\x0b\x83\
\x88\x7f\x0a\xc0\x8f\xe9\xfd\x67\xa8\x75\xe7\xbd\x17\xc0\xad\x76\
\x5b\x77\xff\x0a\x85\x67\x1a\xb3\x9a\xed\x16\x50\x3a\x6c\x77\x7f\
\x3c\xb3\x95\x25\xe4\x87\xd0\x28\x64\x1b\x9e\x3f\xed\xd6\x0d\xcf\
\x10\x83\xce\x1a\x3e\xf2\xbe\xaa\xee\xc2\xf8\xc9\x5b\xba\x9d\xf7\
\xc1\xf0\x27\x00\x9f\xb1\x7d\x21\xef\x22\xec\x7c\xed\xd7\xa2\x21\
\x62\x7c\x46\xae\xce\xae\x1d\xd9\xda\x80\x50\x9b\xb0\xc1\xec\x29\
\x66\xd6\x7e\x13\x35\xe4\x8f\x19\xe9\xa8\xc9\x62\x15\x7a\x2b\xaa\
\xea\x5a\x4c\xa4\xb4\xca\x20\x02\xf4\x4f\x11\xb9\x16\x81\x00\x06\
\xf7\x36\x95\x6d\x0f\x1a\x22\xc4\xc5\x6c\x4e\x16\xb5\xf6\x41\xdd\
\x4c\x33\x07\xc0\x0e\x4c\xe5\xde\x15\x1e\x9e\x83\xa1\xde\xbc\x23\
\x0d\xe5\xb6\xcf\x12\x1a\x7f\x5f\xfa\x73\xec\xc6\xd0\xaf\xcb\xf2\
\x27\x53\x07\xba\x7a\x74\xcb\x19\x61\xd6\x86\x27\x00\xec\x2f\x22\
\xf7\x25\x15\x6d\x11\x1a\x1a\xd1\x5d\xee\x91\xc1\x5c\x87\x2b\xb5\
\x0a\x9a\x13\x9e\x35\x01\x9c\xcc\x28\x32\x43\x35\x75\x27\x34\x8e\
\x59\x4c\x0b\x78\x26\x33\xb7\x25\xa1\x71\xe8\x28\x55\x28\xb0\xba\
\xad\x49\x4b\xde\x86\xa4\xf9\x74\xb5\xf9\x33\x27\xbc\x03\xe0\x25\
\x00\x0f\x00\x98\xca\x30\x58\x43\xce\xdc\x96\x90\x03\xc8\x1f\xeb\
\xda\x1d\xe9\x4e\x82\x05\x58\x6f\x77\x39\x3a\x11\x1d\xdb\x28\x81\
\x3a\x98\x90\x2f\xb4\x91\xb5\x6c\x42\x42\x42\x42\x42\x42\x42\x42\
\x42\x42\x42\x42\x42\x42\x42\x42\x42\x42\x42\x42\x42\x42\x42\x42\
\x42\x42\x42\x42\x42\x42\x42\x42\x42\x42\x42\x42\x42\x42\x42\x42\
\x42\x42\x42\x42\x42\x42\x42\x42\x42\x42\x42\x42\x42\x42\x42\x93\
\xf0\x7f\x6f\x9a\x12\x32\x24\x6e\xb2\x4a\x00\x00\x00\x00\x49\x45\
\x4e\x44\xae\x42\x60\x82\
\x00\x00\x21\xd5\
\x89\
\x50\x4e\x47\x0d\x0a\x1a\x0a\x00\x00\x00\x0d\x49\x48\x44\x52\x00\
\x00\x00\xca\x00\x00\x00\xce\x08\x06\x00\x00\x00\x7f\xf4\x9d\xbe\
\x00\x00\x00\x01\x73\x52\x47\x42\x01\xd9\xc9\x2c\x7f\x00\x00\x20\
\x00\x49\x44\x41\x54\x78\x9c\xed\x9d\x7f\x90\x1c\xc7\x75\xdf\x5f\
\xcf\xce\x1e\x0e\x00\x09\x80\x38\x12\x14\xa5\x40\x26\x45\xd9\x71\
\xc4\x2a\x29\xa2\x29\x5a\xa4\x25\x15\x68\xc5\xaa\xd0\x89\x9c\xc8\
\xc9\xd9\xae\xd8\x8e\x2b\x4a\x2a\xb1\x2b\x29\x97\x13\x47\x4e\x62\
\x3b\xe1\xd2\x4a\x2a\xb6\x65\x47\x96\x1d\x27\x86\x7e\x59\x96\x44\
\x51\x06\x64\x53\xb2\x6c\xd1\x54\x68\x1e\x41\x52\x3f\x4c\x9e\x7e\
\x80\xd6\xf1\xd7\x01\x38\xf0\x0e\x3c\xdc\xef\xdb\xdd\xf9\x3d\x3d\
\xd3\x2f\x7f\x6c\xbf\x45\x63\x6f\xef\xb0\xdd\x7b\xb8\xd9\xd9\xeb\
\x4f\xd5\x16\x89\xbb\xbd\xd9\xd9\x99\xfe\xce\x7b\xaf\xdf\xeb\xd7\
\x00\x16\x8b\xc5\x62\xb1\x58\x2c\x16\x8b\xc5\x62\xb1\x58\x2c\x16\
\x8b\xc5\x62\xb1\x58\x2c\x16\x8b\xc5\x62\xb1\x58\x2c\x16\x8b\xc5\
\x62\xb1\x58\x2c\x16\x8b\xc5\x62\xb1\x58\x2c\x83\x07\x22\x3a\x13\
\x13\x13\x2e\x22\xba\x88\x58\x41\x44\xa7\xe8\x73\xb2\x58\x06\x06\
\x44\x64\x9b\x89\x42\x0a\x86\xed\xfc\x59\x59\x54\xdc\xa2\x4f\x60\
\xb7\x53\xab\xd5\x1c\xc6\x98\x00\x00\x5c\x5a\x5a\x7a\xbd\xeb\xba\
\x6f\x75\x5d\xf7\x68\x1c\xc7\xe7\x3c\xcf\xfb\x1a\x63\x6c\x16\xa4\
\x98\x18\x63\x58\xf4\xf9\x5a\x2c\x3b\x0e\x59\x91\xa9\xa9\xa9\x6b\
\x82\x20\xf8\xfd\x34\x4d\x9b\xa8\x90\x24\xc9\x6a\x18\x86\x1f\x98\
\x9b\x9b\xdb\xab\xbe\xdf\x62\xd9\x35\x28\x22\x39\x1c\x45\xd1\x84\
\xa2\x8f\x0c\x11\xb9\xfc\x2f\x22\x22\xc6\x71\xfc\xf0\xd4\xd4\xd4\
\x35\x60\xc5\x62\xd9\x4d\xd0\x60\x9f\x9b\x9b\x3b\x1c\x86\x21\x89\
\x24\x45\x44\x81\x88\x28\x84\x40\x21\x5a\xff\x2b\x7f\x8e\x71\x1c\
\x7f\x71\x72\x72\xb2\x0a\x56\x2c\x96\xdd\x00\x0d\xf2\xd5\xd5\xd5\
\x03\x51\x14\x9d\x42\x44\xcc\xf3\x9c\xe3\x16\x08\x21\x38\x22\xa2\
\xe7\x79\x9f\x9f\x9a\x9a\x1a\x01\x2b\x16\xcb\x30\x43\x83\x7b\x7a\
\x7a\xfa\x40\x96\x65\x7f\x45\x22\x91\xd6\xe3\x4a\x70\x44\xc4\x30\
\x0c\x1f\xb2\x62\xb1\x0c\x2d\x6a\xe0\x9e\xa6\xe9\x97\xd5\xc1\xaf\
\x01\xc7\x56\x90\xff\x99\xe9\xe9\xe9\x3d\x60\xc5\x62\x19\x26\x54\
\x77\x2b\x49\x92\xbf\x34\x14\x09\xa2\xe2\xa6\x85\x61\xf8\x59\x6b\
\x59\x2c\x43\x03\x0d\xe2\xe5\xe5\xe5\x6b\xe3\x38\x9e\x40\x25\xe6\
\x30\x41\x08\xd1\x16\x4b\x10\x04\xd6\x0d\xb3\x94\x1f\x1a\xbc\x6b\
\x6b\x6b\x07\xe3\x38\x7e\xbc\x1f\x4b\xd2\x05\x8e\xad\xd9\x30\x2b\
\x16\x4b\x79\x51\x2d\x09\xe7\xfc\xb1\x6d\x16\x49\xa7\x58\x4e\x28\
\x62\xb1\xe5\x2e\x96\x72\x40\x22\x59\x58\x58\xd8\x1f\xc7\xf1\x23\
\x72\x50\x67\x5b\x8f\xf9\xbe\xc5\x72\x72\x7a\x7a\x7a\xcf\x56\x75\
\x63\x16\xcb\xc0\x40\x83\xf4\xab\x5f\xfd\xea\xde\x7e\x03\x77\x03\
\xb1\x3c\x84\x88\x15\xb0\x6e\x98\x65\x90\x51\xdd\xad\x28\x8a\x4c\
\x45\x92\x23\x62\x26\x7a\x4c\xae\xb4\xff\x28\xcf\x33\x44\x44\xdf\
\xf7\x1f\x9c\x9c\x9c\xac\x4a\xcb\x62\xdd\x30\xcb\x60\xa1\xe6\x49\
\x14\x77\x4b\x4b\x24\x42\x88\xbc\x8b\x68\x74\xe0\x24\x96\x13\x27\
\x4e\x54\xac\x1b\x66\x19\x28\x68\x30\x9e\x3e\x7d\x7a\x7f\x9a\xa6\
\x8f\x9a\x88\x44\xc9\xbc\x7f\x75\x69\x69\xe9\xe7\xa3\x28\x9a\x95\
\xe2\xe9\x39\xb6\x91\x46\x88\x23\x22\x46\x51\xf4\x49\x45\x2c\xd6\
\xb2\x58\x8a\x85\x44\x32\x3f\x3f\xbf\x2f\x8e\x63\x23\x91\x90\x18\
\xa2\x28\x7a\xf4\xc5\x17\x5f\xbc\x1e\x5a\xee\xdb\xdf\x4e\xd3\xf4\
\x79\xf9\x16\xdd\x89\x00\x12\xcb\x03\x27\x4e\x9c\xb0\x31\x8b\xa5\
\x58\x54\x4b\x12\xc7\xf1\x97\xe5\xa0\xef\xb5\x76\x8b\x44\xc2\x11\
\x11\x39\xe7\x8f\x9c\x3e\x7d\x7a\xbf\x3c\xee\x08\xb4\xc4\xf7\x5d\
\x69\x9a\x3e\x8b\x9a\x96\x45\x3d\x6e\x18\x86\x9f\x9d\x98\x98\x70\
\x41\x2e\x12\x2b\xf8\x92\x59\x76\x1b\x24\x92\xa5\xa5\xa5\x6b\xe2\
\x38\xfe\x0b\x13\x91\x90\xa5\xe0\x9c\x3f\xa6\x88\xc4\x91\xff\xad\
\x00\x00\xac\xac\xac\xbc\x26\x49\x92\xef\xc8\xf7\xf7\x6c\xa9\x54\
\x37\x2c\x4d\xd3\x07\x11\xb1\x8a\x88\xcc\x8a\xc5\xb2\x63\xd0\x60\
\x9b\x9c\x9c\xdc\x47\x96\x04\x11\xb9\xb2\x8e\xa4\x17\x52\x39\x88\
\x27\x16\x16\x16\x2e\x13\x09\x41\x62\x99\x9b\x9b\x7b\x4d\x1c\xc7\
\xcf\xa1\x86\x65\x51\xce\x83\x0a\x29\x3f\x5d\xab\xd5\x1c\x44\x74\
\x6c\xcc\x62\xb9\xea\x74\x58\x92\x47\x50\x29\x95\xd7\x10\x0a\xd5\
\x6a\x3d\xb2\xbc\xbc\x7c\x2d\x6c\x11\x43\x90\x58\x2e\x5e\xbc\x78\
\x73\x18\x86\xcf\xab\x7f\xdf\xa3\x50\xd4\x42\xca\x4f\x01\x00\xb3\
\x01\xbe\xe5\xaa\x42\x83\x79\x62\x62\x62\xd4\xf7\xfd\xbf\x44\xc5\
\xdd\xd2\x10\x0a\x4d\xe1\x4e\x4c\x4f\x4f\x1f\x80\x1e\x02\x6d\x12\
\xcb\xcc\xcc\xcc\xcd\x51\x14\x3d\x27\x8f\xb3\xa5\x65\xe9\x72\x1e\
\x14\xe0\x7f\x42\x5a\x16\x2b\x16\xcb\xf6\xa3\xe6\x49\xa2\x28\xfa\
\x8b\x5e\x9f\xec\x1d\x64\xd8\x72\x83\xbe\x3e\x37\x37\x77\x18\x34\
\x66\xa3\x48\x2c\x0b\x0b\x0b\xb7\xc4\x71\xfc\x22\xf6\x31\x75\x9c\
\x24\xc9\x27\xe8\xb3\xad\x58\x2c\xdb\x86\x3a\xbb\x95\x24\xc9\x97\
\xd0\xa0\x54\x9e\xde\x9f\x24\xc9\xd7\x66\x66\x66\x0e\x01\x00\xd0\
\xd4\xad\xc6\x79\xb4\x2d\x4b\x1c\xc7\x2f\xa9\xe2\xd3\x15\x4b\x1c\
\xc7\x7f\x00\x56\x2c\x96\xed\xa2\x23\x4f\x62\x3a\xbb\x45\x31\xc9\
\x93\x88\xa8\x65\x49\xba\x9c\x4f\x05\x00\xe0\xfc\xf9\xf3\xb7\x50\
\x80\x9f\xe7\x79\x66\xe2\xfe\x45\x51\x64\xc5\x62\xe9\x1f\xa5\x5b\
\xca\xde\x38\x8e\x1f\xa6\x41\x66\x92\x27\x49\x92\xe4\x99\x0b\x17\
\x2e\x8c\xc1\x36\x24\xff\x48\x2c\x8b\x8b\x8b\xaf\x8b\xe3\xf8\x05\
\x54\xdc\xb0\x5e\x84\xa2\x5a\x96\x30\x0c\x7f\x0f\xac\x58\x2c\xa6\
\xd0\x60\x3e\x71\xe2\xc4\x88\x2a\x12\xec\x1e\x28\x5f\xe9\xc9\xfd\
\xd7\x0b\x0b\x0b\x47\x60\x1b\x33\xe4\xaa\x58\xd2\x34\x7d\x51\x7e\
\x5e\xa6\x39\x45\x4d\x62\xf9\xdf\x60\xc5\x62\xd1\xa5\xc3\xdd\xfa\
\xbc\x3a\xa8\x34\x84\x42\xc9\xbe\xaf\x9d\x3b\x77\xee\x46\xd8\x46\
\x91\x28\xe7\xd9\x4e\x4a\xc6\x71\x3c\x85\x66\xcb\x8c\x33\x6c\xc5\
\x2c\xc7\xe1\x52\x1f\x64\x2b\x16\xcb\xd6\xd0\x60\x9e\x9c\x9c\xdc\
\xe7\xfb\xfe\x9f\x75\x8a\xa4\x47\xa1\x90\x48\x9e\x78\xfe\xf9\xe7\
\xc9\xdd\xd2\x0a\xdc\x35\xce\xb7\x9d\x67\x31\x29\x77\x91\x6b\xf0\
\x33\x6c\x59\x96\xdf\x07\x6b\x59\x2c\x57\x42\xe9\xbb\xb5\x27\x0c\
\xc3\x0d\x96\xa4\xc7\x81\x97\x49\x91\x9c\x5a\x5f\x5f\x3f\x04\x57\
\x51\x24\xca\x79\x57\xa0\xb5\x36\xff\xb5\x4a\x21\xa5\x51\xf5\x72\
\x14\x45\xff\x57\x1e\xd3\x96\xbb\x58\x36\x42\x22\xf9\xd2\x97\xbe\
\xb4\x27\x08\x82\x3f\x37\x14\x09\x4d\xbd\x3e\xde\x6b\x32\x71\x1b\
\xcf\xbf\x02\x00\xb0\xbe\xbe\x7e\x73\x9a\xa6\x2f\xc8\x53\xd2\x9d\
\x3a\xa6\x3c\xcf\xc7\xc8\x05\xb3\x96\xc5\xd2\x86\x5c\x0d\x59\xbb\
\xf5\x05\x34\xa8\xd6\x25\x51\x71\xce\x27\x14\x4b\xa2\x2d\x92\x8e\
\x01\xaa\x35\x48\x55\x37\x2c\x49\x92\x29\x5d\xb1\xa8\xdf\x23\x8e\
\xe3\x8f\x5a\xb1\x58\xda\xa8\xb3\x5b\x49\x92\x18\x59\x12\x65\x70\
\x3d\x8e\x88\x26\x96\x84\x6d\xb6\xc3\x96\xdc\x81\xab\xe7\x63\x91\
\x58\xe6\xe7\xe7\x5f\x9b\xa6\x69\x4f\xe5\x2e\x5b\x7c\x9f\x8f\xd0\
\x2a\x49\x2b\x96\x5d\x8c\x1a\x93\x78\x9e\xf7\x10\xf6\xd0\x30\x7b\
\xb3\x41\x95\xa6\xa9\x91\xbb\xd5\x39\x00\x6b\xb5\x9a\xbb\xb6\xb6\
\x76\x70\x72\x72\x72\x5f\xc7\xfb\x7a\x8e\x73\x3a\x2c\x4b\x5f\x8b\
\xbf\xe2\x38\xfe\x30\xd8\x00\x7f\xf7\xd2\xd1\x2d\x85\xdc\x2d\xd3\
\x00\xf8\x31\x44\xbc\x0e\xf4\x45\xd2\x7e\x6f\xbd\x5e\xff\xb1\x20\
\x08\x4e\x7a\x9e\xf7\x37\x49\x92\xcc\x45\x51\x74\xb6\xd9\x6c\x3e\
\xe9\x79\xde\xfb\xeb\xf5\xfa\xad\x70\x49\x00\x3d\x0d\x56\x12\xcb\
\xec\xec\xec\xad\x49\x92\xb4\xf3\x2c\x26\xdf\x2f\x08\x02\x9a\x3a\
\xb6\x62\xd9\x4d\xa8\x81\x7b\x1c\xc7\x5d\xa7\x80\x7b\x1d\x44\x69\
\x9a\xfe\xd5\x0b\x2f\xbc\xb0\x65\xa9\xfc\x26\xe7\x50\x81\xd6\x92\
\xdf\x9b\x94\xb6\x46\x5d\xc9\xf3\x7c\xcd\xf3\xbc\x9f\x05\xcd\xc1\
\xaa\xac\x67\x79\x3d\x05\xf8\x34\x15\xac\xfb\x3d\x3d\xcf\xfb\x90\
\xee\xe7\x5b\x4a\x8c\x52\x05\x3c\xc2\x39\xff\x53\xec\xa3\xc0\x91\
\x73\xde\x76\xb7\x74\x0a\x1c\x69\x69\xae\xe7\x79\xb7\x25\x49\x72\
\x46\x1e\x36\x93\xaf\x5c\x6e\x20\x94\xcb\xae\x2c\xed\x73\x0b\xc3\
\xf0\xb7\x40\x33\x29\x48\x62\x39\x7b\xf6\xec\x6b\x39\xe7\x2f\x99\
\x7c\x5f\x25\x83\xff\xbb\x60\xc5\x32\xfc\xd0\x0d\x46\xc4\x6a\x1f\
\x79\x12\x12\xc9\x97\x11\xd1\xd8\x92\x78\x9e\x77\x5b\x1c\xc7\xb3\
\x3d\x9e\x43\xae\x64\xd0\x7f\x87\x8e\xa3\x2b\x96\x7a\xbd\xfe\x3a\
\xce\x79\xdb\xb2\x68\x16\x52\x52\x52\xd2\x8a\x65\x98\xa1\xc1\x7c\
\xfc\xf8\xf1\x6a\x18\x86\x27\x4c\x44\x42\x6e\x0b\xe7\xfc\x31\x93\
\x29\x60\x1a\xb0\x4b\x4b\x4b\xaf\x4f\xd3\x74\x46\xf3\x1c\xda\xdb\
\xd4\x45\x51\xf4\x7e\x79\x3c\xd7\x40\x2c\xb7\x76\xba\x61\x06\x85\
\x94\x56\x2c\xc3\x08\xdd\x50\x19\x93\x9c\x34\x11\x89\x92\x27\x79\
\x62\x69\x69\x49\x7b\xe3\x51\x7a\xef\xe2\xe2\xe2\x8d\x9c\xf3\xe7\
\xb1\xe3\xa9\xae\x21\x16\xaa\x46\xfe\x25\x79\xdc\x9e\xb7\x40\x27\
\xb1\x34\x1a\x8d\xef\xce\xb2\xec\xac\x3c\xa6\xce\x39\x08\xa5\xbb\
\xcb\xff\x02\x4d\xcb\x66\x19\x60\x94\xe5\xbb\x6e\x1c\xc7\x46\x31\
\x89\x22\x92\x53\x86\x81\xbb\x03\x00\x70\xe1\xc2\x85\x31\xce\xf9\
\xd3\xf2\x1c\x32\x0d\xb7\xa7\x73\xb0\xe6\xd8\x9a\x48\xf8\xd7\x60\
\x28\x16\x69\xd5\xce\xa9\xe7\xd2\xc3\x07\xa3\x2a\x56\xdf\xf7\x6d\
\x80\x3f\x0c\x50\xad\xd2\xd4\xd4\xd4\x48\x18\x86\x7f\x82\x7d\x2c\
\xba\x4a\xd3\xf4\x09\x72\xb7\x74\x02\x77\x12\xc9\xfa\xfa\xfa\xa1\
\x28\x8a\x68\x8f\x94\xcb\x5c\x1e\xcd\xf3\x41\xd1\x22\x17\x42\x08\
\xdf\xf7\x7f\x0a\xcc\xc5\xf2\xdd\x59\x96\x9d\x47\xcd\xd9\x30\xb5\
\xdc\x25\x0c\xc3\x0f\x82\xb5\x2c\xe5\x45\x75\xb7\x82\x20\xf8\x3c\
\x9a\x95\xa5\x50\x81\xe3\x93\xcd\x66\xf3\x7a\x30\x10\x09\x22\xb2\
\x85\x85\x85\xfd\x51\x14\xfd\x3f\xec\x73\xb7\xad\x0e\x72\x44\x14\
\x79\x9e\xe7\x61\x18\xbe\x07\x0c\xc5\x22\x27\x15\xce\xa9\xdf\xb7\
\x47\x54\xcb\x42\x62\xb1\x96\xa5\x4c\xa8\xee\x16\xcd\x6e\x99\x4e\
\x01\xa7\x69\xfa\xc4\xea\xea\xaa\x49\xc6\xdd\x41\x44\x36\x31\x31\
\xe1\x26\x49\x72\xd9\xc2\xaf\x6d\x24\x97\x06\x26\x0c\x82\xe0\x5e\
\x30\x14\xcb\xca\xca\xca\xf7\xa6\x69\x7a\x5e\x1e\xb3\x67\x6b\xa7\
\x5a\x96\x66\xb3\x49\x53\xd7\xd6\xb2\x94\x01\x6a\xc5\x33\x39\x39\
\x59\x0d\xc3\xf0\x41\x1a\xa0\x26\xee\x16\xe7\xfc\x31\xc3\xc0\x9d\
\x29\x22\xf9\x63\x75\x00\x5e\x05\x72\x6c\xb9\x4e\x61\x1c\xc7\xef\
\x02\x43\xb1\xac\xae\xae\xbe\x81\x73\xfe\x0a\x6a\xc6\x4f\xf2\x3d\
\x54\xee\xf2\x01\x90\x56\xd7\x8a\x65\x80\xa1\xa7\xf8\x89\x13\x27\
\x2a\x61\x18\xf6\x3b\xbb\xf5\x58\xbd\x5e\x37\x29\x4b\x69\x17\x11\
\x46\x51\xf4\x80\x3c\x66\xaa\x1b\x87\x68\x92\xcb\x05\x58\x8d\x66\
\xb3\xf9\x36\x30\x14\xcb\xfa\xfa\xfa\x9b\xd2\x34\x7d\x19\xcd\x66\
\xe4\xc8\xb2\xd8\xd9\xb0\x41\x86\x2c\x89\x3a\xbb\x65\x2a\x92\x2c\
\xcb\x1e\xbd\x52\x07\xc7\x6e\xa8\xfb\x91\x44\x51\xf4\x51\xdc\xde\
\x98\x64\x4b\x68\x26\x2c\xcf\xf3\xb5\x20\x08\xde\x02\xe6\x6e\xd8\
\xdf\xc9\xb2\xec\x65\xd4\x98\x0d\xa3\x53\x50\xf2\x2c\xd6\x0d\x1b\
\x44\x94\x52\xf9\x4a\x10\x04\x7d\x59\x92\x38\x8e\x1f\x37\x8c\x49\
\x54\x91\xfc\x1f\x79\xcc\x54\xf3\x1c\xfa\x42\x11\xcb\x62\xbd\x5e\
\xbf\x1d\xcc\xdd\xb0\xdb\x92\x24\x99\x43\xcd\x09\x90\x3c\xcf\xdb\
\x0f\x06\xdf\xf7\x3f\x00\x56\x2c\x83\x03\xc5\x03\x93\x93\x93\x55\
\xdf\xf7\xff\x18\xfb\xcb\x93\x3c\x76\xf6\xec\xd9\x83\x60\x26\x92\
\x0a\x00\x80\xef\xfb\x1f\x52\x8f\xb9\xd3\x90\x58\x38\xe7\xf3\x8d\
\x46\xe3\x4e\x30\x2c\xd1\x5f\x5c\x5c\x7c\x13\xe7\xfc\x82\x3c\xac\
\xe9\xd4\xf1\xaf\x83\x15\x4b\xf1\xa8\x31\x49\x14\x45\xed\xc0\x5d\
\xf3\xa6\x6e\x87\x25\xa9\x00\x00\x84\x61\xf8\xdb\xba\xe7\x70\x95\
\xc8\x50\x5a\x96\xb5\xb5\xb5\x37\x82\xbe\x58\x5c\x68\xb9\x61\x6f\
\xc9\xf3\x7c\x5e\x3d\x66\x8f\x08\xb2\x44\x9e\xe7\xd5\xc0\x8a\xa5\
\x38\xd4\xe5\xb2\xbe\xef\x7f\x06\xfb\x98\x02\xce\xb2\xec\x14\x15\
\x38\x6a\xb6\x39\x6d\x8b\x24\x08\x82\x9a\x32\xa0\xae\x6a\xe4\xde\
\x23\x24\x96\xf9\x24\x49\xbe\x17\x34\xc5\xd2\x51\xe1\xac\x6d\x59\
\x54\xb1\x28\xb5\x69\x56\x2c\x3b\x89\x6a\x49\x7c\xdf\xff\xac\xbc\
\x31\xba\x1d\x1c\x33\x6c\x89\xe4\x71\xd3\x36\xa7\xf4\xe4\x0d\xc3\
\xf0\x7d\x74\x0e\x03\x22\x12\x82\xbe\xe3\xd9\xf5\xf5\xf5\x9b\xc1\
\x50\x2c\x6b\x6b\x6b\x6f\x4c\x92\x64\x1e\xf5\xd7\xb3\x08\x3a\x87\
\x28\x8a\xfe\x27\x58\xb1\xec\x1c\x64\x49\x6a\xb5\x9a\x13\x86\xe1\
\x67\xe4\x0d\xd1\xdd\xc4\x87\xaa\x80\x9f\x34\x6d\x04\x41\x22\x89\
\xe3\xf8\x17\x94\x63\x0e\x92\x48\x08\xfa\xae\x53\xcb\xcb\xcb\xaf\
\xd6\xfd\xae\x4a\xd5\xf1\x1d\x79\x9e\x53\x9e\x45\x67\xb7\x62\x55\
\x2c\xbf\x06\x56\x2c\x57\x1f\x12\xc9\xf1\xe3\xc7\xab\x51\x14\x5d\
\x26\x12\xec\xbd\x83\x23\x65\x9e\x9f\x7a\xf9\xe5\x97\xb5\xf3\x24\
\x70\xb9\x48\x7e\x4e\x7e\x66\x2e\xeb\xaf\xb4\xeb\xb6\x76\x08\xaa\
\x32\xf8\x96\xc9\x77\x26\xcb\x22\x03\xfc\x45\x79\x4c\xa3\x72\x97\
\x28\x8a\xee\x07\x2b\x96\xab\x07\xe5\x49\x64\xe0\xde\x75\x76\xab\
\x87\x2c\x72\x5f\x65\x29\xa0\x0c\x9a\x28\x8a\xde\x9b\xe7\xad\xd9\
\x58\x55\x24\x03\x2a\x94\xb6\xab\x19\x86\xa1\x69\x49\x8e\x0b\xad\
\xa5\xcb\x77\x64\x59\xb6\x80\x9a\x96\x45\xb4\x2e\x0c\x59\x96\xfb\
\xc0\x8a\x65\xfb\x51\xb2\xdd\x4e\x18\x86\x9f\x96\xd7\xde\x34\x99\
\xf8\x54\xb3\xd9\x34\xea\x2a\x8f\x88\x55\x68\x4d\x01\xff\xa4\x3c\
\x66\x2e\x06\x55\x19\xdd\xa1\xa7\xfa\x23\xf3\xf3\xf3\xfb\xd4\xdc\
\x4f\x2f\xd0\x43\xa2\x5e\xaf\xdf\x1e\xc7\xf1\x05\xec\x52\xee\x72\
\x85\x87\x85\x2a\x96\xff\x06\x56\x2c\xdb\x87\xd2\xd6\xd3\xf1\x3c\
\xef\x01\xec\x23\x4f\x92\xa6\xe9\x33\x7d\x88\x84\x02\xf7\x7f\x2a\
\x5b\x1a\xe5\x03\x1a\x93\x6c\x89\xb2\x94\xf9\xf3\x54\x93\xa5\xd3\
\x3a\x55\x29\x77\x79\x33\xe7\x7c\x41\x1e\xd6\xa8\x90\x32\x08\x02\
\x6b\x59\xb6\x03\x9a\xdd\xaa\xd5\x6a\xae\xef\xfb\x24\x12\xa3\x2e\
\x22\x59\x96\x3d\x7d\xf1\xe2\xc5\x1b\xa0\x0f\x91\x2c\x2f\x2f\xbf\
\x3b\xcf\xf3\x84\xe2\x12\xb3\xa1\x5a\x2c\x6a\x53\xee\x2c\xcb\x3e\
\x0b\x00\x8c\xdc\x5a\xdd\xeb\xb1\xb4\xb4\xf4\x66\xce\xf9\x92\x3c\
\xb4\xce\x42\x34\xa1\x2c\xab\xb6\x96\xa5\x1f\x48\x24\xe3\xe3\xe3\
\x95\x34\x4d\xa9\xb8\xd0\x74\x13\x9f\xaf\x78\x9e\x77\x03\xf4\xb1\
\x1d\x5c\xa3\xd1\xf8\xfb\x69\x9a\x86\x72\x20\x94\x52\x24\x78\xf9\
\xfa\x78\x7a\x80\x7c\x4c\xbd\xde\xba\xd7\x65\x61\x61\xe1\xfb\x29\
\xc0\x57\xdd\xb0\x5e\x4e\xa5\x8b\x1b\xd6\x73\x0f\x00\xcb\xc6\x3c\
\xc9\x27\xe4\x85\x35\x75\xb7\xbe\x46\xee\x96\x81\x48\x28\x8f\xf0\
\xf6\x34\x4d\x7d\x39\x18\xf2\x72\x85\x25\x97\xd3\x31\x90\xe9\x1a\
\x69\x77\x76\x01\x25\x66\x69\x36\x9b\x77\xc5\x71\xdc\x76\xc3\x74\
\x0a\x29\xc9\x43\x08\x82\xe0\x57\x4d\xce\x61\xd7\xa2\x3c\xd9\x18\
\xb9\x5b\xa6\xbb\xef\x66\x59\xf6\x0c\x59\x12\xdd\xad\x17\x14\x77\
\xeb\x58\x9e\xe7\xeb\xa8\x88\x64\x88\x84\x82\x54\xb8\xa9\xac\x52\
\xd4\x1a\xa8\x74\x9d\x56\x57\x57\xdf\x9a\x65\x19\xb9\x61\x46\x79\
\x96\x20\x08\x7e\x19\xac\x65\xb9\x32\x74\x71\x6a\xb5\x9a\xab\x2e\
\xba\xd2\x1c\x0b\x1c\x5b\x19\xe4\x49\x25\x26\xd1\x12\x09\x3d\x29\
\x57\x57\x57\xef\xca\xf3\x7c\x0d\xf5\x93\x6c\x65\x42\x74\x29\x62\
\xd4\x1a\xa8\x6a\x6d\x18\xe7\x7c\x4d\x1e\xd7\x28\x83\x9f\x24\x09\
\x89\xc5\x5a\x96\x6e\xa8\xc9\xc4\x24\x49\x8c\x2c\x89\xb2\x89\xcf\
\x33\xcb\xcb\xcb\x37\x81\x99\x25\xa1\x4c\xf4\xf7\xd1\x8a\xbf\xab\
\xb8\x3a\x71\x50\x50\xdb\x20\xfd\x57\x93\xeb\xa6\x24\x25\xef\xe2\
\x9c\x2f\xcb\xe3\x1a\x89\xc5\xf7\xfd\xff\x64\x72\x0e\x43\x8f\xda\
\x22\x34\x8a\xa2\x4f\xa2\x41\xb7\x14\x55\x24\x41\x10\xf4\x25\x92\
\xd5\xd5\xd5\xdb\xf2\x3c\x9f\x33\xb8\xd9\x65\x46\x7d\xaa\xff\x67\
\xc3\xeb\xd7\xb6\xc4\x34\x1b\x66\x5a\xee\x42\xe7\x20\xb7\xbd\xb0\
\x96\x45\x15\x89\xef\xfb\x7f\x88\x66\x2d\x85\x48\x24\xcf\x2a\x31\
\x89\xee\x14\x70\xbb\x85\x8f\xd2\xc5\x71\xb7\x88\x84\x10\x4a\x06\
\xff\x7d\xa0\xb9\xf0\x0b\x36\x89\x59\x74\x33\xf8\x74\x0e\xd6\xb2\
\x48\x36\x9b\xdd\x32\xd9\x02\x9a\x73\x3e\xb9\x0d\xee\xd6\xeb\xe2\
\x38\x36\xdd\x22\x61\x58\x10\x8a\x75\xa6\x0e\xfa\xba\x62\xa1\xfd\
\x59\xee\x4c\xd3\x54\x2b\xc0\x97\xf7\xbe\xdd\xe4\x2f\x8a\xa2\xff\
\x62\x72\x4f\x87\x06\x2a\x9f\xa8\xd5\x6a\x4e\x92\x24\x9f\x92\xd7\
\x49\xab\xc0\x91\x6e\x28\xe7\xfc\x1b\x4b\x4b\x4b\xaf\x82\x3e\x2c\
\xc9\xcc\xcc\xcc\xab\xe2\x38\xfe\x8e\x3c\xf4\x6e\x15\x49\x7b\xa0\
\xca\x69\x5e\x11\x04\xc1\x7b\xc1\x40\x2c\x14\xb3\xcc\xce\xce\xde\
\x91\xa6\xe9\x65\x19\xfc\x1e\x3e\xff\xb2\xda\x30\xdf\xf7\xa9\x7d\
\xec\xee\x0a\xf0\x55\x77\x2b\x08\x02\xb2\x24\x69\xe7\x05\xbb\x02\
\x14\x7c\x7e\xd3\xf7\x7d\xda\xc7\x5d\xd7\x92\x50\x27\xc9\xc3\x51\
\x14\x3d\xdd\xeb\xcd\x1c\x66\x14\x6b\x2e\x64\x06\x3d\xf5\x3c\xef\
\x27\x40\x19\xfc\x1a\xd7\x97\x2c\xf5\xed\xbd\x56\x1d\x77\xd4\x8c\
\xa9\x62\x31\x72\x05\x4b\x0b\x95\x4b\xd4\x6a\x35\x47\x11\x89\x51\
\x59\x4a\x9a\xa6\x7f\xed\xfb\xfe\xab\xc0\x2c\x99\xe8\x40\x2b\x99\
\x78\x30\x8a\xa2\xaf\xa8\xc7\xb5\xb4\x11\xe4\x8a\x79\x9e\xf7\xe3\
\xd0\x87\x65\xa9\xd7\xeb\x77\x44\x51\xd4\xb3\x65\xe9\x38\x07\x8a\
\x9b\xfe\x03\x5c\x12\xe0\xf0\x5a\x16\x65\x97\x59\x27\x8a\xa2\x8f\
\xc9\x0b\x61\xba\xf5\xc2\x37\xc3\x30\x7c\x0d\xf4\x61\x49\x66\x66\
\x66\x0e\x85\x61\x48\xfd\x80\xad\x48\xba\x43\xad\x5b\x79\x18\x86\
\x3f\x0a\x7d\xc4\x2c\x2b\x2b\x2b\x77\x66\x59\x66\x32\xe5\x2e\x28\
\xc6\x89\xe3\xf8\xe7\x4c\xce\xa1\x34\x28\x4d\x18\x1c\xdf\xf7\x3f\
\x2e\x2f\x80\x51\x32\x51\x08\xf1\xcc\x99\x33\x67\x8e\x80\xa1\x48\
\x10\x91\x4d\x4f\x4f\xef\x49\xd3\xf4\xcb\xb8\x83\xbd\xb7\xca\x0a\
\x2d\x25\xc8\xb2\x2c\x0c\x82\xe0\x1f\x40\x1f\xb3\x61\x2b\x2b\x2b\
\xdf\x9f\xa6\xe9\xaa\x3c\xb4\xa9\x65\xf9\x77\x26\xe7\x30\xf0\xa8\
\xd5\xa9\x61\x18\x7e\x52\x7e\x71\xd3\x96\x42\xdf\x58\x5c\x5c\xec\
\x2b\x26\x91\x4d\xf2\x8c\x76\xdc\xda\xc5\x50\xcf\x30\xcf\xf7\xfd\
\x1f\x32\xbc\xfe\x2e\xc8\xd9\xb0\x3e\x32\xf8\x42\x08\x81\x71\x1c\
\xb7\xc5\x32\x14\x01\xbe\xda\x2d\x25\x08\x02\xb2\x24\x3a\x85\x73\
\xaa\xbb\xf5\xb4\xb2\xee\x5b\xeb\x26\xd1\x9a\x8b\xc9\xc9\xc9\x2a\
\xb5\x36\xb2\x96\x44\x9b\x1c\x5b\x96\x25\x58\x5f\x5f\xbf\x07\xcc\
\x02\x7c\x2a\xa4\xbc\x3b\x49\x92\x8b\xf2\xb8\xa6\x6e\xd8\xbf\x87\
\x61\x98\x0d\x53\x1b\x41\x50\x4c\x22\x84\xe0\xb2\xa3\x60\xaf\x4d\
\xa0\xa9\xc0\xf1\xeb\x7d\x64\xdc\xd5\xa6\xd9\x56\x24\xfd\x41\x96\
\xa5\xd1\x6c\x36\xef\x86\x3e\xdd\x30\x65\x36\x4c\x37\x83\x4f\x62\
\xf9\x45\x93\x31\x31\x30\x74\x58\x92\xcb\x92\x89\x1a\xb4\x57\x26\
\x2a\x0d\xb3\x4d\x44\xe2\x00\x00\xa3\x1a\xb2\x3c\xcf\x79\xaf\x42\
\xb5\x74\x85\x2c\xfc\xd2\xfa\xfa\xfa\x9b\x0c\xef\x8b\x0b\xad\xf5\
\x2c\x6f\xcd\xf3\x5c\xbb\xea\x58\x9d\x3a\x0e\xc3\xf0\x3f\x42\x19\
\xdd\x30\x12\xc9\xf8\xf8\x78\x25\x49\x12\x2a\x4b\x31\x9a\x02\x8e\
\xa2\xe8\x69\x25\x4f\xa2\x9b\x4c\x54\xfb\x01\xb7\x27\x10\x34\x77\
\xc3\xb5\x74\x87\x6a\xb2\xe6\x3c\xcf\x7b\x03\xf4\x17\xb3\xbc\x85\
\x73\xde\x57\x80\xaf\xec\x69\x59\x0e\xcb\xa2\xe6\x49\x7c\xdf\xdf\
\x90\x71\xef\x91\x76\xa9\x7c\x1f\x65\x29\xed\x2e\x8e\xeb\xeb\xeb\
\xbf\xa7\x9e\x87\x15\xca\xb6\x41\x6e\xf1\xb9\x7a\xbd\xfe\x3a\x93\
\xfb\xa4\x2c\x69\xb8\x9b\xaa\x8e\x0d\x0a\x29\xc9\x0d\xfb\x05\x28\
\xc3\x6c\x98\xfa\x04\x27\x91\xe8\x16\x38\x52\xe0\x9e\x24\xc9\xb7\
\x15\x91\x98\x58\x12\x6a\x9a\xfd\x5b\xa8\xb8\x5b\xb8\x31\xfb\xab\
\x35\x32\x2c\x1b\x20\x37\xec\xb9\x95\x95\x15\xd3\xbc\x96\x2a\x96\
\x15\xf5\xb8\xbd\xa0\x16\x52\x26\x49\x32\xd8\x85\x94\xaa\x6f\x18\
\x45\xd1\x27\xb0\x23\x70\xef\x11\x8a\x49\x4e\x07\x41\x60\x34\xbb\
\xd5\xd1\x0f\xf8\xfd\x74\xdc\xce\x09\x04\x2b\x94\x6d\x85\xfa\x1c\
\x9f\xa6\x4a\x09\xd3\x9a\xbb\x95\x95\x95\x3b\xe3\x38\xd6\x5a\xcf\
\xa2\x94\xdc\x90\x68\xdf\x07\x83\x28\x16\x75\x56\x29\x08\x02\xda\
\x40\x47\x77\x7b\x68\x4a\x26\x4e\xce\xce\xce\xbe\x1a\xcc\xca\x52\
\x18\x99\xf2\x20\x08\x7e\x85\x2e\xf6\x66\x96\xc4\x0a\x65\xfb\x50\
\x0a\x54\x9f\x6a\x34\x1a\x7d\xf5\x72\x5e\x5c\x5c\xbc\x5b\x67\xf1\
\x57\xb7\xda\xb0\x34\x4d\xdb\x53\xc7\x03\x51\xee\xa2\xb4\x14\xda\
\x90\x71\xd7\x18\x8c\x54\xe0\x78\x7a\x75\x75\xf5\x6f\x81\xe1\xd3\
\x40\xe9\xbd\xf5\x8b\xca\x45\xb6\x4a\xd8\x39\x28\x29\x7c\x0a\x11\
\xb5\xf7\x99\x81\x8d\x6e\x58\x4f\x62\xe9\x18\x67\x22\x97\x2d\x3c\
\xd5\x98\xa5\xd0\xd9\xb0\x8e\x45\x57\x46\x1d\x1c\x95\x86\x6c\xdf\
\x34\xcd\xb8\x83\x12\x14\x06\x41\xf0\x6f\xf0\x92\x45\xb3\x22\xd9\
\x61\x94\xfb\xf9\xe8\xd4\xd4\xd4\x88\x3a\x46\x34\xc6\x15\x75\xbf\
\xf9\x81\x2c\xcb\xea\xb8\x45\x47\xca\x6e\xb7\x78\x93\xaa\xe3\x62\
\x92\x92\xca\xec\x96\x4b\x6d\x4e\x0d\x92\x78\xe4\xdb\x7e\xdb\x34\
\x10\x04\x99\x6d\x87\x96\x58\x7f\xba\xb3\x69\xb6\xa5\x10\xa8\x67\
\xd8\x17\xe8\x69\xde\x8f\x58\x94\x65\xc5\x5a\xed\x5b\x95\x95\x92\
\xed\xc5\x5f\x3b\x2a\x16\x35\x26\xf1\x7d\xff\x8f\xd4\x8b\xa3\x7b\
\x31\x39\xe7\x7f\xb3\xba\xba\x7a\x14\xfa\x74\xb7\x3c\xcf\xfb\x27\
\x59\x96\xa5\xdd\x9a\x66\xdb\x58\xa4\x10\xc8\x9d\x7e\x80\x1e\xaa\
\xa6\x62\x59\x5d\x5d\xbd\x8b\x56\x4a\x76\x13\xcb\x16\xa8\x4d\xf6\
\xda\x7d\x00\x76\x44\x2c\xea\xca\xc4\x28\x8a\x8c\x44\xa2\x2c\x35\
\xfd\xce\xda\xda\xda\x6b\xa1\xff\x98\xe4\x3d\x59\x96\x25\xf2\xf0\
\x39\x6e\x12\xb8\x5b\x76\x1c\x12\xcb\x27\xe5\x6c\xa4\x56\x37\x4a\
\xf5\x1e\xcb\x56\x48\x5d\x7b\x1d\x5f\x01\xb5\x6f\xd8\xaf\x98\x8e\
\x35\x2d\x3a\x62\x92\x76\x9e\xc4\xf0\xe2\x7d\x53\x59\xbe\x6b\x2c\
\x92\xb5\xb5\xb5\x1f\x16\x42\x44\xf2\xd8\xed\x44\x95\x15\xca\xc0\
\x40\x6e\xd8\x71\x30\x7c\xa2\xab\x19\xfc\x38\x8e\x17\xb1\xe5\xae\
\xf7\xdc\x8c\x50\x5d\x83\x1f\x04\xc1\xd5\xed\x75\xac\xd6\x6e\x75\
\x96\x83\x68\x40\x53\x88\xdf\xda\x8e\xd9\xad\x8b\x17\x2f\x1e\xe3\
\x9c\x07\xd8\xd1\xc5\xd1\x4e\x03\x0f\x1c\x94\x1f\x33\xea\x46\xa9\
\xde\x73\xb9\x3f\x0b\x65\xf0\x7b\xaa\x42\xef\xcc\xb3\x78\x9e\x77\
\x75\xda\xb7\x76\xac\x71\x37\x5a\x74\xa5\xcc\xb3\x7f\x7b\x66\x66\
\xa6\x6f\x4b\xb2\xbe\xbe\xfe\x8e\x34\x4d\x87\xa6\xd5\xe9\x30\x23\
\xef\x0d\xed\xbe\x6c\xbc\xa5\x36\xcd\x6c\x36\x1a\x8d\x76\x21\x25\
\x59\x8a\x1e\x1f\x8c\xea\x6c\x18\x05\xf8\xdb\x33\x75\xac\x56\xdf\
\x2a\xcb\x77\xb5\x0a\x1c\x95\xf2\x82\x67\x29\x99\x68\x28\x12\xda\
\x03\xfd\x2e\x2a\x75\xe8\xb4\x24\x96\xc1\x45\x79\x58\x1a\x6f\x7c\
\x4a\x0f\xca\x7a\xbd\xfe\x7d\x69\x9a\xd2\x18\xd0\xdd\xcc\x88\x26\
\x92\xda\x31\x4b\x5f\x62\x51\x2d\x49\x1c\xc7\x1f\x96\x1f\x64\x54\
\xe0\xd8\x6f\x32\x91\x9e\x26\xe7\xcf\x9f\xbf\x9d\xa6\x0b\x55\x3f\
\xd5\x0a\x65\xf0\xa1\x15\xc5\xd8\x9a\x85\xfa\x55\x30\xec\x04\xa9\
\x74\xf4\x7c\x2b\xad\x67\xd1\x1c\x0b\xed\x42\xca\x28\x8a\x7e\xd9\
\xf4\x3c\x00\x2e\xe5\x49\x1c\x00\x60\xcd\x66\xf3\x38\xf6\xd1\xc1\
\x31\xcb\xb2\xa7\xfb\xc9\x93\x28\x0d\xd5\xde\xd0\x6d\x2f\x0e\x2b\
\x94\x52\xd1\x76\x7f\xea\xf5\x3a\x15\x30\x6a\x57\xfb\x2a\x2b\x25\
\xdf\x9e\x65\xd9\x06\x17\x5c\x67\x36\xac\xd1\x68\x98\xc5\x2c\x6a\
\x15\xb0\x52\xbb\x65\x54\xe0\xc8\x39\x7f\x76\x7e\x7e\xfe\x7a\xe8\
\xd3\x92\xcc\xce\xce\xde\x1a\xc7\xf1\x39\xd4\xcc\xd2\x5a\x06\x92\
\xb6\xfb\xa3\x94\x99\x54\x75\xc7\x86\xba\x7f\x4d\x9e\xe7\x4d\xd4\
\x8c\x57\xd5\xaa\x63\xcf\xf3\xf4\xb6\xc9\x53\x63\x92\x38\x8e\x3f\
\x82\xb2\xf4\xdd\xa4\xc0\x31\xcf\xf3\x6f\x98\xae\x27\x01\xa5\x4e\
\xe8\xe2\xc5\x8b\x37\x27\x49\xf2\x9c\x3c\xf6\x86\xfd\x02\xad\x50\
\x4a\x09\x75\xa3\xbc\xac\x51\x84\xa9\x58\xd6\xd7\xd7\xdf\x91\x24\
\x89\x2f\x8f\xad\xd5\xbe\x55\x71\x07\x7f\xad\x27\xb1\xa8\x96\xa4\
\xd9\x6c\x7e\x54\x1e\x4f\x77\x45\x20\x05\xee\xc6\x7d\xb7\x40\xa9\
\x1c\x0e\x82\xe0\xa6\x24\x49\x9e\xa5\x73\xe9\xf8\x92\x56\x28\x25\
\x46\x08\x21\xb2\xac\x55\x92\x17\x45\xd1\x3f\xef\x43\x2c\x15\x68\
\x4d\x1d\xdf\x43\x33\xa1\xbd\x88\x45\x2d\xa4\x54\x2c\xcb\x7f\xdf\
\x72\xcc\xaa\x81\x7b\xbd\x5e\xff\x88\x3c\x96\x51\x4c\x92\xe7\x79\
\x3f\xeb\x49\xda\x96\x64\x61\x61\xe1\x48\x92\x24\x5f\x47\xb3\xa5\
\xc4\x96\x01\x47\xb4\x36\x5e\x15\xb2\xec\x08\x3d\xcf\x1b\xef\x43\
\x2c\x94\xc1\xff\x41\xce\xb9\x96\x65\xa1\xd3\x51\x32\xf8\xf7\x77\
\x1d\xbb\x6a\x73\xba\x20\x08\xda\x22\xd1\xfc\xd2\xe4\x12\x4d\x99\
\xb6\x14\x52\x45\x32\x3d\x3d\x7d\x20\x0c\xc3\x27\x4c\xce\xc5\x52\
\x0e\x94\x27\x7a\x8e\x88\x22\xcb\xb2\x38\x8e\xe3\x7f\xd8\xaf\x58\
\x16\x16\x16\xde\x99\xa6\xa9\x27\x3f\x46\x57\x2c\x1c\x5b\x96\x85\
\xc4\xe2\xa8\x1f\xe0\x40\xcb\xcf\xbb\x5f\xfe\x81\xd1\x14\xb0\x10\
\xe2\xd9\x3e\x33\xee\x64\x49\xf6\x53\x17\x47\x2b\x92\xe1\xa5\xc3\
\x65\xa6\x20\xdc\xe7\x9c\xbf\xab\x5f\xb1\xac\xac\xac\xbc\x33\xcb\
\xb2\xbe\x2c\x8b\xef\xfb\x3f\xd3\x1e\x97\x34\x38\x2f\x5c\xb8\xf0\
\x26\xce\x79\xac\x5b\xa2\xae\x66\xdc\xc9\xdd\xd2\x5d\x99\x48\x27\
\x23\xf7\x4a\x19\x09\xc3\xf0\x0b\xf2\xf0\x5d\x9b\x41\xd8\x58\x64\
\x38\xe8\x72\x5f\xa9\x67\x58\xd3\xf3\xbc\x1f\xec\x57\x2c\x8d\x46\
\xe3\x87\x39\xe7\xa1\xfc\x38\x9d\x56\x48\x39\x22\x8a\x24\x49\x56\
\xcf\x9c\x39\x73\x94\x0e\x4a\x9d\x4a\x7e\x5b\xbe\x4f\x67\x23\x1f\
\x8a\x49\x9e\xef\xd7\x92\x28\xed\x8d\x4e\xa0\x92\xb3\xb1\x42\x19\
\x5e\x36\xb9\xb7\x54\x92\x52\xf7\x7d\xff\x9d\xfd\x8a\x65\x69\x69\
\xe9\xde\x24\x49\x62\xf9\x91\x3a\x96\x25\x43\x44\x5c\x5e\x5e\xfe\
\x59\x00\x00\x87\x31\x96\xd7\x6a\x35\xc7\x71\x9c\x77\xb4\x8e\x8f\
\x0e\x63\x0c\x18\xbb\xe2\x54\x72\x0e\x00\x15\xce\xf9\x74\x9a\xa6\
\xf7\x8e\x8d\x8d\x5d\x40\xc4\x0a\x63\x2c\xd7\xf9\x42\xb2\xd5\x29\
\xde\x7f\xff\xfd\x95\x8f\x7f\xfc\xe3\x9f\x19\x19\x19\x19\x07\x80\
\x8c\x31\xe6\xf6\x78\x1e\x96\xe1\xc2\x41\x44\xc1\x18\x3b\xb8\x77\
\xef\xde\x3f\x8d\xa2\xe8\x18\x63\x2c\xd3\x15\x0b\x63\x2c\x9b\x98\
\x98\x70\x8f\x1c\x39\xf2\x70\xbd\x5e\xff\x47\x59\x96\x45\x74\x6c\
\x8d\xc3\xa0\xe3\x38\x77\x02\x00\xd0\x87\x3b\x8c\xb1\xfd\xad\xe3\
\x33\xec\xe1\x00\x19\x00\xb8\x42\x88\x69\x21\xc4\xbd\x7b\xf7\xee\
\x3d\x6f\x22\x12\x9a\x65\x63\x8c\xb1\x28\x8a\xfe\x68\x74\x74\xf4\
\xc7\x10\x31\x03\x00\x57\x15\x88\x15\xcb\x70\xd2\xed\xbe\x22\x22\
\x30\xc6\x1c\x44\x14\x8e\xe3\x1c\xa8\x56\xab\x7f\xd2\x6c\x36\x7f\
\x84\x31\xf6\x15\xdd\x31\x76\xcf\x3d\xf7\x64\x88\xe8\x32\xc6\x1e\
\x69\x36\x9b\x3f\x39\x3a\x3a\xfa\xa9\x6a\xb5\xba\x5f\x0a\xd1\x41\
\xdc\x7c\xa8\xcb\x73\x63\x23\x23\x23\x23\x20\x15\xc6\x6a\xb5\x5a\
\xe6\x38\xce\x19\x00\x40\xf9\xda\x8a\x5c\x8a\xe4\xe5\x20\x08\xde\
\x3d\x3a\x3a\x7a\x76\x62\x62\xc2\x35\x14\x89\xc3\x18\xc3\x28\x8a\
\x3e\x3c\x3a\x3a\xfa\xcf\x48\x80\x3a\xc7\x19\x40\xc4\x80\xbc\x7a\
\x79\xe0\x0d\x2c\x8c\x31\x07\x00\x44\xa5\x52\x39\x3c\x3a\x3a\xfa\
\xc5\x30\x0c\xef\x66\x8c\xe5\xba\xcd\x2a\x18\x63\xd9\xe4\xe4\x64\
\xf5\xc0\x81\x03\x0f\x79\x9e\xf7\x9e\x2c\xcb\x22\x12\xe2\x15\xfe\
\x94\xb4\x30\xd3\xfa\xd7\xa5\xed\xc3\x7e\x5c\xfa\x66\xe9\x66\x31\
\x80\x10\x22\x95\xff\x9d\x89\xe3\xf8\xf5\x60\x1e\x93\xb4\x73\x36\
\xcd\x66\xf3\xb2\xe9\xe8\x92\xc6\x20\x34\xad\x38\x68\x27\x9e\x95\
\xad\x13\x4d\x97\x98\x85\xd2\x0e\x0b\x41\x10\xbc\x59\x4d\x8a\x6b\
\x8e\x39\x9a\x0d\xfb\x7b\x79\x9e\xd3\x1a\xa6\xcd\x4a\xa1\xda\xd3\
\xc4\x6b\x6b\x6b\x6f\x03\xe9\xe2\xe4\x88\xe8\x3c\xf7\xdc\x73\x0f\
\x8d\x8e\x8e\x7e\x71\xcf\x9e\x3d\xef\x66\x8c\x65\x00\xe0\x50\x3f\
\x24\x44\x44\xc6\x98\x60\x8c\x55\x85\x10\x2f\x39\x8e\xf3\x9e\xd1\
\xd1\xd1\x33\x26\xee\x96\x84\x41\x6b\x9d\xfb\x87\xae\xb9\xe6\x9a\
\x7f\x05\x00\xb9\x34\x91\x06\x87\x2a\x9c\x1c\x00\x2a\x64\x09\xf3\
\x3c\x3f\xef\x38\x4e\x40\x65\x40\x42\x08\xc7\x71\x1c\x46\xd6\x5b\
\x3e\xa5\xda\x5f\x54\xf9\x3d\x08\x21\x98\xe3\x38\x20\x84\x40\xc7\
\x71\x84\xf2\x3e\x94\xf7\x03\x3a\x2c\xc5\x06\xab\x21\x84\xa0\xfb\
\x76\xb0\x5a\xad\x1e\x6c\xbf\x51\xba\x1b\x57\xef\x32\x5c\x35\x2a\
\x88\x98\x31\xc6\x6e\xac\x54\x2a\xbf\xc1\x18\x7b\x97\x49\x95\xaf\
\x8c\x73\x2a\x8c\xb1\x47\x83\x20\x18\x1f\x19\x19\xf9\x9c\xeb\xba\
\x7b\x01\x80\x53\x0e\x51\x5e\x4f\x21\xdd\x3f\x37\x8e\xe3\x3f\x3c\
\x7d\xfa\xf4\xd7\x11\xd1\x21\x21\x30\xc6\x18\x9e\x3b\x77\xee\xc6\
\xa3\x47\x8f\x3e\xe8\xba\xee\x3d\xdd\x3e\x8c\x73\xfe\xa4\x10\xe2\
\xbd\xfd\x88\x44\x4e\x16\x88\xa5\xa5\xa5\xbf\x7b\xfd\xf5\xd7\x7f\
\x8b\x31\x46\x03\x82\xce\x85\xbe\x98\xee\xa1\x77\x1c\x1a\x7c\x42\
\x88\x55\x00\x78\x90\x73\xfe\xc8\xdc\xdc\xdc\x13\x69\x9a\xc6\xd0\
\x9a\x71\x71\xf6\xec\xd9\xc3\x46\x46\x46\x58\xb5\x5a\x65\x6b\x6b\
\x6b\xec\xf0\xe1\xc3\xb8\xb6\xb6\xc6\x8e\x1c\x39\x02\x00\x00\x95\
\x4a\x85\x55\x2a\x15\xd6\x68\x34\xda\x5f\x38\xcb\x32\xcc\xb2\x0c\
\x5d\xd7\x65\x00\x00\x87\x0e\x1d\xc2\x4a\xa5\xc2\xa0\x55\x5a\x0e\
\x87\x0e\x1d\xc2\x7a\xbd\xce\xb2\x2c\xbb\x4c\x28\xd7\x5d\x77\x1d\
\x8e\x8c\x8c\x38\x8d\x46\x83\x5d\x77\xdd\x75\x07\x8f\x1e\x3d\x7a\
\x2f\x63\xec\x87\x10\xf1\x1f\x57\xab\xd5\x8a\x22\xea\x81\x65\x93\
\xb8\x41\x30\xc6\x58\x96\x65\x2f\xbd\xf4\xd2\x4b\x6f\xbc\xed\xb6\
\xdb\x52\x1a\xb3\x06\xc7\x77\x19\x63\x59\xa3\xd1\xb8\x77\xff\xfe\
\xfd\xc7\x2b\x95\xca\xd1\x6e\xef\x4b\xd3\xf4\xcf\x7c\xdf\xff\xe9\
\xc3\x87\x0f\x7b\x9d\x07\x60\x20\x73\x20\x9e\xe7\xfd\xdb\x2c\xcb\
\x9e\xce\xf3\xdc\x13\x42\x84\x9c\xf3\xa7\xc2\x30\xfc\x79\xaa\xe4\
\xed\x67\x71\x3e\xfd\xed\xfc\xfc\xfc\xdb\xd3\x34\x15\xb4\x8b\x52\
\xa7\xe9\x2d\x01\x54\xd3\xf6\xb9\xf5\xf5\xf5\x9b\x4d\xaf\xc7\x4e\
\xb0\xbc\xbc\x7c\x3b\xe7\xfc\x49\xd4\x6f\x80\xbd\xe3\x6c\x35\x65\
\x9c\xa6\xe9\xf4\xe9\xd3\xa7\xf7\x83\x32\x5e\x4d\xa0\x31\x38\x3b\
\x3b\xfb\x6a\xdf\xf7\x3f\xc8\x39\x7f\x31\xcf\x73\xc1\x39\x6f\x72\
\xce\xbf\xe2\xfb\xfe\x4f\x29\xef\xed\x3a\xe3\x70\xd9\x0f\xeb\xf5\
\xfa\x2d\x71\x1c\xdf\xda\xf1\x9e\xbe\xcc\xb7\x22\x94\xb7\xa5\x69\
\x2b\xe4\x29\x99\x50\xd4\x6a\xd3\x9a\xf2\xbd\x5c\xaa\x3a\x1d\x84\
\x57\xad\x56\x73\xe4\x62\xa4\x0a\xb4\x4a\x82\xf6\xd4\xeb\xf5\x3f\
\x90\xdf\x61\x60\xeb\xe6\xb6\x12\x4a\x96\x65\x67\x16\x16\x16\xfa\
\x16\x0a\x74\x24\xc5\xa7\xa7\xa7\xf7\x24\x49\x72\x9b\xfa\xc0\xbb\
\x62\x7b\x25\xb5\x13\x7c\xe7\xcf\xb6\x63\x6d\x31\x1d\xfb\x95\x57\
\x5e\xf9\x01\xd9\xf9\x12\xcb\x14\x6c\x2a\x9b\xd7\xfc\x26\x5c\x4a\
\x96\x0e\xb4\xef\xaf\xde\x4f\x65\xef\xca\x81\xb6\x2c\x1d\x90\x50\
\xce\x4e\x4d\x4d\x5d\x03\xdb\x20\x14\xb8\xc2\x58\xef\x7c\xef\x86\
\x1b\xcc\x18\x43\x8a\x3d\x68\x10\xd0\xcf\x4c\x7c\xc2\xcd\x70\x5d\
\x57\x27\xf1\x33\x28\xe4\x00\x50\x89\xe3\xf8\xd4\xbe\x7d\xfb\x7e\
\x89\x2e\xa8\x8c\xb3\x06\x16\x9a\xb0\x41\x44\x96\xa6\xe9\xbf\x4c\
\xd3\xf4\x9c\x14\xf7\x40\x9f\x77\x27\xdb\x1d\xb7\xd2\xb8\xa6\x99\
\x34\x75\xac\x77\xbe\x77\xcb\x27\xa1\x9c\xe9\xda\xd6\x8b\x79\xf2\
\xe4\x49\x80\x56\xc0\xca\x84\x28\xd5\x7d\xa2\x99\xa7\xdc\x75\xdd\
\xfb\xe8\x87\x83\x2e\x12\x42\x9e\x67\xe5\xc0\x81\x03\xab\x42\x88\
\xff\x21\x07\x5d\xd9\x72\x2d\xa2\x73\x02\x63\x3b\x90\xe2\xd8\x72\
\xac\x17\xe6\x32\x54\x2a\x95\x52\x0c\x30\x05\x94\xdd\x0e\x5f\xac\
\x56\xab\xa7\xe4\xac\x8b\xc9\xd4\x78\x91\xe4\x88\xc8\xc2\x30\xfc\
\x9c\x10\x62\x49\xce\x80\x95\x49\x2c\x78\xf8\xf0\xe1\x42\xc6\xcd\
\x8e\x0b\x65\x7c\x7c\x1c\xa1\xe5\xd6\xe5\xb8\x55\x0d\xc1\xe0\x21\
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
